shanshe/Z3660/z3660-firmware/Z-TURN/vitis_ide/Z3660_system/sd_card/README.txt

-= SD card boot image =-

Platform: design_1_wrapper
Application: design_1_wrapper

1. Copy the contents of this directory to an SD card
2. Set boot mode to SD
3. Insert SD card and turn board on
