shanshe/Z3660/z3660-board/Z3660_kicad/Z3660_kicad9-023/Sheet1.kicad_sch

## KiCad design z3660-board/Z3660_kicad/Z3660_kicad9-023/Sheet1.kicad_sch (2026-05-13)

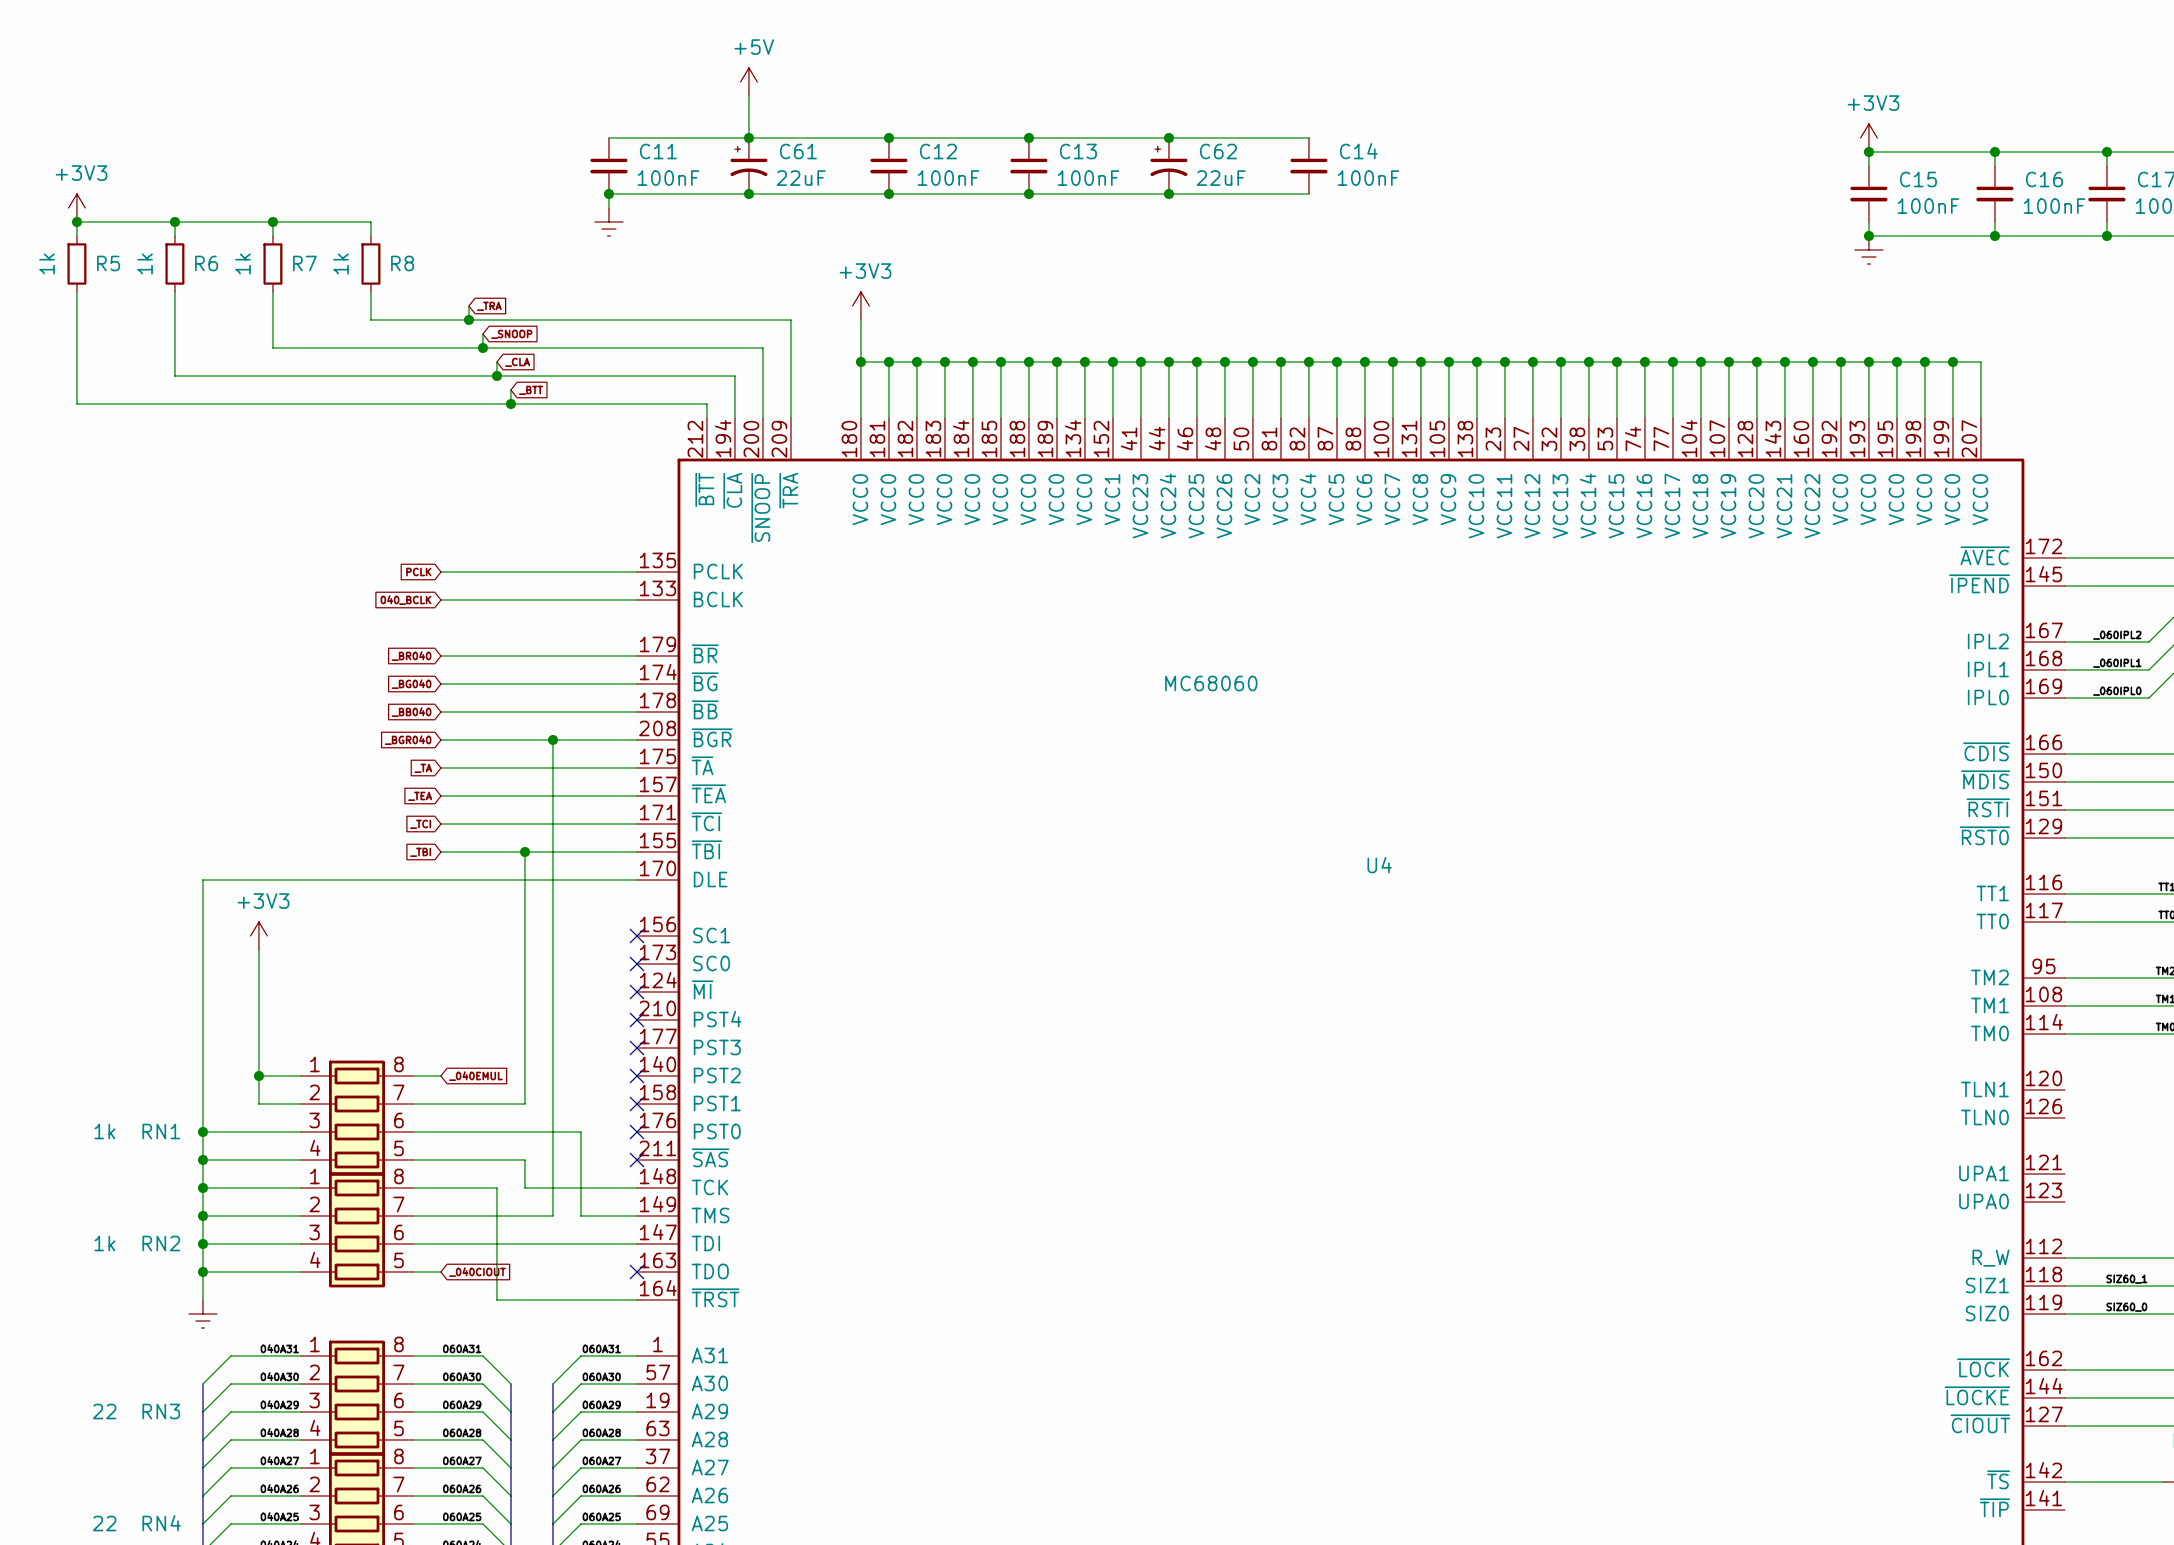
[picture p31: schematic Sheet1.kicad_sch, part in row 1, column 1]

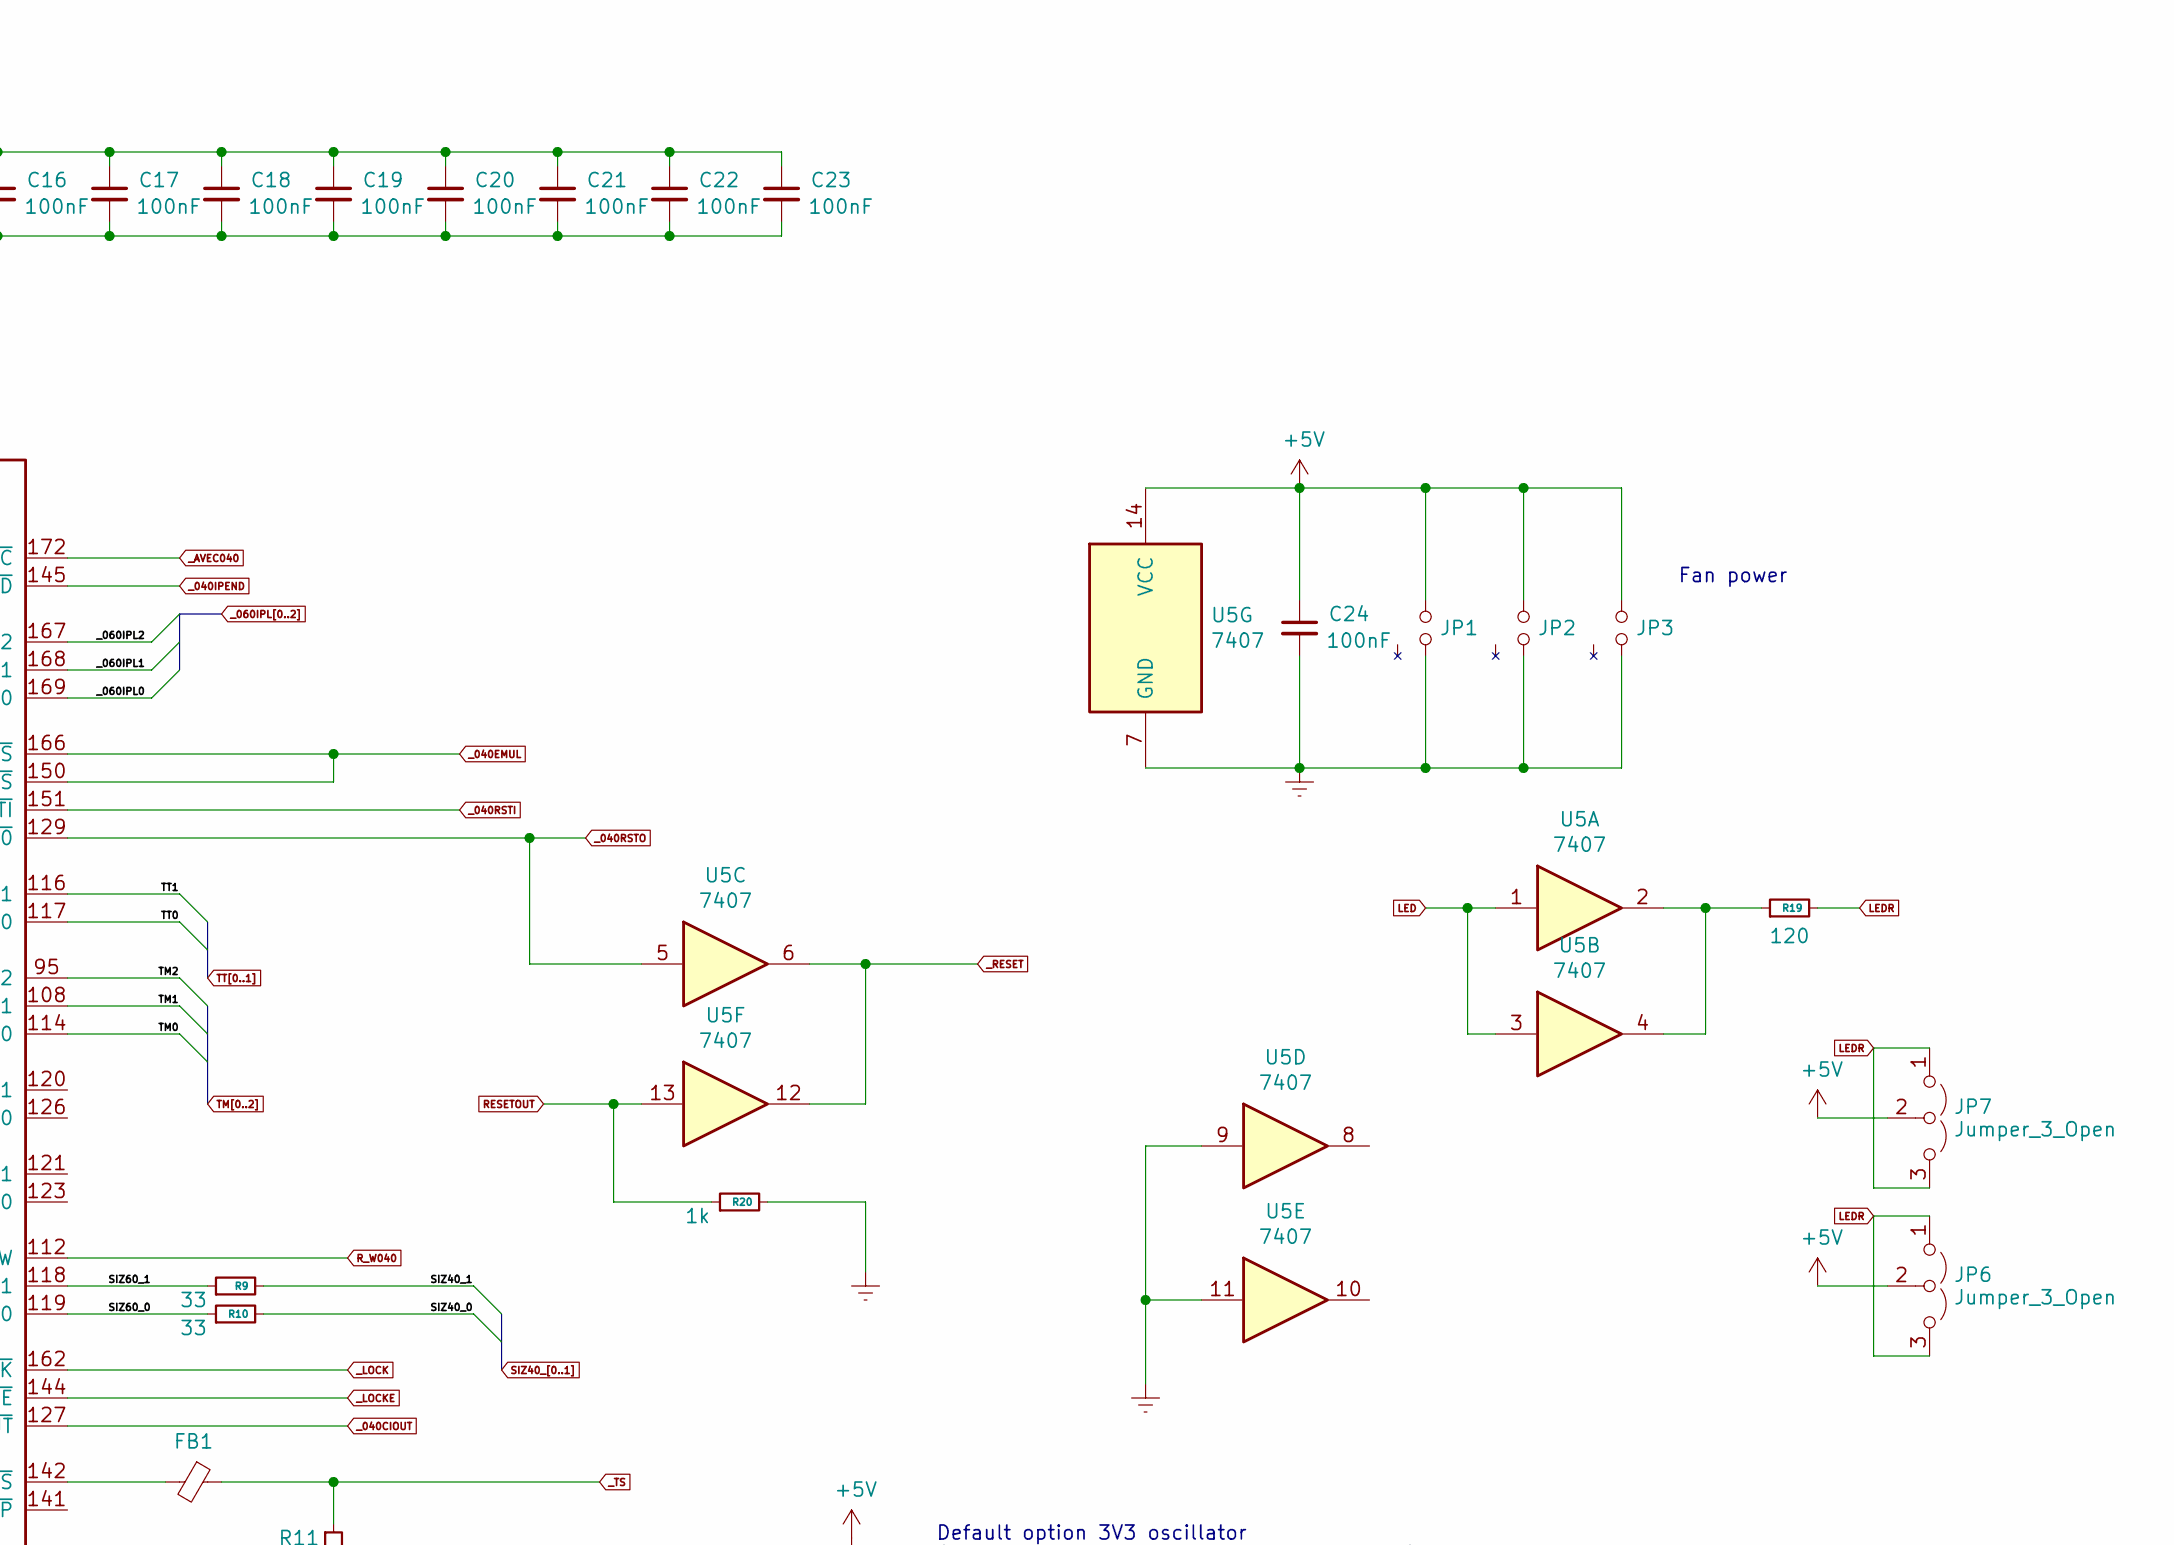
[picture p32: schematic Sheet1.kicad_sch, part in row 1, column 2]

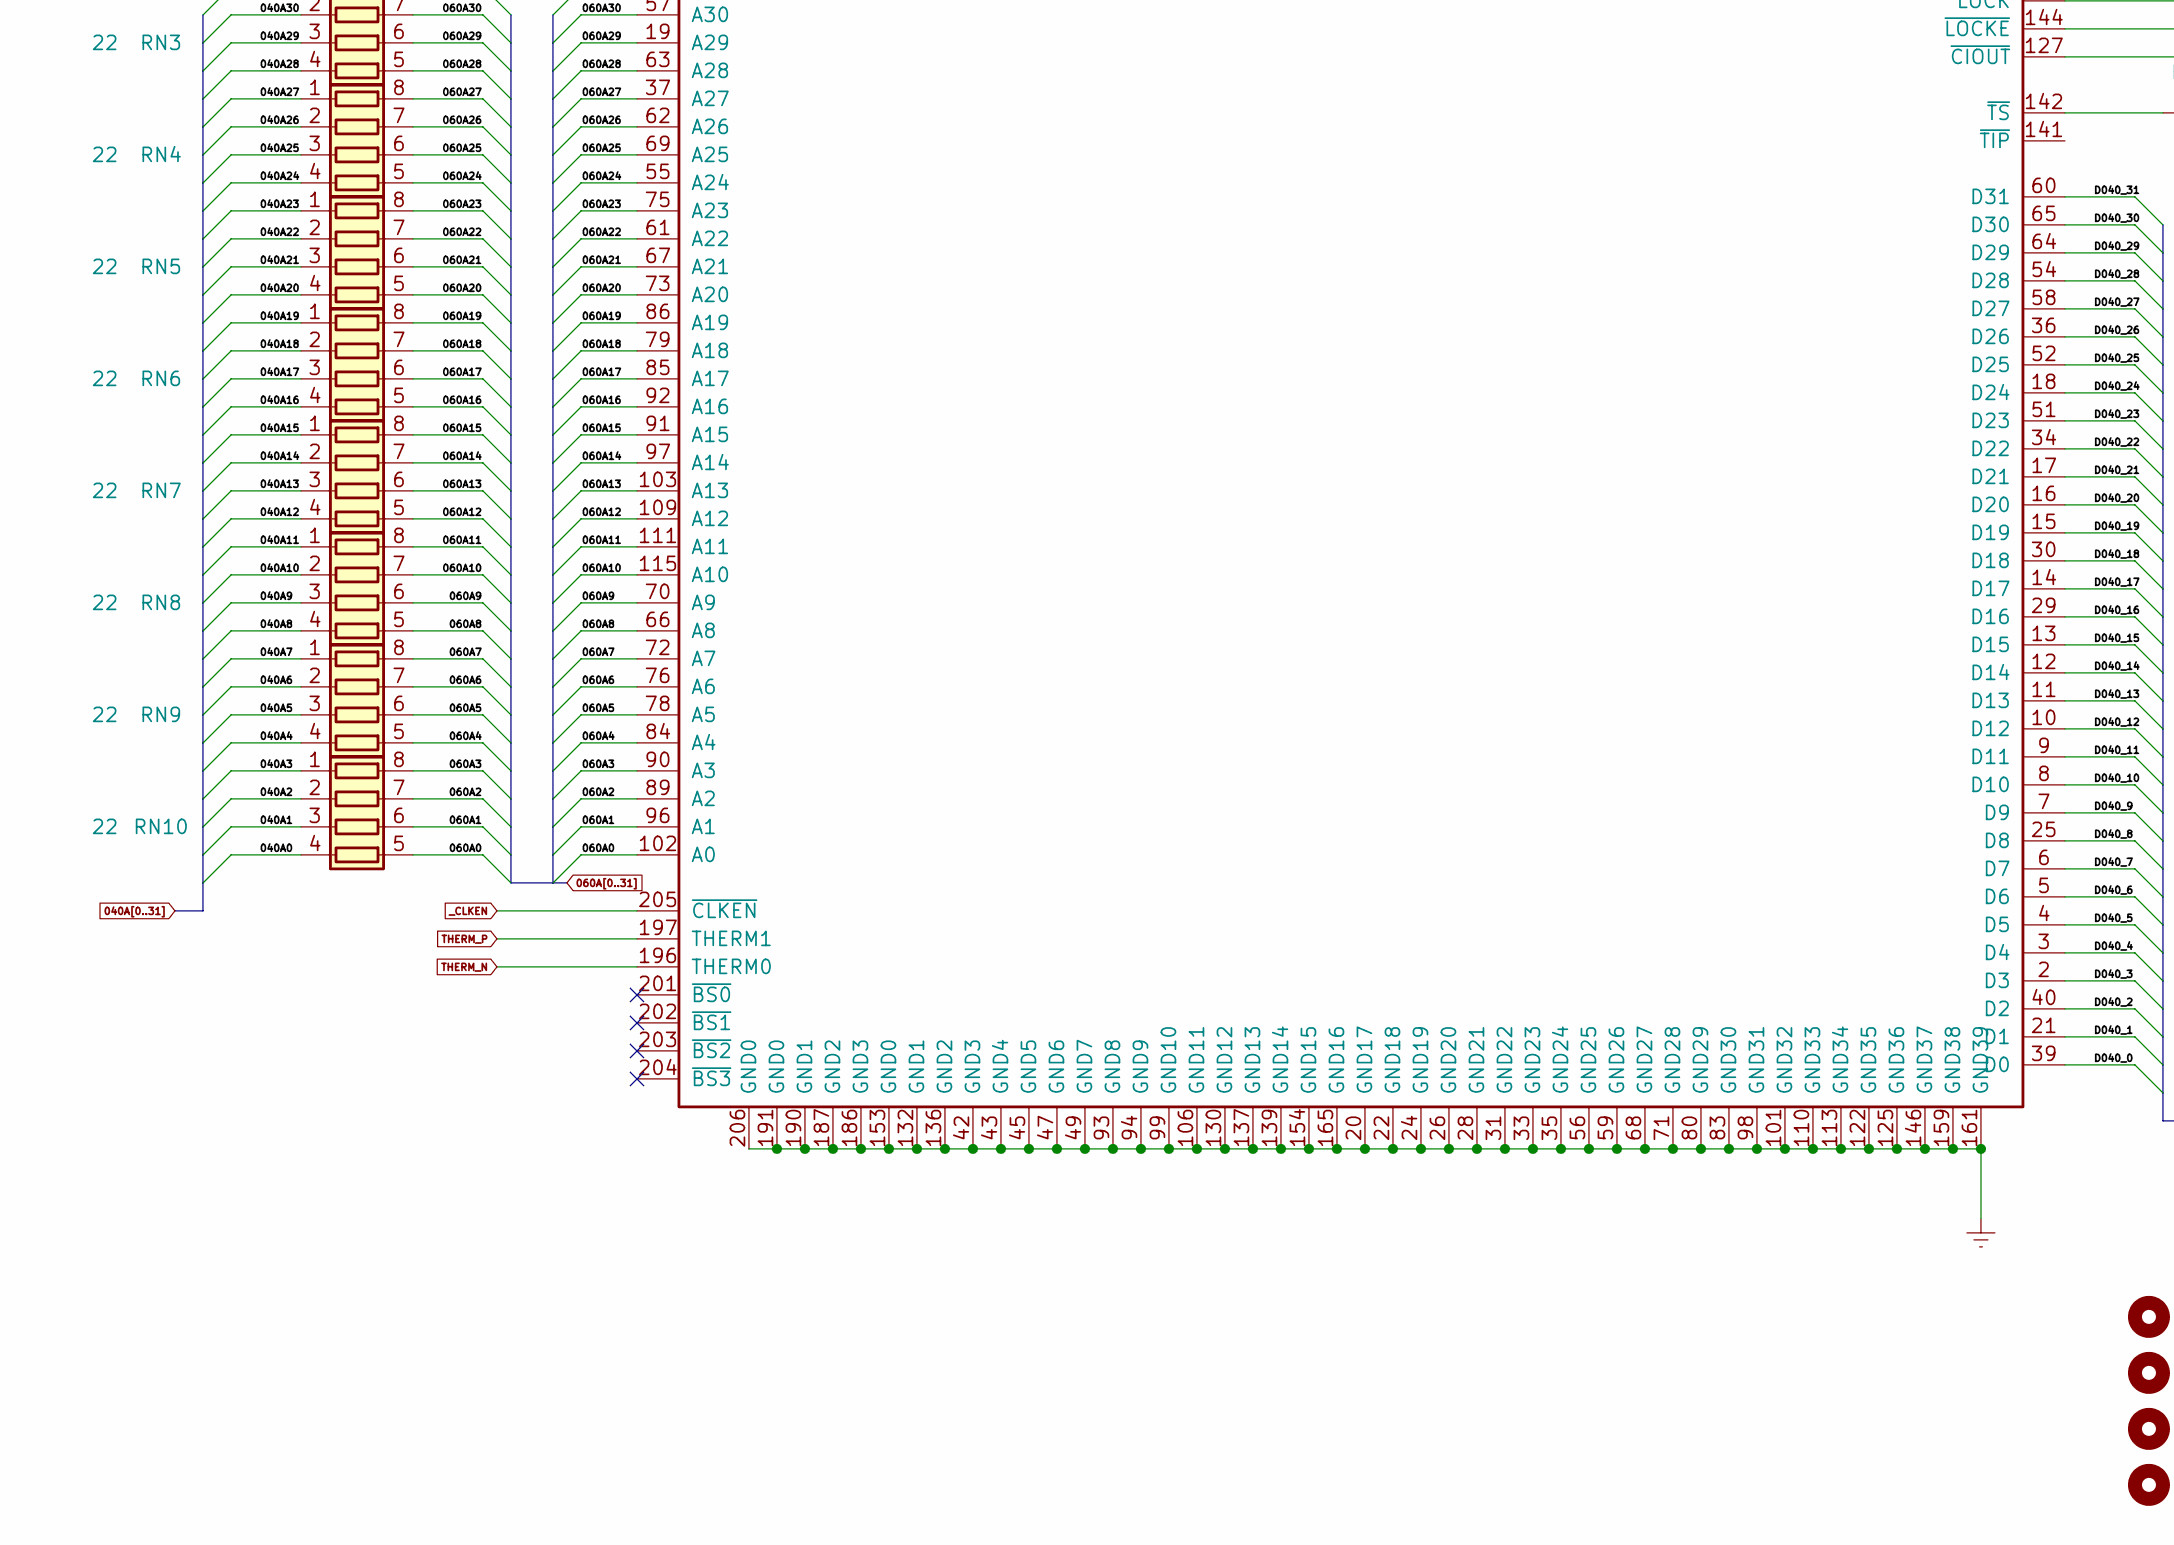
[picture p33: schematic Sheet1.kicad_sch, part in row 2, column 1]

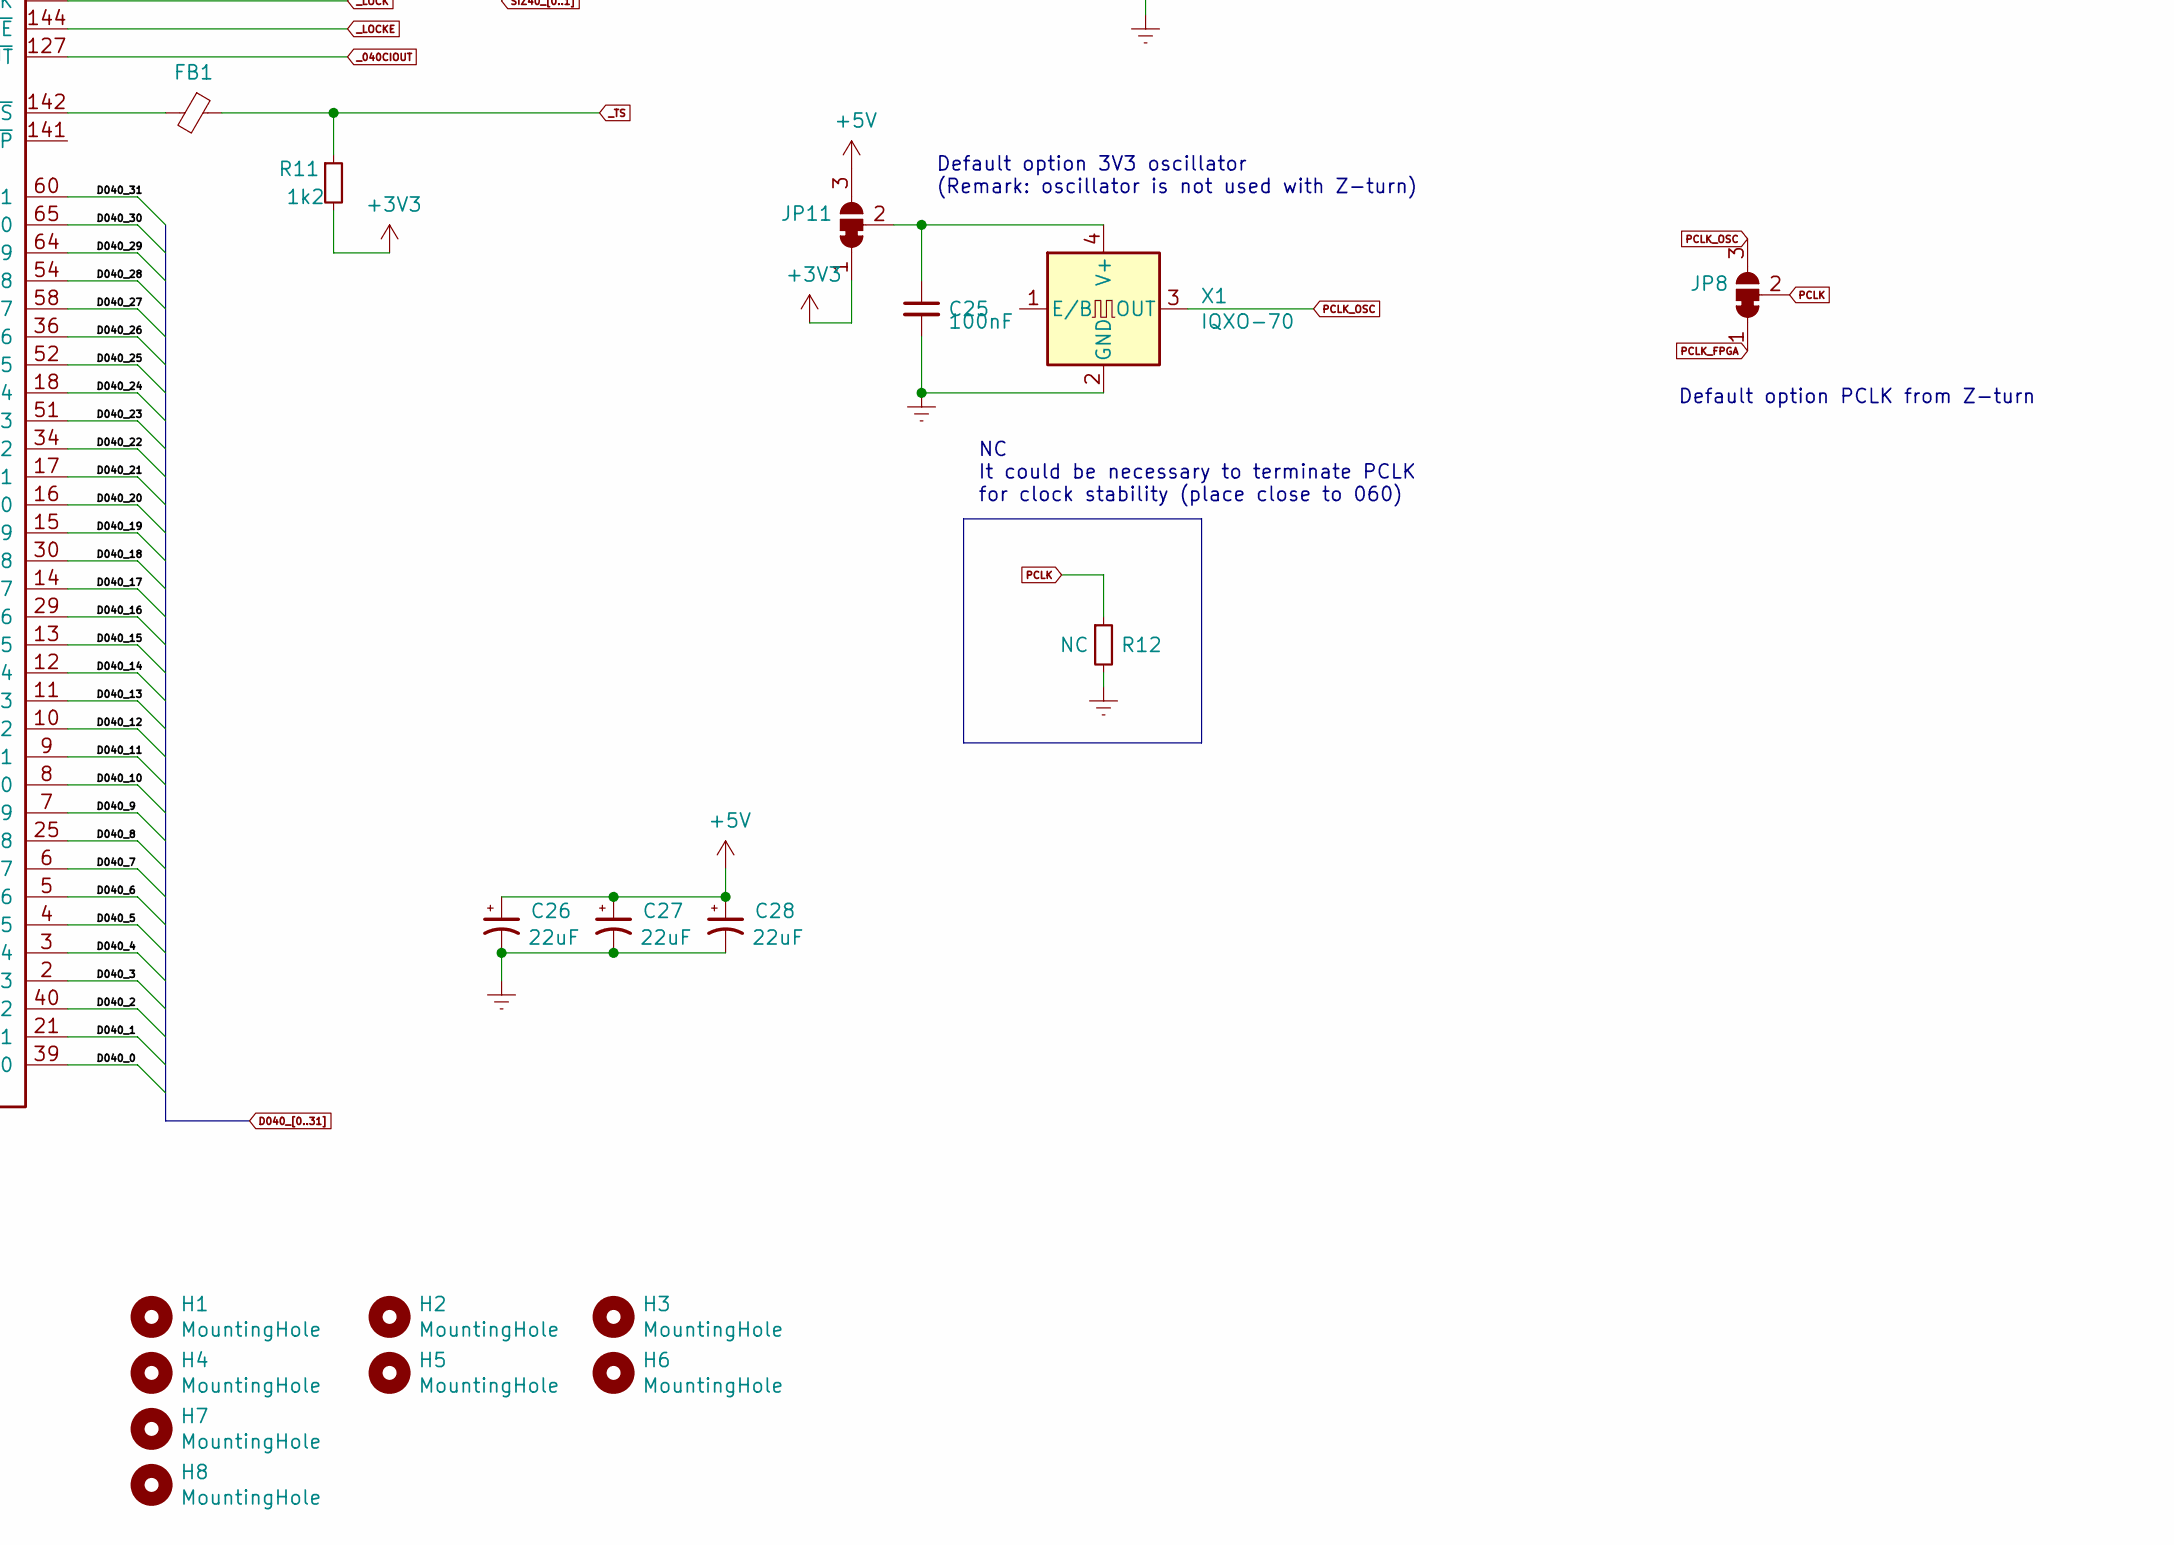
[picture p34: schematic Sheet1.kicad_sch, part in row 2, column 2]

Parts:
C11, C12, C13, C14, C15, C16, C17, C18, C19, C20, C21, C22, C23, C24, C25: 100nF; C_0805_2012Metric_Pad1.18x1.45mm_HandSolder
C26, C28, C61, C62: 22uF; CP_Elec_6.3x5.4
C27: 22uF; CP_Elec_6.3x3.9
FB1: Ferrite_Bead_Small; Fuse_1806_4516Metric_Pad1.57x1.80mm_HandSolder
H1, H2, H3, H4: MountingHole; MountingHole_4mm
H5, H6, H7, H8: MountingHole; MountingHole_2.2mm_M2
JP1, JP3: Jumper_NO_Small; PinHeader_1x03_P2.54mm_Horizontal
JP2, JP6, JP7: Jumper_3_Open; PinHeader_1x03_P2.54mm_Vertical
JP8, JP11: SolderJumper_3_Bridged12; SolderJumper-3_P1.3mm_Bridged12_RoundedPad1.0x1.5mm_NumberL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
R5, R6, R7, R8, R20: 1k; R_0805_2012Metric_Pad1.20x1.40mm_HandSolder
R9, R10: 33; R_0805_2012Metric_Pad1.20x1.40mm_HandSolder
R11: 1k2; R_0805_2012Metric_Pad1.20x1.40mm_HandSolder
R12: NC; R_0805_2012Metric_Pad1.20x1.40mm_HandSolder
R19: 120; R_0805_2012Metric_Pad1.20x1.40mm_HandSolder
RN1, RN2: 1k; R_Array_Convex_4x0603
RN3, RN4, RN5, RN6, RN7, RN8, RN9, RN10: 22; R_Array_Convex_4x0603
U4: MC68060; PGA226
U5: 7407; SOIC-14_3.9x8.7mm_P1.27mm
X1: IQXO-70; Oscillator_SMD_IQD_IQXO70-4Pin_7.5x5.0mm

Connections:
040A0: RN10.4 (R4.1)
040A1: RN10.3 (R3.1)
040A2: RN10.2 (R2.1)
040A3: RN10.1 (R1.1)
040A4: RN9.4 (R4.1)
040A5: RN9.3 (R3.1)
040A6: RN9.2 (R2.1)
040A7: RN9.1 (R1.1)
040A8: RN8.4 (R4.1)
040A9: RN8.3 (R3.1)
040A10: RN8.2 (R2.1)
040A11: RN8.1 (R1.1)
040A12: RN7.4 (R4.1)
040A13: RN7.3 (R3.1)
040A14: RN7.2 (R2.1)
040A15: RN7.1 (R1.1)
040A16: RN6.4 (R4.1)
040A17: RN6.3 (R3.1)
040A18: RN6.2 (R2.1)
040A19: RN6.1 (R1.1)
040A20: RN5.4 (R4.1)
040A21: RN5.3 (R3.1)
040A22: RN5.2 (R2.1)
040A23: RN5.1 (R1.1)
040A24: RN4.4 (R4.1)
040A25: RN4.3 (R3.1)
040A26: RN4.2 (R2.1)
040A27: RN4.1 (R1.1)
040A28: RN3.4 (R4.1)
040A29: RN3.3 (R3.1)
040A30: RN3.2 (R2.1)
040A31: RN3.1 (R1.1)
040_BCLK: U4.133 (BCLK)
060A0: RN10.5 (R4.2), U4.102 (A0)
060A1: RN10.6 (R3.2), U4.96 (A1)
060A2: RN10.7 (R2.2), U4.89 (A2)
060A3: RN10.8 (R1.2), U4.90 (A3)
060A4: RN9.5 (R4.2), U4.84 (A4)
060A5: RN9.6 (R3.2), U4.78 (A5)
060A6: RN9.7 (R2.2), U4.76 (A6)
060A7: RN9.8 (R1.2), U4.72 (A7)
060A8: RN8.5 (R4.2), U4.66 (A8)
060A9: RN8.6 (R3.2), U4.70 (A9)
060A10: RN8.7 (R2.2), U4.115 (A10)
060A11: RN8.8 (R1.2), U4.111 (A11)
060A12: RN7.5 (R4.2), U4.109 (A12)
060A13: RN7.6 (R3.2), U4.103 (A13)
060A14: RN7.7 (R2.2), U4.97 (A14)
060A15: RN7.8 (R1.2), U4.91 (A15)
060A16: RN6.5 (R4.2), U4.92 (A16)
060A17: RN6.6 (R3.2), U4.85 (A17)
060A18: RN6.7 (R2.2), U4.79 (A18)
060A19: RN6.8 (R1.2), U4.86 (A19)
060A20: RN5.5 (R4.2), U4.73 (A20)
060A21: RN5.6 (R3.2), U4.67 (A21)
060A22: RN5.7 (R2.2), U4.61 (A22)
060A23: RN5.8 (R1.2), U4.75 (A23)
060A24: RN4.5 (R4.2), U4.55 (A24)
060A25: RN4.6 (R3.2), U4.69 (A25)
060A26: RN4.7 (R2.2), U4.62 (A26)
060A27: RN4.8 (R1.2), U4.37 (A27)
060A28: RN3.5 (R4.2), U4.63 (A28)
060A29: RN3.6 (R3.2), U4.19 (A29)
060A30: RN3.7 (R2.2), U4.57 (A30)
060A31: RN3.8 (R1.2), U4.1 (A31)
+3V3: C15.1, C16.1, C17.1, C18.1, C19.1, C20.1, C21.1, C22.1, C23.1, JP11.1 (A), R5.1, R6.1, R7.1, R8.1, R11.2, RN1.1 (R1.1), RN1.2 (R2.1), U4.23 (VCC11), U4.27 (VCC12), U4.32 (VCC13), U4.38 (VCC14), U4.41 (VCC23), U4.44 (VCC24), U4.46 (VCC25), U4.48 (VCC26), U4.50 (VCC2), U4.53 (VCC15), U4.74 (VCC16), U4.77 (VCC17), U4.81 (VCC3), U4.82 (VCC4), U4.87 (VCC5), U4.88 (VCC6), U4.100 (VCC7), U4.104 (VCC18), U4.105 (VCC9), U4.107 (VCC19), U4.128 (VCC20), U4.131 (VCC8), U4.134 (VCC0), U4.138 (VCC10), U4.143 (VCC21), U4.152 (VCC1), U4.160 (VCC22), U4.180 (VCC0), U4.181 (VCC0), U4.182 (VCC0), U4.183 (VCC0), U4.184 (VCC0), U4.185 (VCC0), U4.188 (VCC0), U4.189 (VCC0), U4.192 (VCC0), U4.193 (VCC0), U4.195 (VCC0), U4.198 (VCC0), U4.199 (VCC0), U4.207 (VCC0)
+5V: C11.1, C12.1, C13.1, C14.1, C24.1, C26.1, C27.1, C28.1, C61.1, C62.1, JP1.2, JP2.2, JP3.2, JP6.2 (C), JP7.2 (C), JP11.3 (B), U5.14 (VCC)
D040_0: U4.39 (D0)
D040_1: U4.21 (D1)
D040_2: U4.40 (D2)
D040_3: U4.2 (D3)
D040_4: U4.3 (D4)
D040_5: U4.4 (D5)
D040_6: U4.5 (D6)
D040_7: U4.6 (D7)
D040_8: U4.25 (D8)
D040_9: U4.7 (D9)
D040_10: U4.8 (D10)
D040_11: U4.9 (D11)
D040_12: U4.10 (D12)
D040_13: U4.11 (D13)
D040_14: U4.12 (D14)
D040_15: U4.13 (D15)
D040_16: U4.29 (D16)
D040_17: U4.14 (D17)
D040_18: U4.30 (D18)
D040_19: U4.15 (D19)
D040_20: U4.16 (D20)
D040_21: U4.17 (D21)
D040_22: U4.34 (D22)
D040_23: U4.51 (D23)
D040_24: U4.18 (D24)
D040_25: U4.52 (D25)
D040_26: U4.36 (D26)
D040_27: U4.58 (D27)
D040_28: U4.54 (D28)
D040_29: U4.64 (D29)
D040_30: U4.65 (D30)
D040_31: U4.60 (D31)
Earth: C11.2, C12.2, C13.2, C14.2, C15.2, C16.2, C17.2, C18.2, C19.2, C20.2, C21.2, C22.2, C23.2, C24.2, C25.2, C26.2, C27.2, C28.2, C61.2, C62.2, JP1.1, JP2.1, JP3.1, R12.2, R20.2, RN1.3 (R3.1), RN1.4 (R4.1), RN2.1 (R1.1), RN2.2 (R2.1), RN2.3 (R3.1), RN2.4 (R4.1), U4.20 (GND17), U4.22 (GND18), U4.24 (GND19), U4.26 (GND20), U4.28 (GND21), U4.31 (GND22), U4.33 (GND23), U4.35 (GND24), U4.42 (GND3), U4.43 (GND4), U4.45 (GND5), U4.47 (GND6), U4.49 (GND7), U4.56 (GND25), U4.59 (GND26), U4.68 (GND27), U4.71 (GND28), U4.80 (GND29), U4.83 (GND30), U4.93 (GND8), U4.94 (GND9), U4.98 (GND31), U4.99 (GND10), U4.101 (GND32), U4.106 (GND11), U4.110 (GND33), U4.113 (GND34), U4.122 (GND35), U4.125 (GND36), U4.130 (GND12), U4.132 (GND1), U4.136 (GND2), U4.137 (GND13), U4.139 (GND14), U4.146 (GND37), U4.153 (GND0), U4.154 (GND15), U4.159 (GND38), U4.161 (GND39), U4.165 (GND16), U4.170 (DLE), U4.186 (GND3), U4.187 (GND2), U4.190 (GND1), U4.191 (GND0), U4.206 (GND0), U5.7 (GND), U5.9, U5.11, X1.2 (GND)
LED: U5.1, U5.3
LEDR: JP6.1 (A), JP6.3 (B), JP7.1 (A), JP7.3 (B), R19.2
unnamed: C25.1, JP11.2 (C), X1.4 (V+)
unnamed: FB1.2, U4.142 (~TS)
unnamed: R19.1, U5.2, U5.4
unnamed: RN1.5 (R4.2), U4.148 (TCK)
unnamed: RN1.6 (R3.2), U4.149 (TMS)
unnamed: RN2.6 (R3.2), U4.147 (TDI)
unnamed: RN2.8 (R1.2), U4.164 (~TRST)
PCLK: JP8.2 (C), R12.1, U4.135 (PCLK)
PCLK_FPGA: JP8.1 (A)
PCLK_OSC: JP8.3 (B), X1.3 (OUT)
RESETOUT: R20.1, U5.13
R_W040: U4.112 (R_W)
SIZ40_0: R10.2
SIZ40_1: R9.2
SIZ60_0: R10.1, U4.119 (SIZ0)
SIZ60_1: R9.1, U4.118 (SIZ1)
THERM_N: U4.196 (THERM0)
THERM_P: U4.197 (THERM1)
TM0: U4.114 (TM0)
TM1: U4.108 (TM1)
TM2: U4.95 (TM2)
TT0: U4.117 (TT0)
TT1: U4.116 (TT1)
_040CIOUT: RN2.5 (R4.2), U4.127 (~CIOUT)
_040EMUL: RN1.8 (R1.2), U4.150 (~MDIS), U4.166 (~CDIS)
_040IPEND: U4.145 (~IPEND)
_040RSTI: U4.151 (~RSTI)
_040RSTO: U4.129 (~RST0), U5.5
_060IPL0: U4.169 (IPL0)
_060IPL1: U4.168 (IPL1)
_060IPL2: U4.167 (IPL2)
_AVEC040: U4.172 (~AVEC)
_BB040: U4.178 (~BB)
_BG040: U4.174 (~BG)
_BGR040: RN2.7 (R2.2), U4.208 (~BGR)
_BR040: U4.179 (~BR)
_BTT: R5.2, U4.212 (~BTT)
_CLA: R6.2, U4.194 (~CLA)
_CLKEN: U4.205 (~CLKEN)
_LOCK: U4.162 (~LOCK)
_LOCKE: U4.144 (~LOCKE)
_RESET: U5.6, U5.12
_SNOOP: R7.2, U4.200 (~SNOOP)
_TA: U4.175 (~TA)
_TBI: RN1.7 (R2.2), U4.155 (~TBI)
_TCI: U4.171 (~TCI)
_TEA: U4.157 (~TEA)
_TRA: R8.2, U4.209 (~TRA)
_TS: FB1.1, R11.1

Notes on the sheet:
Default option 3V3 oscillator (Remark: oscillator is not used with Z-turn)
Default option PCLK from Z-turn
NC It could be necessary to terminate PCLK for clock stability (place close to 060)
Fan power
