shanshe/Z3660/z3660-board/Z3660_kicad/Z3660_kicad9-023/Sheet2.kicad_sch

## KiCad design z3660-board/Z3660_kicad/Z3660_kicad9-023/Sheet2.kicad_sch (2026-05-13)

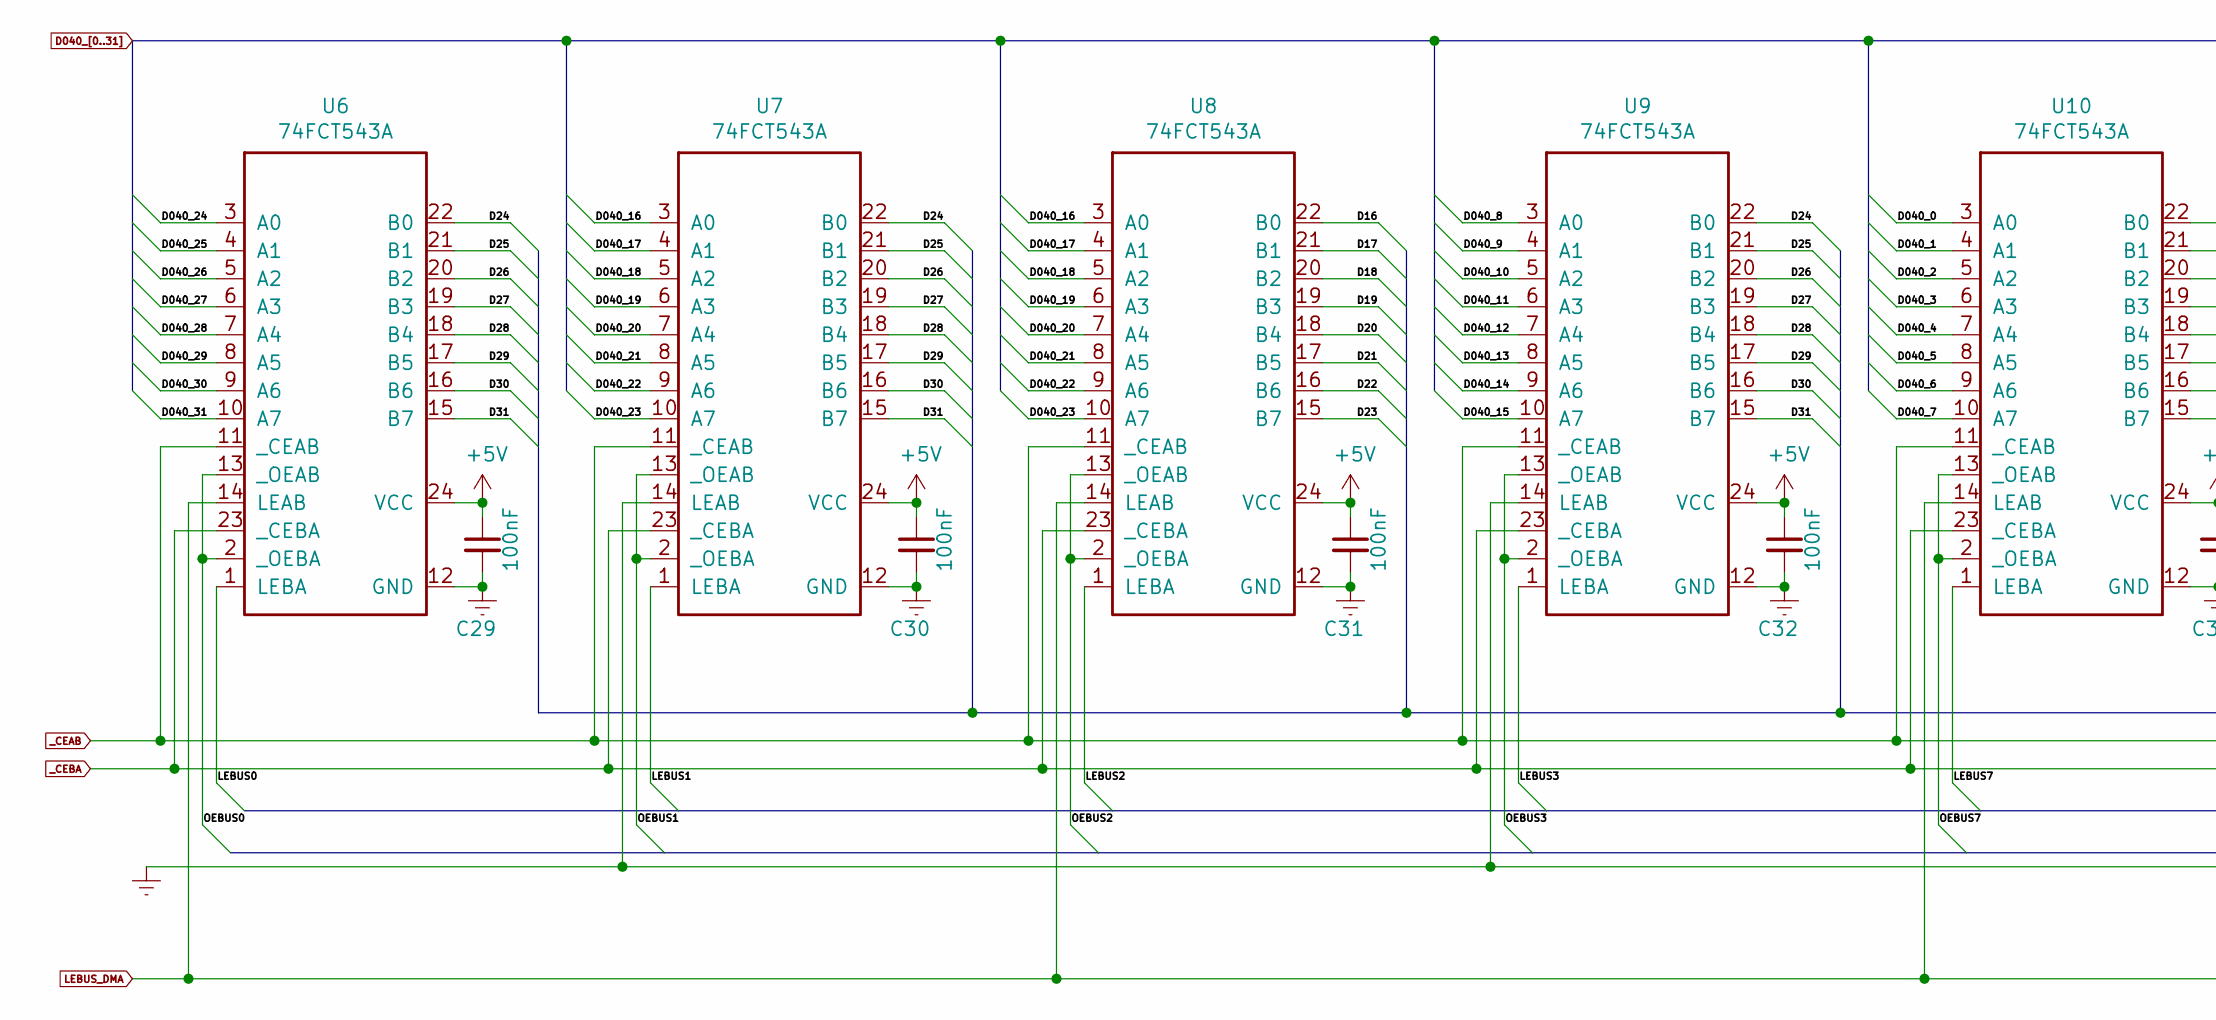
[picture p35: schematic Sheet2.kicad_sch, part in row 1, column 1]

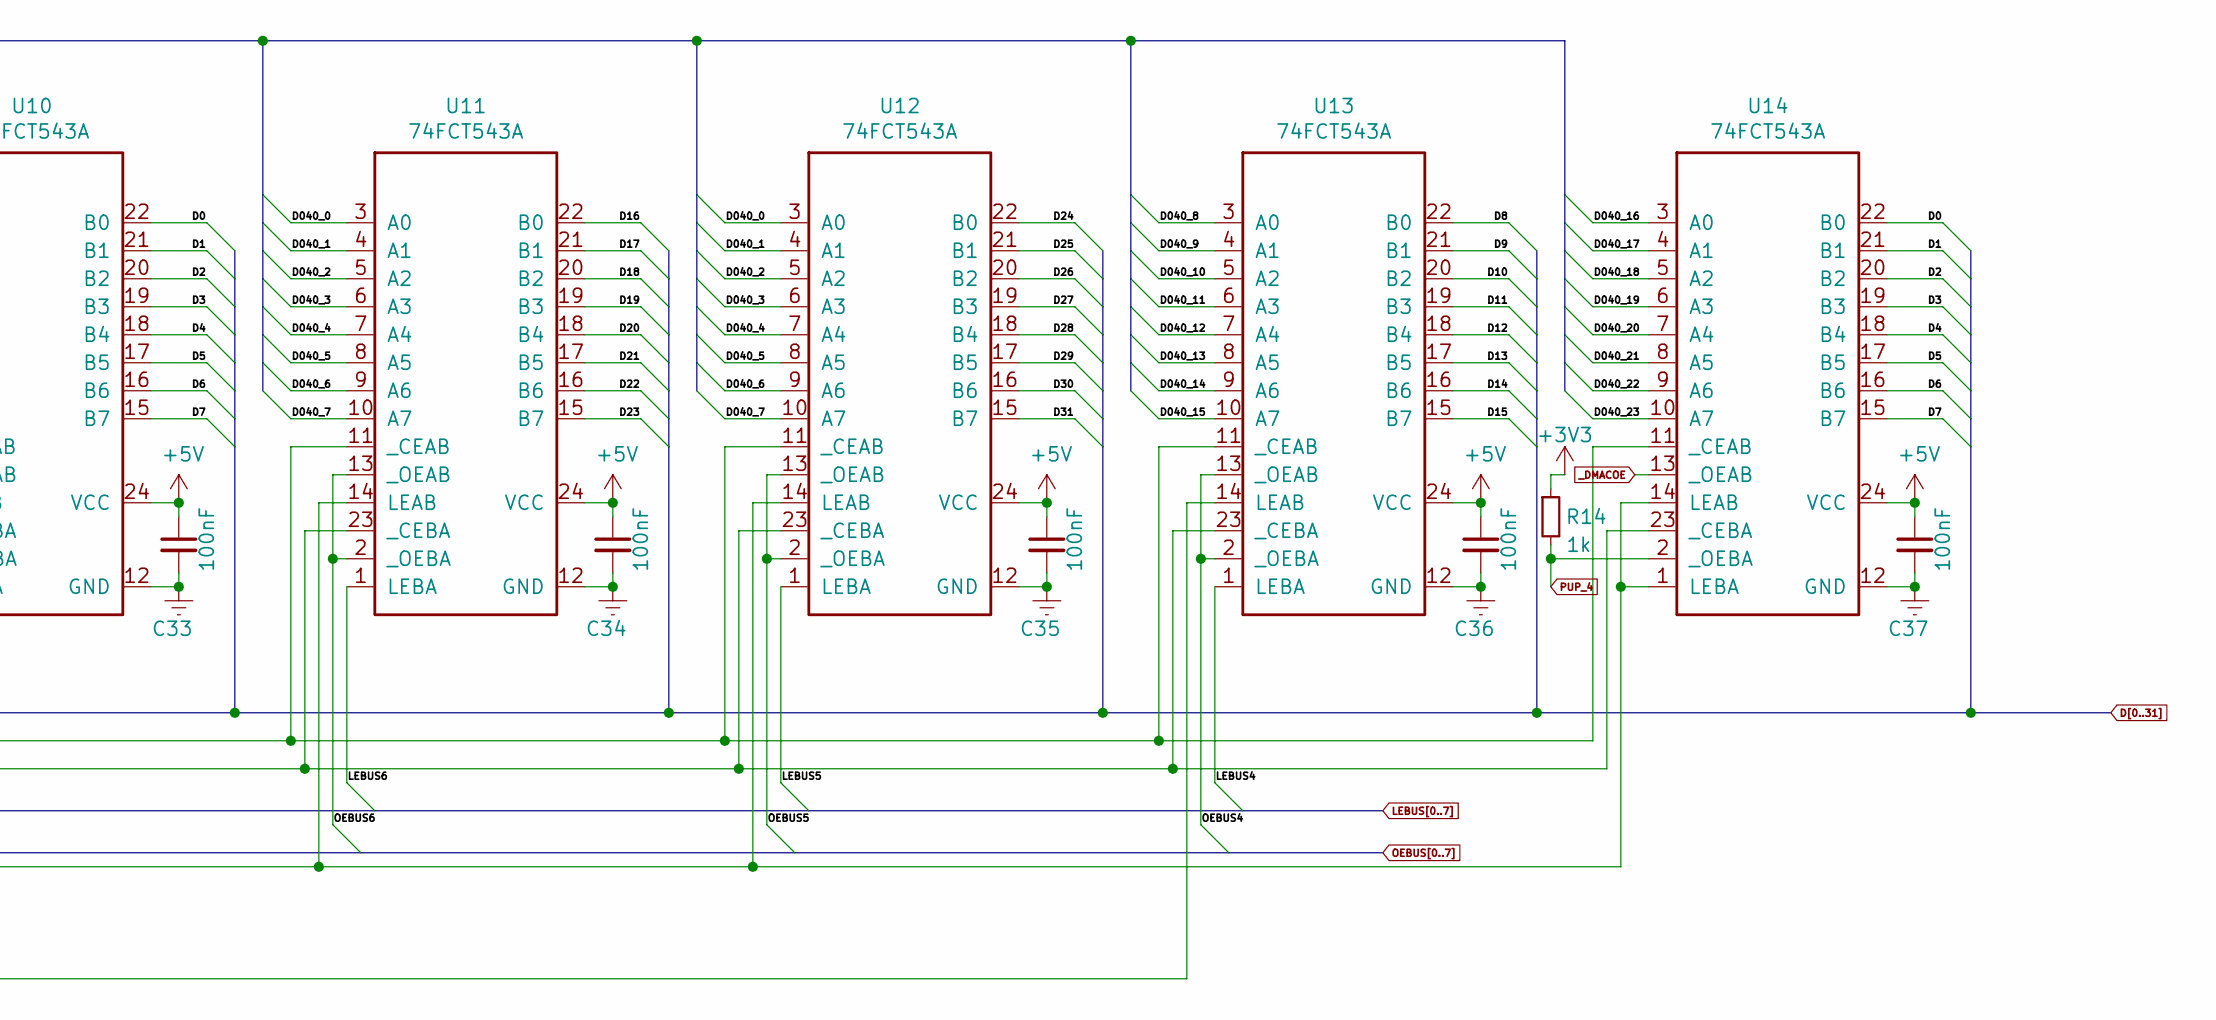
[picture p36: schematic Sheet2.kicad_sch, part in row 1, column 2]

Parts:
C29, C30, C31, C32, C33, C34, C35, C36, C37: 100nF; C_0805_2012Metric_Pad1.18x1.45mm_HandSolder
R14: 1k; R_0805_2012Metric_Pad1.20x1.40mm_HandSolder
U6, U7, U8, U9, U10, U11, U12, U13, U14: 74FCT543A; SOIC-24W_7.5x15.4mm_P1.27mm

Connections:
+3V3: R14.1
+5V: C29.1, C30.1, C31.1, C32.1, C33.1, C34.1, C35.1, C36.1, C37.1, U6.24 (VCC), U7.24 (VCC), U8.24 (VCC), U9.24 (VCC), U10.24 (VCC), U11.24 (VCC), U12.24 (VCC), U13.24 (VCC), U14.24 (VCC)
D0: U10.22 (B0), U14.22 (B0)
D1: U10.21 (B1), U14.21 (B1)
D2: U10.20 (B2), U14.20 (B2)
D3: U10.19 (B3), U14.19 (B3)
D4: U10.18 (B4), U14.18 (B4)
D5: U10.17 (B5), U14.17 (B5)
D6: U10.16 (B6), U14.16 (B6)
D7: U10.15 (B7), U14.15 (B7)
D8: U13.22 (B0)
D9: U13.21 (B1)
D10: U13.20 (B2)
D11: U13.19 (B3)
D12: U13.18 (B4)
D13: U13.17 (B5)
D14: U13.16 (B6)
D15: U13.15 (B7)
D16: U8.22 (B0), U11.22 (B0)
D17: U8.21 (B1), U11.21 (B1)
D18: U8.20 (B2), U11.20 (B2)
D19: U8.19 (B3), U11.19 (B3)
D20: U8.18 (B4), U11.18 (B4)
D21: U8.17 (B5), U11.17 (B5)
D22: U8.16 (B6), U11.16 (B6)
D23: U8.15 (B7), U11.15 (B7)
D24: U6.22 (B0), U7.22 (B0), U9.22 (B0), U12.22 (B0)
D25: U6.21 (B1), U7.21 (B1), U9.21 (B1), U12.21 (B1)
D26: U6.20 (B2), U7.20 (B2), U9.20 (B2), U12.20 (B2)
D27: U6.19 (B3), U7.19 (B3), U9.19 (B3), U12.19 (B3)
D28: U6.18 (B4), U7.18 (B4), U9.18 (B4), U12.18 (B4)
D29: U6.17 (B5), U7.17 (B5), U9.17 (B5), U12.17 (B5)
D30: U6.16 (B6), U7.16 (B6), U9.16 (B6), U12.16 (B6)
D31: U6.15 (B7), U7.15 (B7), U9.15 (B7), U12.15 (B7)
D040_0: U10.3 (A0), U11.3 (A0), U12.3 (A0)
D040_1: U10.4 (A1), U11.4 (A1), U12.4 (A1)
D040_2: U10.5 (A2), U11.5 (A2), U12.5 (A2)
D040_3: U10.6 (A3), U11.6 (A3), U12.6 (A3)
D040_4: U10.7 (A4), U11.7 (A4), U12.7 (A4)
D040_5: U10.8 (A5), U11.8 (A5), U12.8 (A5)
D040_6: U10.9 (A6), U11.9 (A6), U12.9 (A6)
D040_7: U10.10 (A7), U11.10 (A7), U12.10 (A7)
D040_8: U9.3 (A0), U13.3 (A0)
D040_9: U9.4 (A1), U13.4 (A1)
D040_10: U9.5 (A2), U13.5 (A2)
D040_11: U9.6 (A3), U13.6 (A3)
D040_12: U9.7 (A4), U13.7 (A4)
D040_13: U9.8 (A5), U13.8 (A5)
D040_14: U9.9 (A6), U13.9 (A6)
D040_15: U9.10 (A7), U13.10 (A7)
D040_16: U7.3 (A0), U8.3 (A0), U14.3 (A0)
D040_17: U7.4 (A1), U8.4 (A1), U14.4 (A1)
D040_18: U7.5 (A2), U8.5 (A2), U14.5 (A2)
D040_19: U7.6 (A3), U8.6 (A3), U14.6 (A3)
D040_20: U7.7 (A4), U8.7 (A4), U14.7 (A4)
D040_21: U7.8 (A5), U8.8 (A5), U14.8 (A5)
D040_22: U7.9 (A6), U8.9 (A6), U14.9 (A6)
D040_23: U7.10 (A7), U8.10 (A7), U14.10 (A7)
D040_24: U6.3 (A0)
D040_25: U6.4 (A1)
D040_26: U6.5 (A2)
D040_27: U6.6 (A3)
D040_28: U6.7 (A4)
D040_29: U6.8 (A5)
D040_30: U6.9 (A6)
D040_31: U6.10 (A7)
Earth: C29.2, C30.2, C31.2, C32.2, C33.2, C34.2, C35.2, C36.2, C37.2, U6.12 (GND), U7.12 (GND), U7.14 (LEAB), U8.12 (GND), U9.12 (GND), U9.14 (LEAB), U10.12 (GND), U11.12 (GND), U11.14 (LEAB), U12.12 (GND), U12.14 (LEAB), U13.12 (GND), U14.1 (LEBA), U14.12 (GND), U14.14 (LEAB)
LEBUS0: U6.1 (LEBA)
LEBUS1: U7.1 (LEBA)
LEBUS2: U8.1 (LEBA)
LEBUS3: U9.1 (LEBA)
LEBUS4: U13.1 (LEBA)
LEBUS5: U12.1 (LEBA)
LEBUS6: U11.1 (LEBA)
LEBUS7: U10.1 (LEBA)
LEBUS_DMA: U6.14 (LEAB), U8.14 (LEAB), U10.14 (LEAB), U13.14 (LEAB)
OEBUS0: U6.2 (_OEBA), U6.13 (_OEAB)
OEBUS1: U7.2 (_OEBA), U7.13 (_OEAB)
OEBUS2: U8.2 (_OEBA), U8.13 (_OEAB)
OEBUS3: U9.2 (_OEBA), U9.13 (_OEAB)
OEBUS4: U13.2 (_OEBA), U13.13 (_OEAB)
OEBUS5: U12.2 (_OEBA), U12.13 (_OEAB)
OEBUS6: U11.2 (_OEBA), U11.13 (_OEAB)
OEBUS7: U10.2 (_OEBA), U10.13 (_OEAB)
PUP_4: R14.2, U14.2 (_OEBA)
_CEAB: U6.11 (_CEAB), U7.11 (_CEAB), U8.11 (_CEAB), U9.11 (_CEAB), U10.11 (_CEAB), U11.11 (_CEAB), U12.11 (_CEAB), U13.11 (_CEAB), U14.11 (_CEAB)
_CEBA: U6.23 (_CEBA), U7.23 (_CEBA), U8.23 (_CEBA), U9.23 (_CEBA), U10.23 (_CEBA), U11.23 (_CEBA), U12.23 (_CEBA), U13.23 (_CEBA), U14.23 (_CEBA)
_DMACOE: U14.13 (_OEAB)
