shanshe/Z3660/z3660-board/Z3660_kicad/Z3660_kicad9-023/Sheet3.kicad_sch

## KiCad design z3660-board/Z3660_kicad/Z3660_kicad9-023/Sheet3.kicad_sch (2026-05-13)

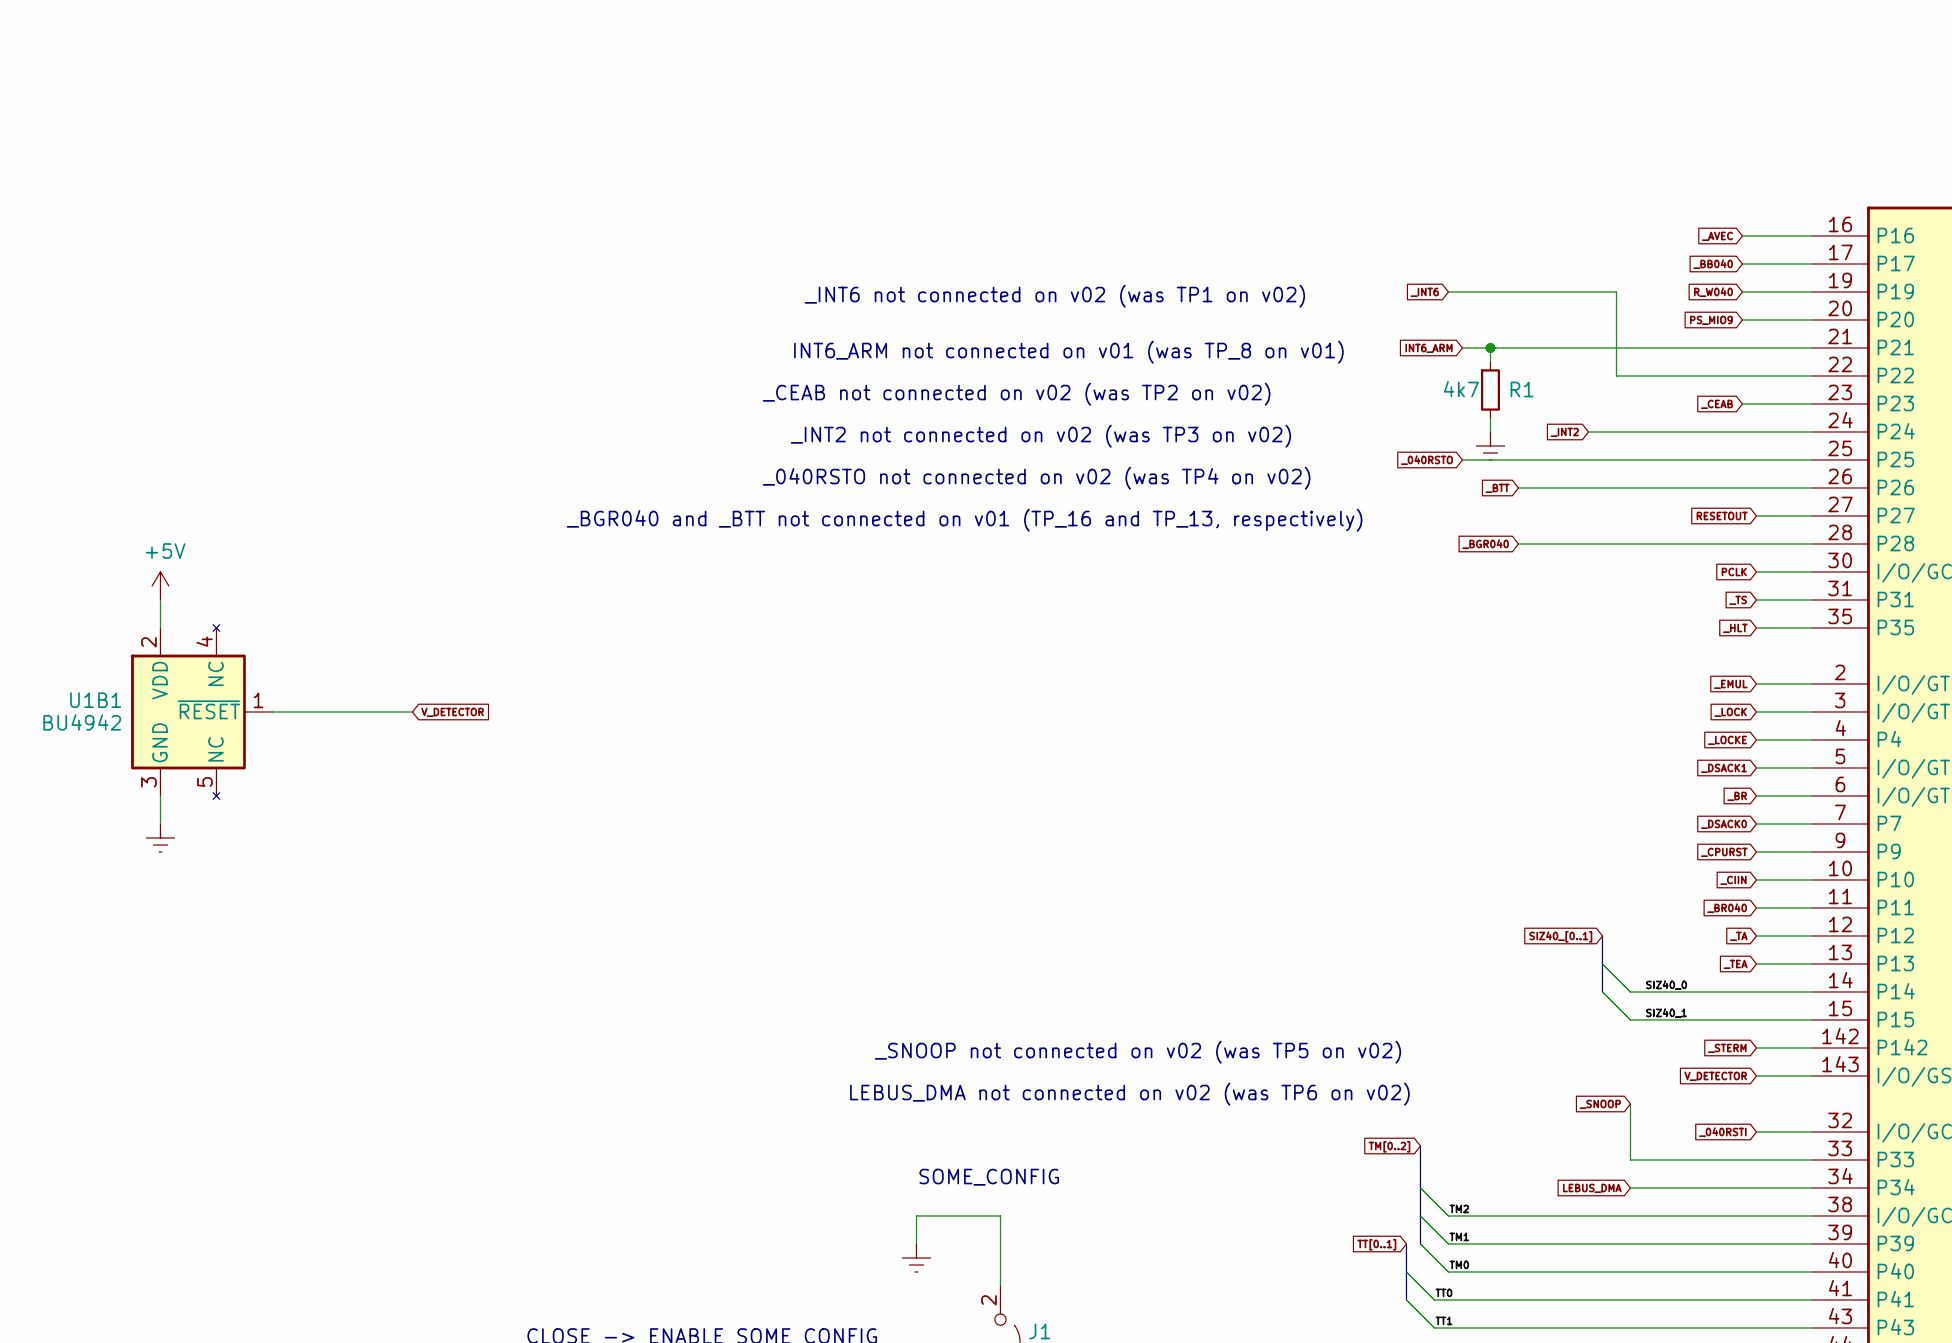
[picture p37: schematic Sheet3.kicad_sch, part in row 1, column 1]

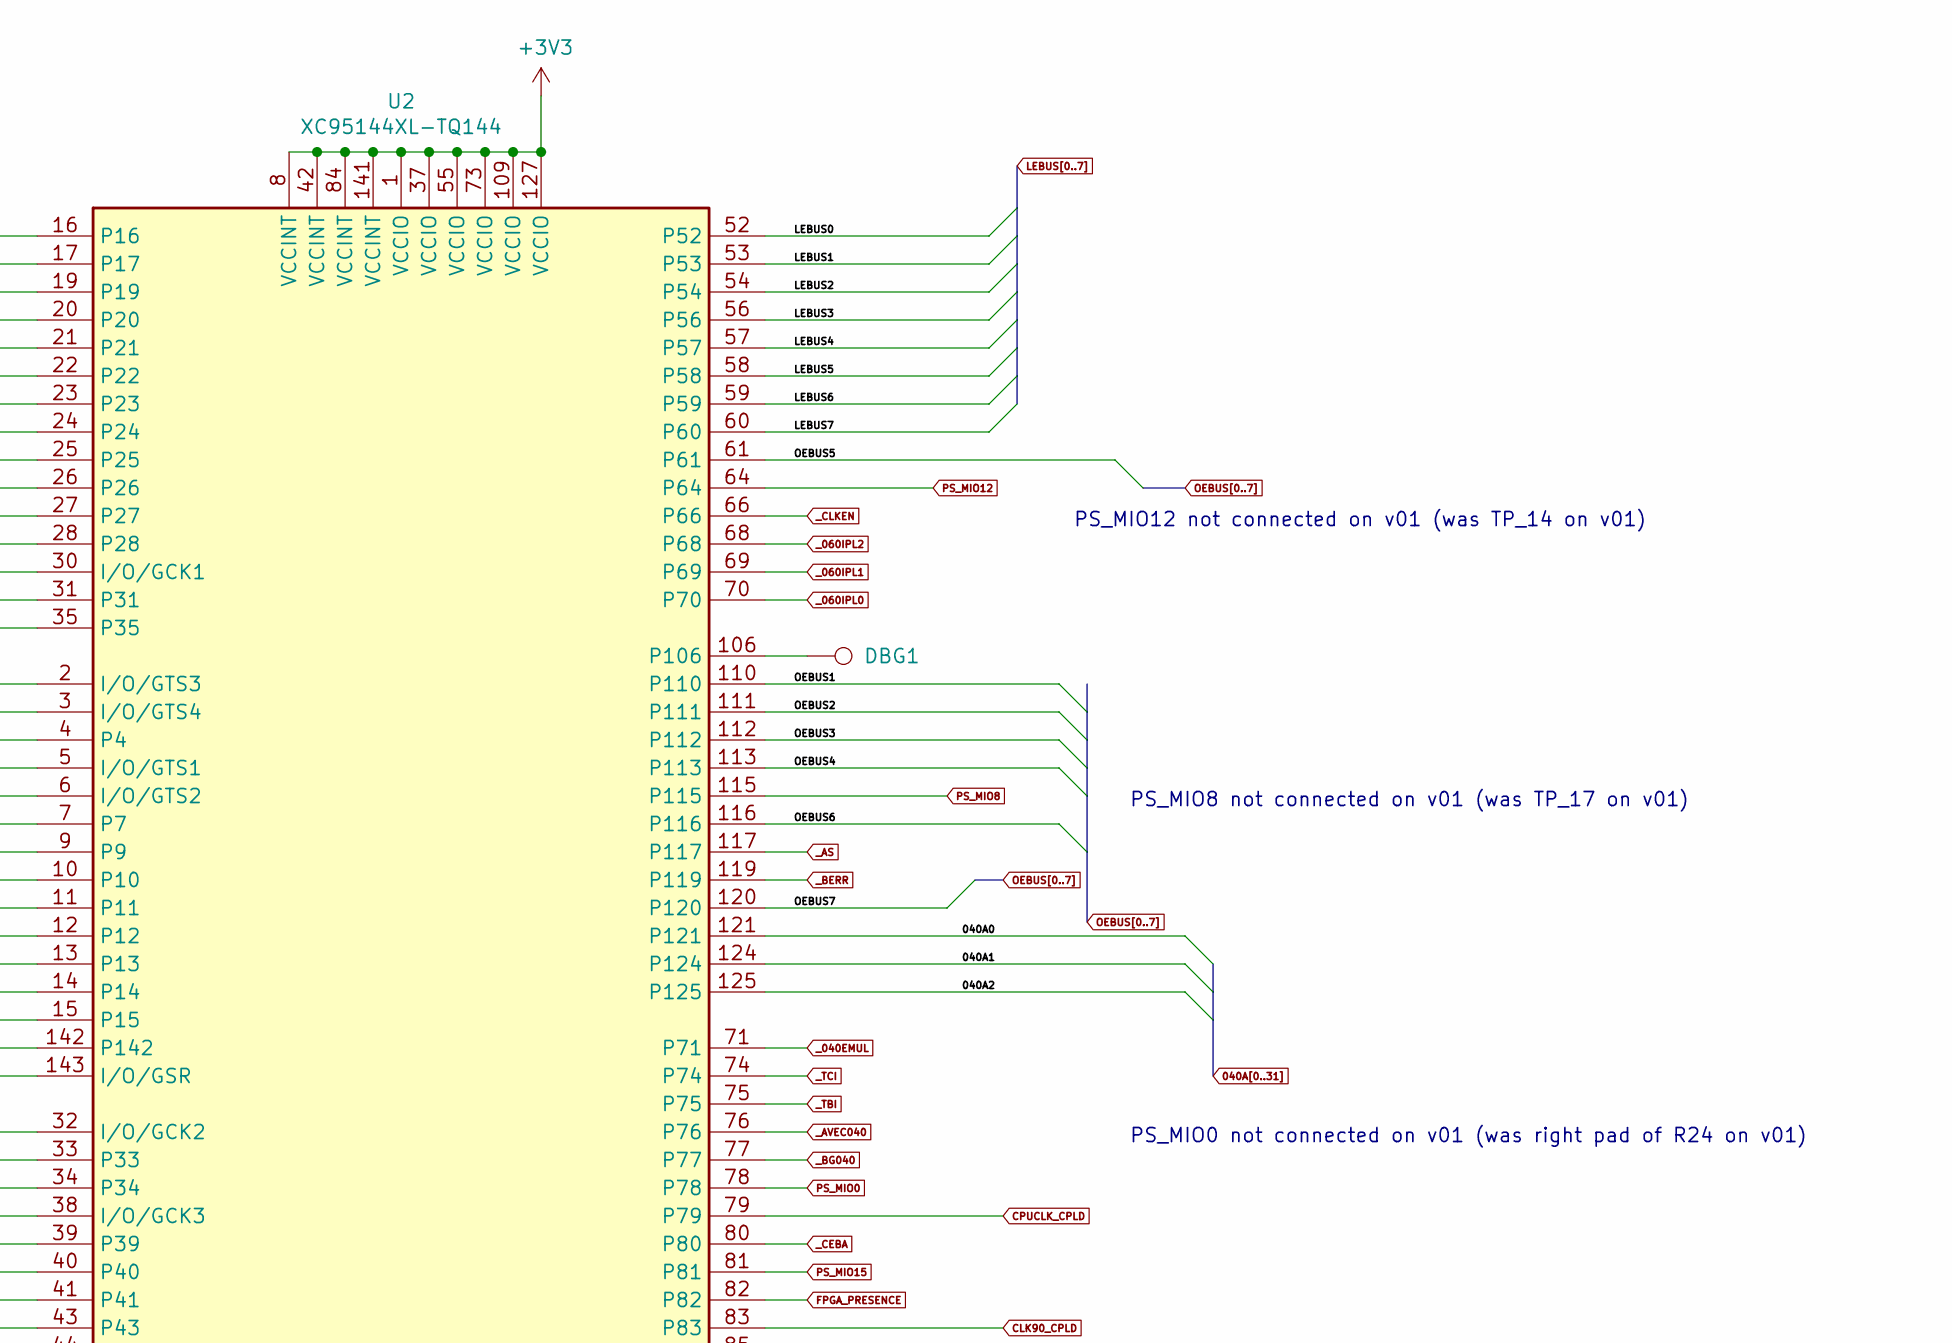
[picture p38: schematic Sheet3.kicad_sch, part in row 1, column 2]

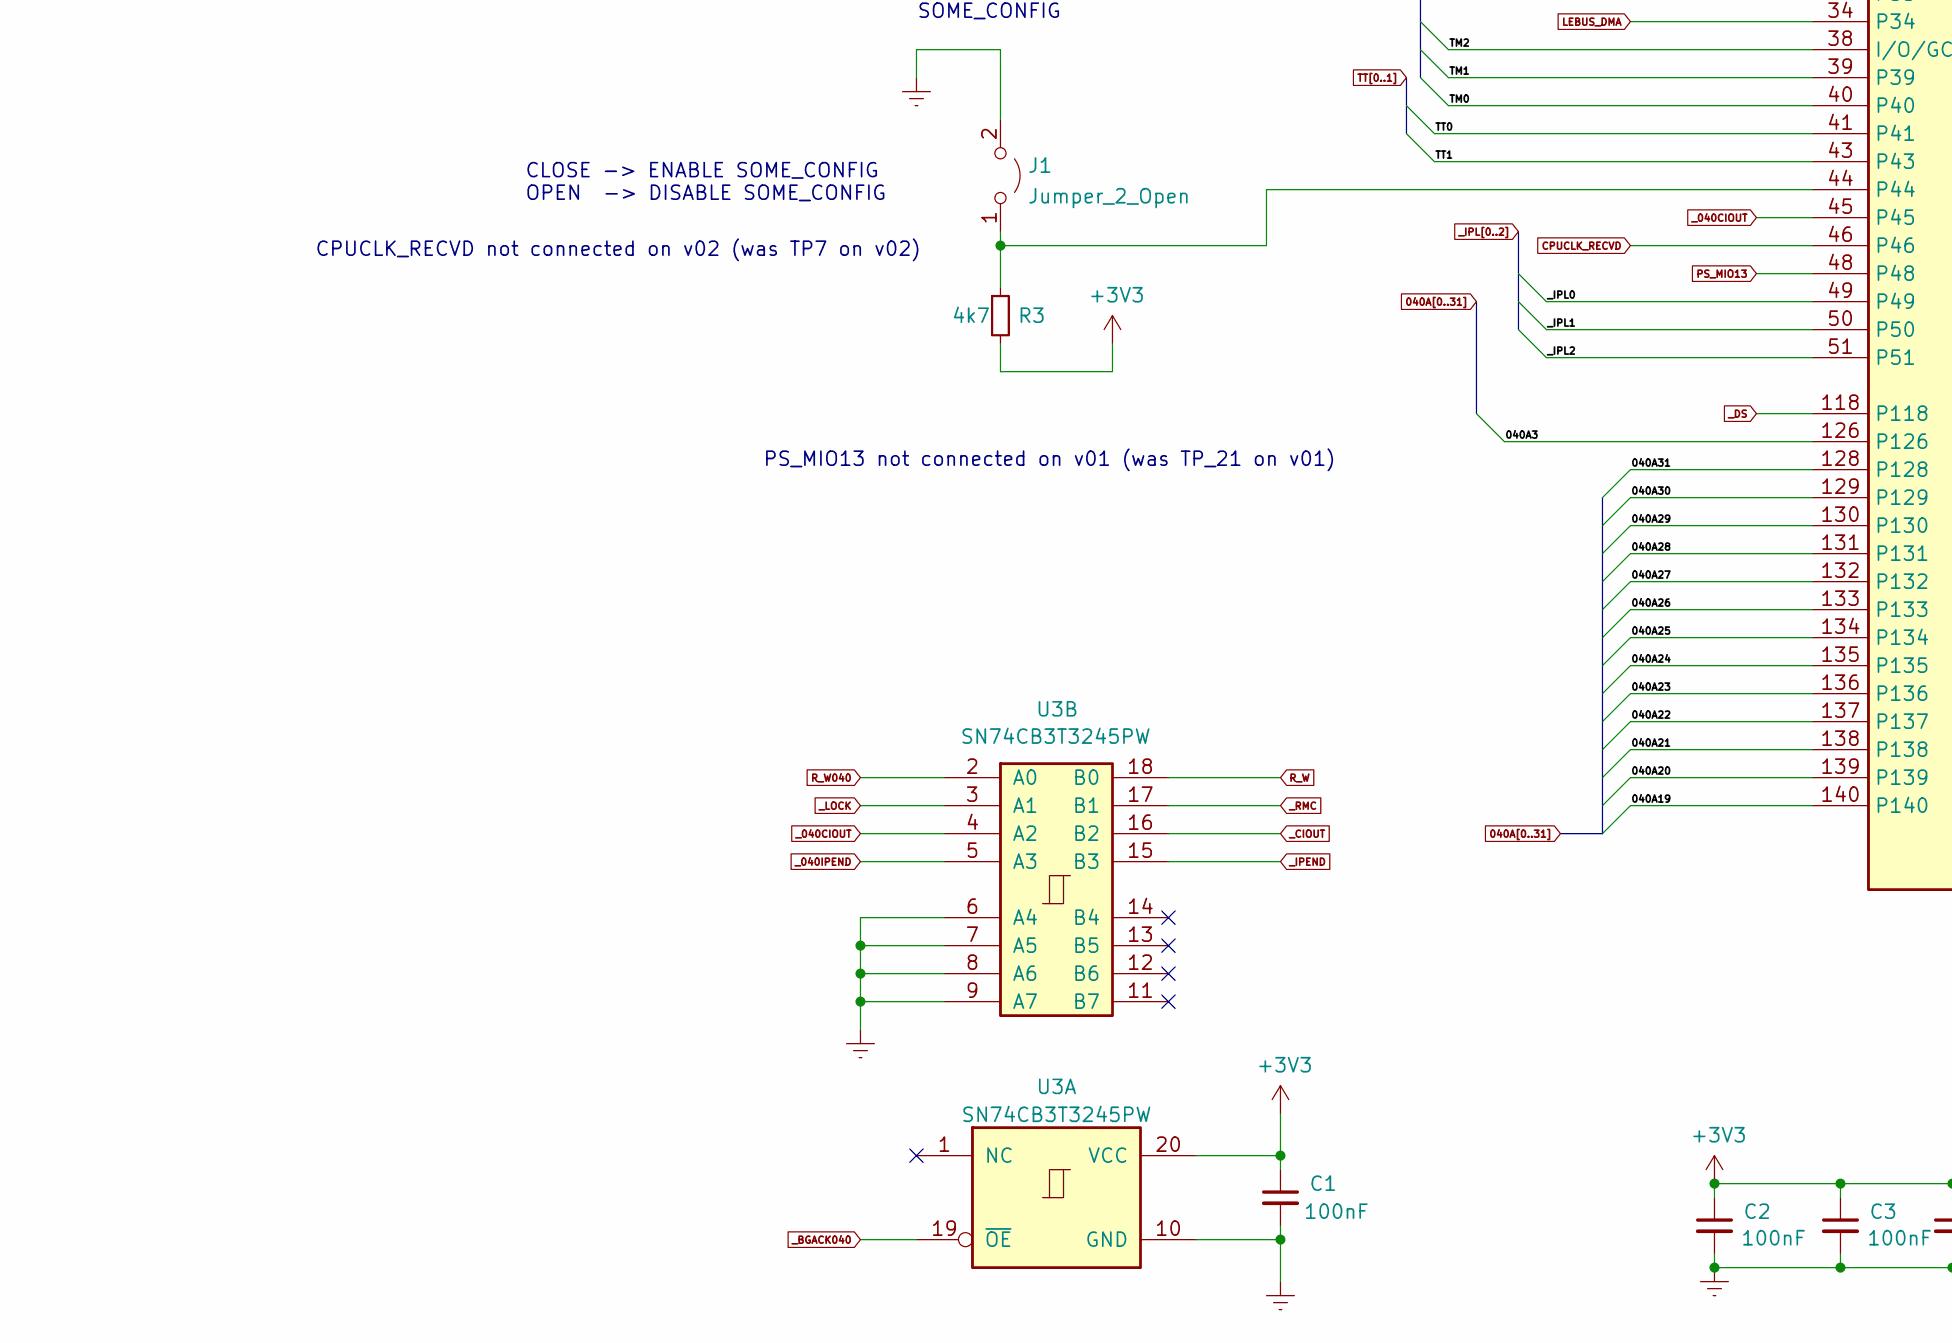
[picture p39: schematic Sheet3.kicad_sch, part in row 2, column 1]

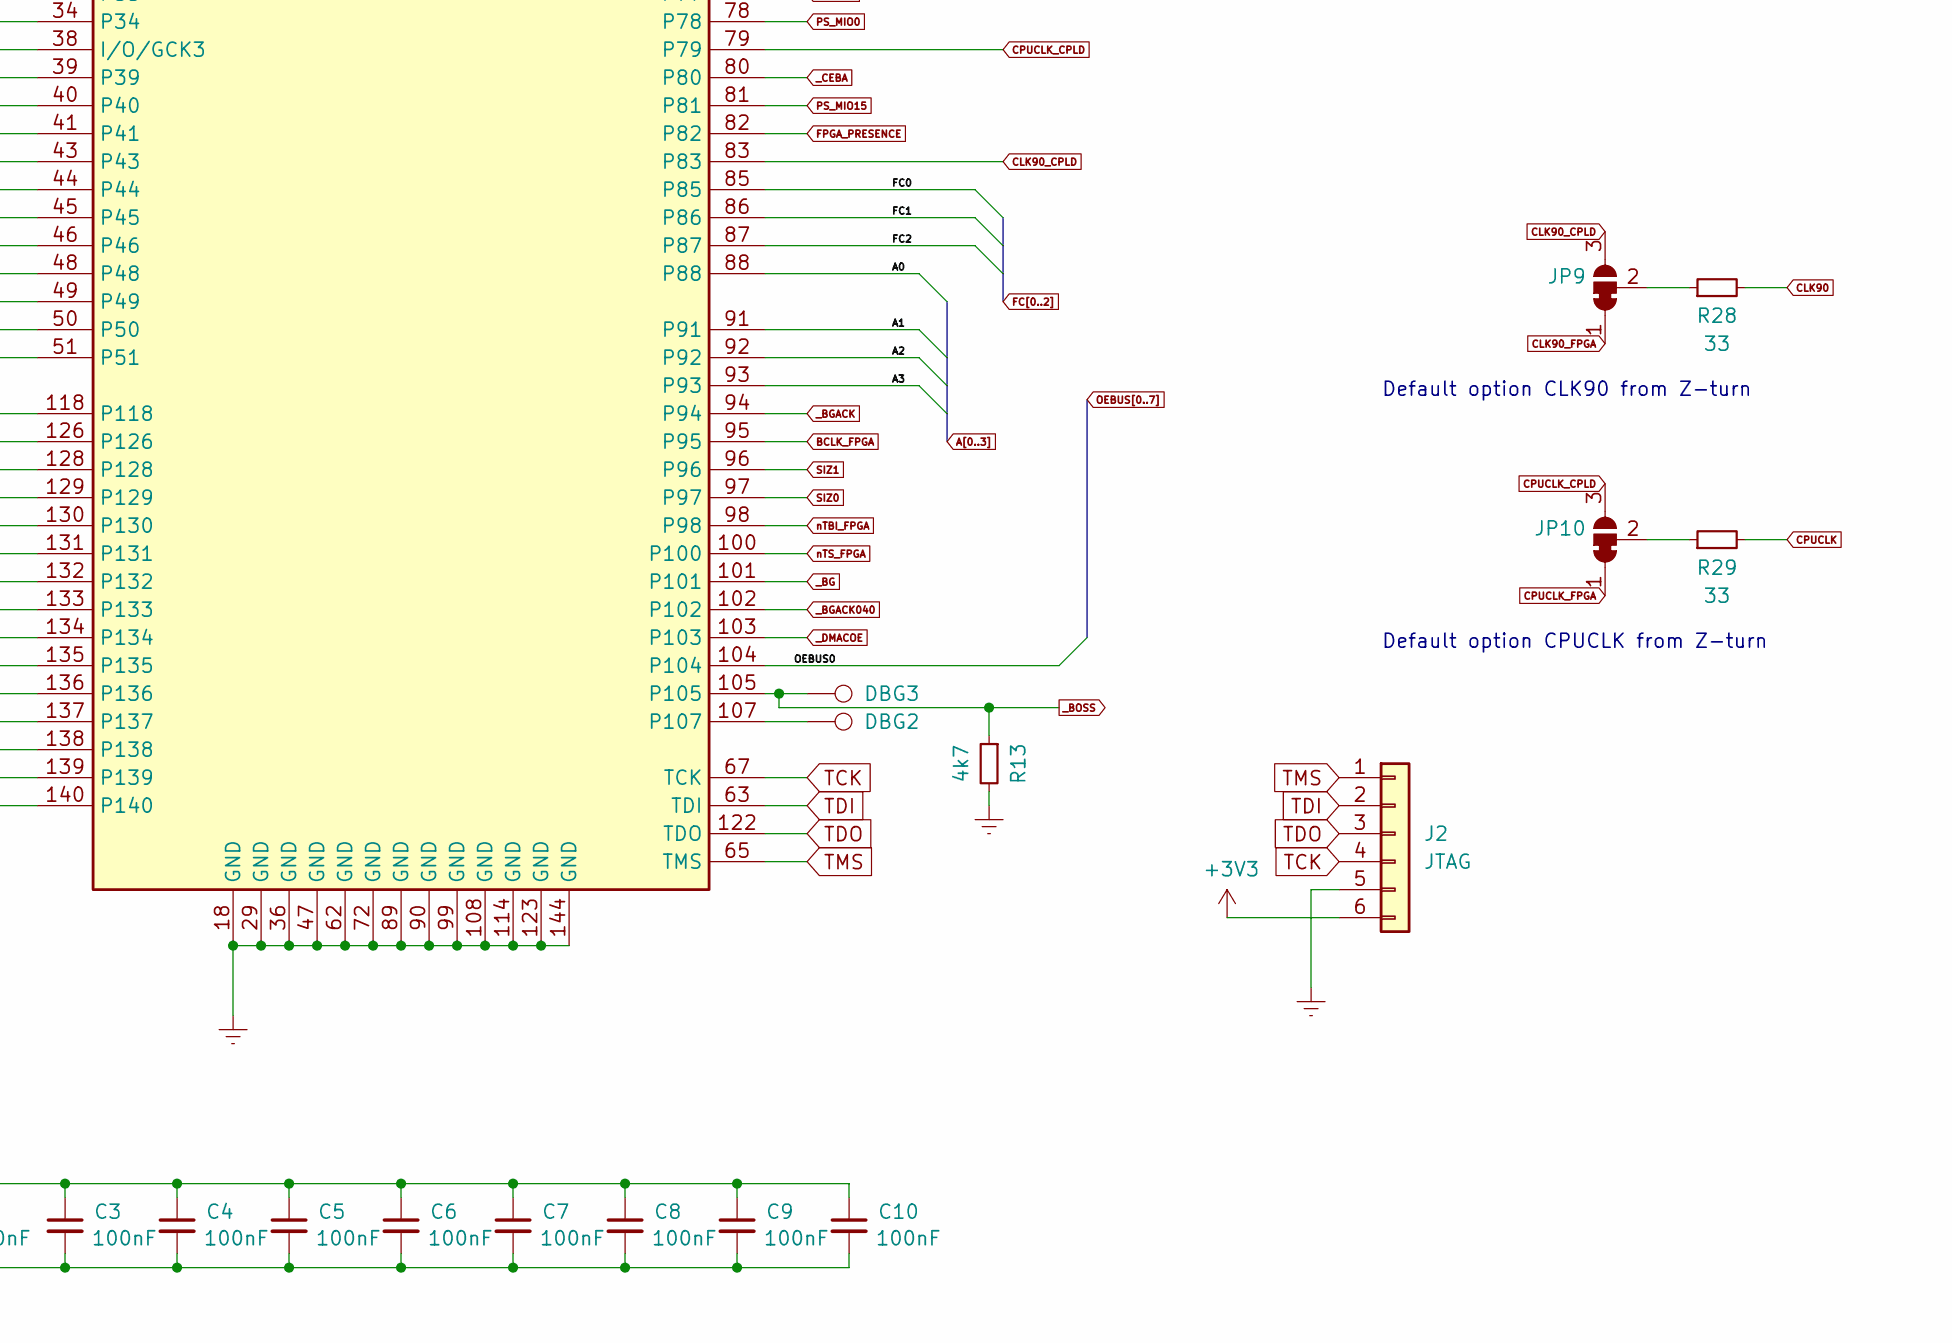
[picture p40: schematic Sheet3.kicad_sch, part in row 2, column 2]

Parts:
C1, C2, C3, C4, C5, C6, C7, C8, C9, C10: 100nF; C_0805_2012Metric_Pad1.18x1.45mm_HandSolder
DBG1, DBG2, DBG3: PCLK; TestPoint_THTPad_2.0x2.0mm_Drill1.0mm
J1: Jumper_2_Open; PinHeader_1x02_P2.54mm_Vertical
J2: JTAG; PinHeader_1x06_P2.54mm_Vertical
JP9, JP10: SolderJumper_3_Bridged12; SolderJumper-3_P1.3mm_Bridged12_RoundedPad1.0x1.5mm_NumberL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
R1, R3, R13: 4k7; R_0805_2012Metric_Pad1.20x1.40mm_HandSolder
R28, R29: 33; R_0805_2012Metric_Pad1.20x1.40mm_HandSolder
U1B1: BU4942; TSOP-5_1.65x3.05mm_P0.95mm
U2: XC95144XL-TQ144; TQFP-144_20x20mm_P0.5mm
U3: SN74CB3T3245PW; TSSOP-20_4.4x6.5mm_P0.65mm

Connections:
040A0: U2.121
040A1: U2.124
040A2: U2.125
040A3: U2.126
040A19: U2.140
040A20: U2.139
040A21: U2.138
040A22: U2.137
040A23: U2.136
040A24: U2.135
040A25: U2.134
040A26: U2.133
040A27: U2.132
040A28: U2.131
040A29: U2.130
040A30: U2.129
040A31: U2.128
+3V3: C1.1, C2.1, C3.1, C4.1, C5.1, C6.1, C7.1, C8.1, C9.1, C10.1, J2.6, R3.2, U2.1 (VCCIO), U2.8 (VCCINT), U2.37 (VCCIO), U2.42 (VCCINT), U2.55 (VCCIO), U2.73 (VCCIO), U2.84 (VCCINT), U2.109 (VCCIO), U2.127 (VCCIO), U2.141 (VCCINT), U3.20 (VCC)
+5V: U1B1.2 (VDD)
A0: U2.88
A1: U2.91
A2: U2.92
A3: U2.93
BCLK_FPGA: U2.95
CLK90: R28.2
CLK90_CPLD: JP9.3 (B), U2.83
CLK90_FPGA: JP9.1 (A)
CPUCLK: R29.2
CPUCLK_CPLD: JP10.3 (B), U2.79
CPUCLK_FPGA: JP10.1 (A)
CPUCLK_RECVD: U2.46
Earth: C1.2, C2.2, C3.2, C4.2, C5.2, C6.2, C7.2, C8.2, C9.2, C10.2, J1.2 (B), J2.5, R1.2, R13.2, U1B1.3 (GND), U2.18 (GND), U2.29 (GND), U2.36 (GND), U2.47 (GND), U2.62 (GND), U2.72 (GND), U2.89 (GND), U2.90 (GND), U2.99 (GND), U2.108 (GND), U2.114 (GND), U2.123 (GND), U2.144 (GND), U3.6 (A4), U3.7 (A5), U3.8 (A6), U3.9 (A7), U3.10 (GND)
FC0: U2.85
FC1: U2.86
FC2: U2.87
FPGA_PRESENCE: U2.82
INT6_ARM: R1.1, U2.21
LEBUS0: U2.52
LEBUS1: U2.53
LEBUS2: U2.54
LEBUS3: U2.56
LEBUS4: U2.57
LEBUS5: U2.58
LEBUS6: U2.59
LEBUS7: U2.60
LEBUS_DMA: U2.34
unnamed: DBG1.1, U2.106
unnamed: DBG2.1, U2.107
unnamed: J1.1 (A), R3.1, U2.44
unnamed: JP9.2 (C), R28.1
unnamed: JP10.2 (C), R29.1
OEBUS0: U2.104
OEBUS1: U2.110
OEBUS2: U2.111
OEBUS3: U2.112
OEBUS4: U2.113
OEBUS5: U2.61
OEBUS6: U2.116
OEBUS7: U2.120
PCLK: U2.30 (I/O/GCK1)
PS_MIO0: U2.78
PS_MIO8: U2.115
PS_MIO9: U2.20
PS_MIO12: U2.64
PS_MIO13: U2.48
PS_MIO15: U2.81
RESETOUT: U2.27
R_W: U3.18 (B0)
R_W040: U2.19, U3.2 (A0)
SIZ0: U2.97
SIZ1: U2.96
SIZ40_0: U2.14
SIZ40_1: U2.15
TCK: J2.4, U2.67 (TCK)
TDI: J2.2, U2.63 (TDI)
TDO: J2.3, U2.122 (TDO)
TM0: U2.40
TM1: U2.39
TM2: U2.38 (I/O/GCK3)
TMS: J2.1, U2.65 (TMS)
TT0: U2.41
TT1: U2.43
V_DETECTOR: U1B1.1 (~RESET), U2.143 (I/O/GSR)
_040CIOUT: U2.45, U3.4 (A2)
_040EMUL: U2.71
_040IPEND: U3.5 (A3)
_040RSTI: U2.32 (I/O/GCK2)
_040RSTO: U2.25
_060IPL0: U2.70
_060IPL1: U2.69
_060IPL2: U2.68
_AS: U2.117
_AVEC: U2.16
_AVEC040: U2.76
_BB040: U2.17
_BERR: U2.119
_BG: U2.101
_BG040: U2.77
_BGACK: U2.94
_BGACK040: U2.102, U3.19 (~OE)
_BGR040: U2.28
_BOSS: DBG3.1, R13.1, U2.105
_BR: U2.6 (I/O/GTS2)
_BR040: U2.11
_BTT: U2.26
_CEAB: U2.23
_CEBA: U2.80
_CIIN: U2.10
_CIOUT: U3.16 (B2)
_CLKEN: U2.66
_CPURST: U2.9
_DMACOE: U2.103
_DS: U2.118
_DSACK0: U2.7
_DSACK1: U2.5 (I/O/GTS1)
_EMUL: U2.2 (I/O/GTS3)
_HLT: U2.35
_INT2: U2.24
_INT6: U2.22
_IPEND: U3.15 (B3)
_IPL0: U2.49
_IPL1: U2.50
_IPL2: U2.51
_LOCK: U2.3 (I/O/GTS4), U3.3 (A1)
_LOCKE: U2.4
_RMC: U3.17 (B1)
_SNOOP: U2.33
_STERM: U2.142
_TA: U2.12
_TBI: U2.75
_TCI: U2.74
_TEA: U2.13
_TS: U2.31
nTBI_FPGA: U2.98
nTS_FPGA: U2.100

Notes on the sheet:
Default option CLK90 from Z-turn
LEBUS_DMA not connected on v02 (was TP6 on v02)
INT6_ARM not connected on v01 (was TP_8 on v01)
Default option CPUCLK from Z-turn
PS_MIO12 not connected on v01 (was TP_14 on v01)
PS_MIO8 not connected on v01 (was TP_17 on v01)
_CEAB not connected on v02 (was TP2 on v02)
_040RSTO not connected on v02 (was TP4 on v02)
_INT2 not connected on v02 (was TP3 on v02)
SOME_CONFIG
_SNOOP not connected on v02 (was TP5 on v02)
PS_MIO0 not connected on v01 (was right pad of R24 on v01)
CLOSE -> ENABLE SOME_CONFIG OPEN -> DISABLE SOME_CONFIG
CPUCLK_RECVD not connected on v02 (was TP7 on v02)
_INT6 not connected on v02 (was TP1 on v02)
_BGR040 and _BTT not connected on v01 (TP_16 and TP_13, respectively)
PS_MIO13 not connected on v01 (was TP_21 on v01)
