shanshe/Z3660/z3660-board/Z3660_kicad/Z3660_kicad9-023/Sheet5.kicad_sch

## KiCad design z3660-board/Z3660_kicad/Z3660_kicad9-023/Sheet5.kicad_sch (2026-05-13)

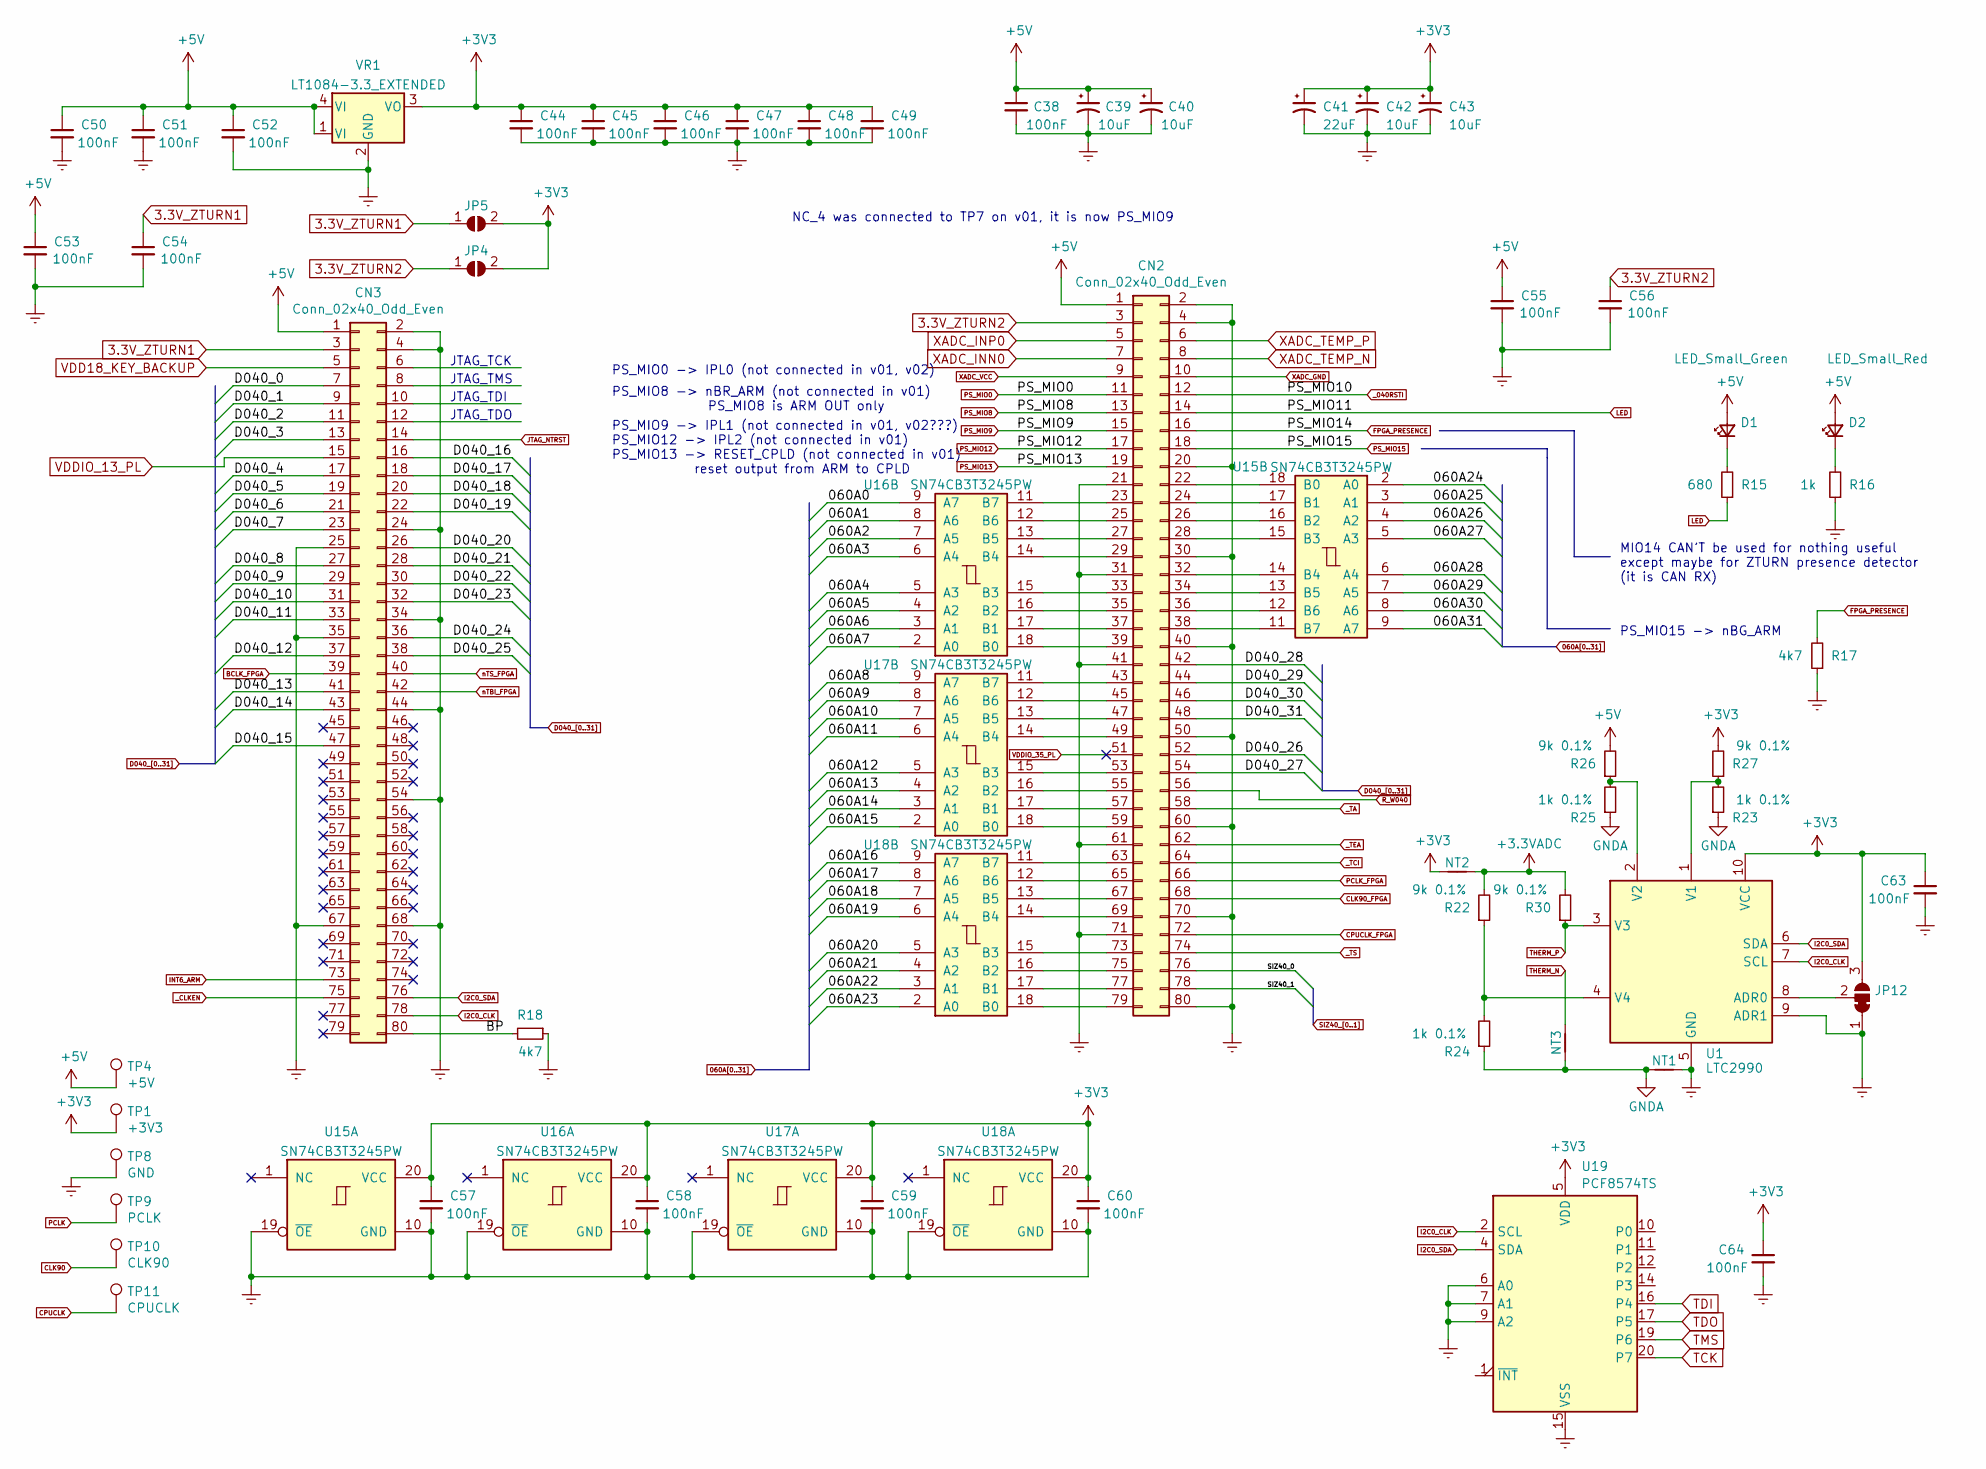
[picture p45: schematic Sheet5.kicad_sch]

Parts:
C38, C44, C45, C46, C47, C48, C49, C50, C51, C52, C53, C54, C55, C56, C57, C58, C59, C60, C63, C64: 100nF; C_0805_2012Metric_Pad1.18x1.45mm_HandSolder
C39, C40, C42, C43: 10uF; C_1206_3216Metric_Pad1.33x1.80mm_HandSolder
C41: 22uF; CP_Elec_6.3x5.4
CN2: Conn_02x40_Odd_Even; PinHeader_2x40_P1.27mm_Vertical
CN3: Conn_02x40_Odd_Even; PinHeader_2x40_P1.27mm_Vertical_CN3
D1: LED_Small_Green; LED_1206_3216Metric_Pad1.42x1.75mm_HandSolder
D2: LED_Small_Red; LED_1206_3216Metric_Pad1.42x1.75mm_HandSolder
JP4, JP5: BRIDGE_3V3; SolderJumper-2_P1.3mm_Open_RoundedPad1.0x1.5mm
JP12: SolderJumper_3_Bridged12; SolderJumper-3_P1.3mm_Bridged12_RoundedPad1.0x1.5mm_NumberL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
NT1, NT2, NT3: NetTie_2; NetTie-2_SMD_Pad0.5mm
R15: 680; R_0805_2012Metric_Pad1.20x1.40mm_HandSolder
R16: 1k; R_0805_2012Metric_Pad1.20x1.40mm_HandSolder
R17, R18: 4k7; R_0805_2012Metric_Pad1.20x1.40mm_HandSolder
R22, R26, R27, R30: 9k 0.1%; R_0805_2012Metric_Pad1.20x1.40mm_HandSolder
R23, R24, R25: 1k 0.1%; R_0805_2012Metric_Pad1.20x1.40mm_HandSolder
TP1: +3V3; TestPoint_THTPad_2.0x2.0mm_Drill1.0mm
TP4: +5V; TestPoint_THTPad_2.0x2.0mm_Drill1.0mm
TP8: GND; TestPoint_THTPad_2.0x2.0mm_Drill1.0mm
TP9: PCLK; TestPoint_THTPad_2.0x2.0mm_Drill1.0mm
TP10: CLK90; TestPoint_THTPad_2.0x2.0mm_Drill1.0mm
TP11: CPUCLK; TestPoint_THTPad_2.0x2.0mm_Drill1.0mm
U1: LTC2990; MSOP-10_3x3mm_P0.5mm
U15, U16, U17, U18: SN74CB3T3245PW; TSSOP-20_4.4x6.5mm_P0.65mm
U19: PCF8574TS; TSSOP-20_4.4x6.5mm_P0.65mm
VR1: LT1084-3.3_EXTENDED; Regulador_DCDC

Connections:
3.3V_ZTURN1: C54.1, CN3.3, JP5.1 (A)
3.3V_ZTURN2: C56.1, CN2.3, JP4.1 (A)
060A0: U16.9 (A7)
060A1: U16.8 (A6)
060A2: U16.7 (A5)
060A3: U16.6 (A4)
060A4: U16.5 (A3)
060A5: U16.4 (A2)
060A6: U16.3 (A1)
060A7: U16.2 (A0)
060A8: U17.9 (A7)
060A9: U17.8 (A6)
060A10: U17.7 (A5)
060A11: U17.6 (A4)
060A12: U17.5 (A3)
060A13: U17.4 (A2)
060A14: U17.3 (A1)
060A15: U17.2 (A0)
060A16: U18.9 (A7)
060A17: U18.8 (A6)
060A18: U18.7 (A5)
060A19: U18.6 (A4)
060A20: U18.5 (A3)
060A21: U18.4 (A2)
060A22: U18.3 (A1)
060A23: U18.2 (A0)
060A24: U15.2 (A0)
060A25: U15.3 (A1)
060A26: U15.4 (A2)
060A27: U15.5 (A3)
060A28: U15.6 (A4)
060A29: U15.7 (A5)
060A30: U15.8 (A6)
060A31: U15.9 (A7)
+3.3VADC: NT2.2, R22.2, R30.2
+3V3: C41.1, C42.1, C43.1, C44.1, C45.1, C46.1, C47.1, C48.1, C49.1, C57.1, C58.1, C59.1, C60.1, C63.1, C64.1, JP4.2 (B), JP5.2 (B), JP12.3 (B), NT2.1, R27.2, TP1.1, U1.10 (VCC), U15.20 (VCC), U16.20 (VCC), U17.20 (VCC), U18.20 (VCC), U19.5 (VDD), VR1.3 (VO)
+5V: C38.1, C39.1, C40.1, C50.1, C51.1, C52.1, C53.1, C55.1, CN2.1, CN3.1, D1.2 (A), D2.2 (A), R26.2, TP4.1, VR1.1 (VI), VR1.4 (VI)
BCLK_FPGA: CN3.39
BP: CN3.80, R18.2
CLK90: TP10.1
CLK90_FPGA: CN2.68
CPUCLK: TP11.1
CPUCLK_FPGA: CN2.72
D040_0: CN3.7
D040_1: CN3.9
D040_2: CN3.11
D040_3: CN3.13
D040_4: CN3.17
D040_5: CN3.19
D040_6: CN3.21
D040_7: CN3.23
D040_8: CN3.27
D040_9: CN3.29
D040_10: CN3.31
D040_11: CN3.33
D040_12: CN3.37
D040_13: CN3.41
D040_14: CN3.43
D040_15: CN3.47
D040_16: CN3.16
D040_17: CN3.18
D040_18: CN3.20
D040_19: CN3.22
D040_20: CN3.26
D040_21: CN3.28
D040_22: CN3.30
D040_23: CN3.32
D040_24: CN3.36
D040_25: CN3.38
D040_26: CN2.52
D040_27: CN2.54
D040_28: CN2.42
D040_29: CN2.44
D040_30: CN2.46
D040_31: CN2.48
Earth: C38.2, C39.2, C40.2, C41.2, C42.2, C43.2, C44.2, C45.2, C46.2, C47.2, C48.2, C49.2, C50.2, C51.2, C52.2, C53.2, C54.2, C55.2, C56.2, C57.2, C58.2, C59.2, C60.2, C63.2, C64.2, CN2.2, CN2.4, CN2.20, CN2.21, CN2.30, CN2.31, CN2.40, CN2.41, CN2.50, CN2.60, CN2.61, CN2.70, CN2.71, CN2.80, CN3.2, CN3.4, CN3.24, CN3.25, CN3.34, CN3.35, CN3.44, CN3.54, CN3.67, CN3.68, JP12.1 (A), NT1.2, R16.1, R17.1, R18.1, TP8.1, U1.5 (GND), U1.9 (ADR1), U15.10 (GND), U15.19 (~OE), U16.10 (GND), U16.19 (~OE), U17.10 (GND), U17.19 (~OE), U18.10 (GND), U18.19 (~OE), U19.6 (A0), U19.7 (A1), U19.9 (A2), U19.15 (VSS), VR1.2 (GND)
FPGA_PRESENCE: CN2.16, R17.2
GNDA: NT1.1, NT3.1, R23.1, R24.1, R25.1
I2C0_CLK: CN3.78, U1.7 (SCL), U19.2 (SCL)
I2C0_SDA: CN3.76, U1.6 (SDA), U19.4 (SDA)
INT6_ARM: CN3.73
JTAG_NTRST: CN3.14
LED: CN2.14, R15.1
unnamed: CN2.22, U15.18 (B0)
unnamed: CN2.23, U16.11 (B7)
unnamed: CN2.24, U15.17 (B1)
unnamed: CN2.25, U16.12 (B6)
unnamed: CN2.26, U15.16 (B2)
unnamed: CN2.27, U16.13 (B5)
unnamed: CN2.28, U15.15 (B3)
unnamed: CN2.29, U16.14 (B4)
unnamed: CN2.32, U15.14 (B4)
unnamed: CN2.33, U16.15 (B3)
unnamed: CN2.34, U15.13 (B5)
unnamed: CN2.35, U16.16 (B2)
unnamed: CN2.36, U15.12 (B6)
unnamed: CN2.37, U16.17 (B1)
unnamed: CN2.38, U15.11 (B7)
unnamed: CN2.39, U16.18 (B0)
unnamed: CN2.43, U17.11 (B7)
unnamed: CN2.45, U17.12 (B6)
unnamed: CN2.47, U17.13 (B5)
unnamed: CN2.49, U17.14 (B4)
unnamed: CN2.53, U17.15 (B3)
unnamed: CN2.55, U17.16 (B2)
unnamed: CN2.57, U17.17 (B1)
unnamed: CN2.59, U17.18 (B0)
unnamed: CN2.63, U18.11 (B7)
unnamed: CN2.65, U18.12 (B6)
unnamed: CN2.67, U18.13 (B5)
unnamed: CN2.69, U18.14 (B4)
unnamed: CN2.73, U18.15 (B3)
unnamed: CN2.75, U18.16 (B2)
unnamed: CN2.77, U18.17 (B1)
unnamed: CN2.79, U18.18 (B0)
unnamed: D1.1 (K), R15.2
unnamed: D2.1 (K), R16.2
unnamed: JP12.2 (C), U1.8 (ADR0)
unnamed: R22.1, R24.2, U1.4 (V4)
unnamed: R23.2, R27.1, U1.1 (V1)
unnamed: R25.2, R26.1, U1.2 (V2)
PCLK: TP9.1
PCLK_FPGA: CN2.66
PS_MIO0: CN2.11
PS_MIO8: CN2.13
PS_MIO9: CN2.15
PS_MIO12: CN2.17
PS_MIO13: CN2.19
PS_MIO15: CN2.18
R_W040: CN2.56
SIZ40_0: CN2.76
SIZ40_1: CN2.78
TCK: U19.20 (P7)
TDI: U19.16 (P4)
TDO: U19.17 (P5)
THERM_N: NT3.2
THERM_P: R30.1, U1.3 (V3)
TMS: U19.19 (P6)
VDD18_KEY_BACKUP: CN3.5
VDDIO_13_PL: CN3.15
VDDIO_35_PL: CN2.51
XADC_GND: CN2.10
XADC_INN0: CN2.7
XADC_INP0: CN2.5
XADC_TEMP_N: CN2.8
XADC_TEMP_P: CN2.6
XADC_VCC: CN2.9
_040RSTI: CN2.12
_CLKEN: CN3.75
_TA: CN2.58
_TCI: CN2.64
_TEA: CN2.62
_TS: CN2.74
nTBI_FPGA: CN3.42
nTS_FPGA: CN3.40

Notes on the sheet:
MIO14 CAN’T be used for nothing useful except maybe for ZTURN presence detector (it is CAN RX)
PS_MIO15 -> nBG_ARM
JTAG_TMS
JTAG_TCK
PS_MIO8 -> nBR_ARM (not connected in v01) PS_MIO8 is ARM OUT only
JTAG_TDO
PS_MIO9 -> IPL1 (not connected in v01, v02???) PS_MIO12 -> IPL2 (not connected in v01) PS_MIO13 -> RESET_CPLD (not connected in v01) reset output from ARM to CPLD
JTAG_TDI
PS_MIO0 -> IPL0 (not connected in v01, v02)
NC_4 was connected to TP7 on v01, it is now PS_MIO9
