shanshe/Z3660/z3660-board/Z3660_kicad/z3660_kicad-021-022/Sheet4.kicad_sch

## KiCad design z3660-board/Z3660_kicad/z3660_kicad-021-022/Sheet4.kicad_sch (2024-10-04)

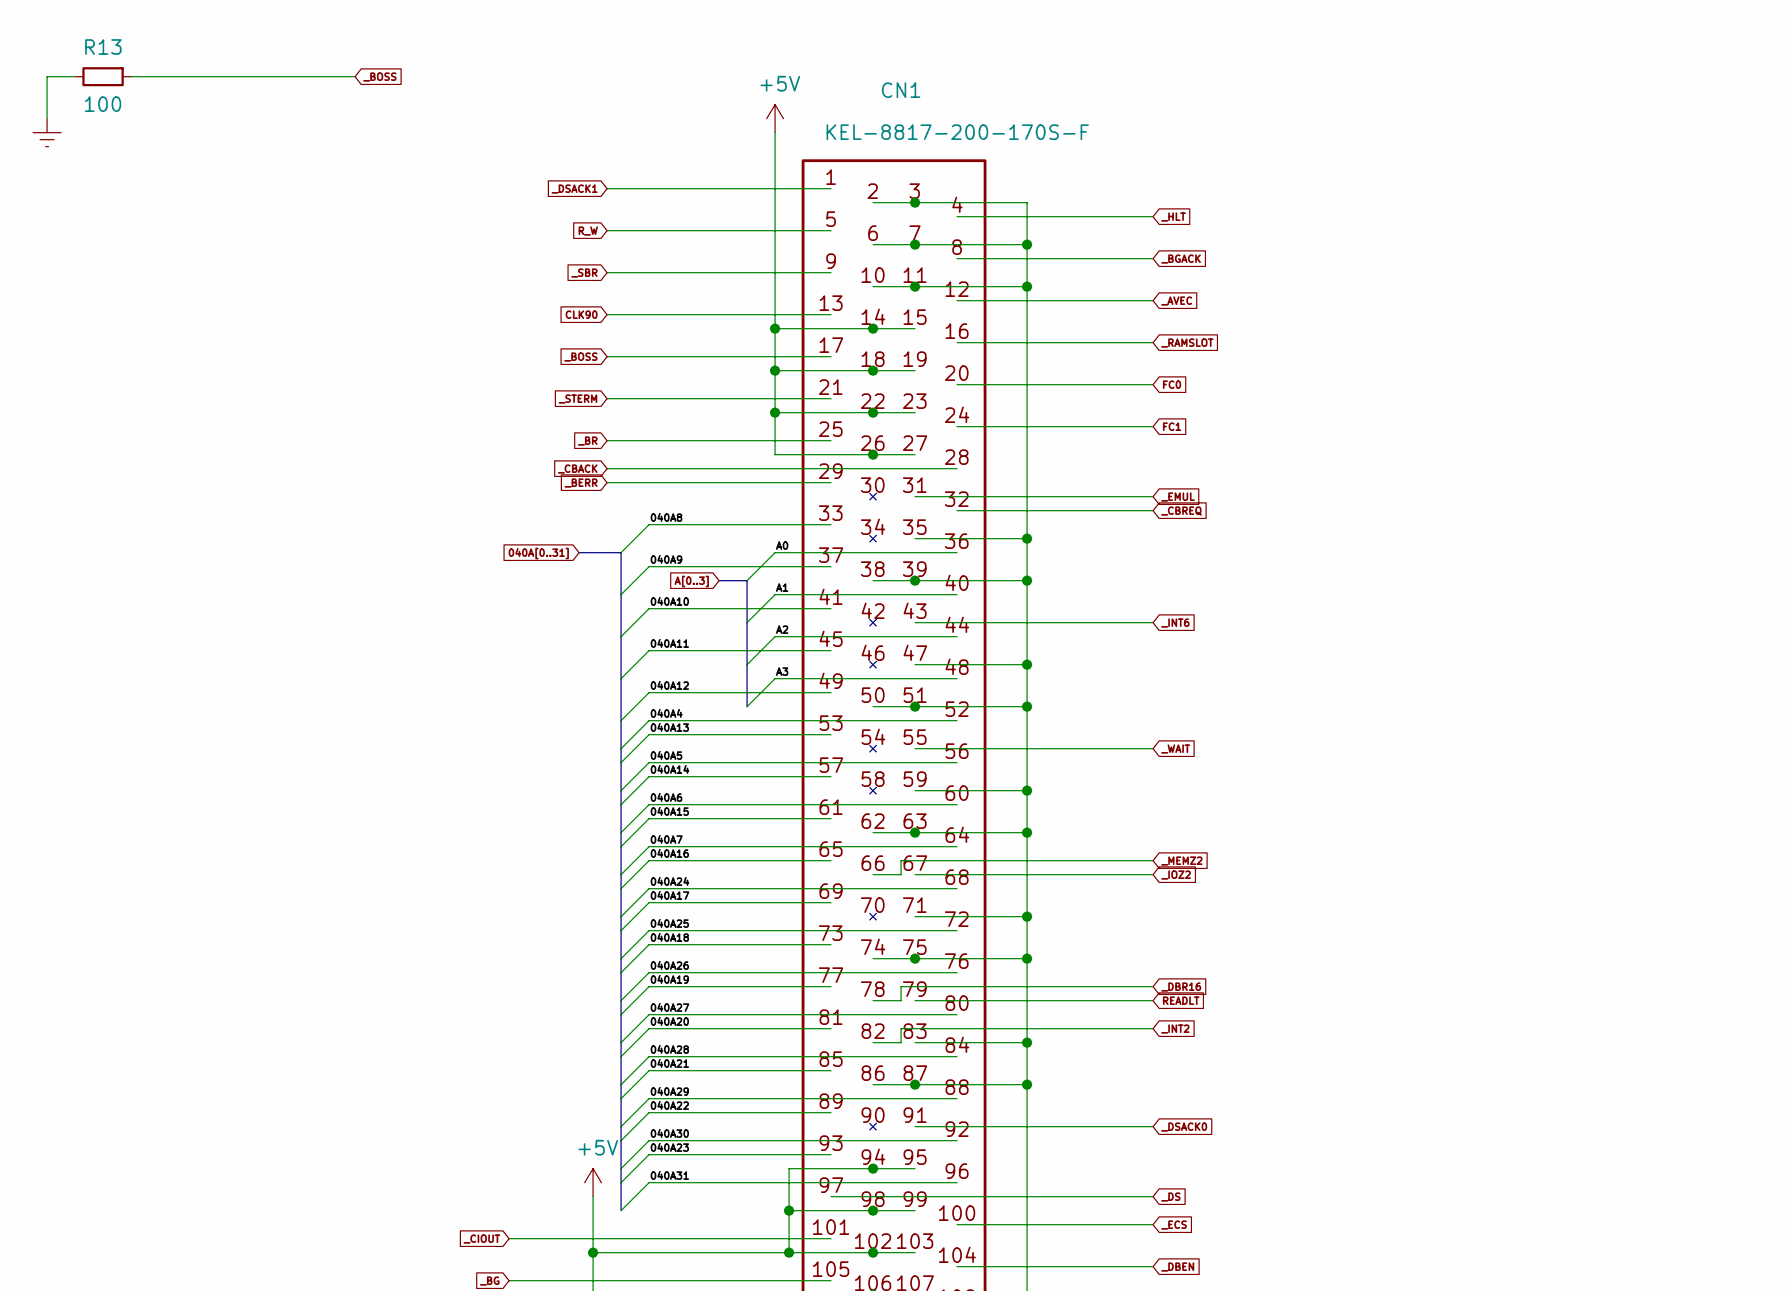
[picture p51: schematic Sheet4.kicad_sch, part in row 1, column 1]

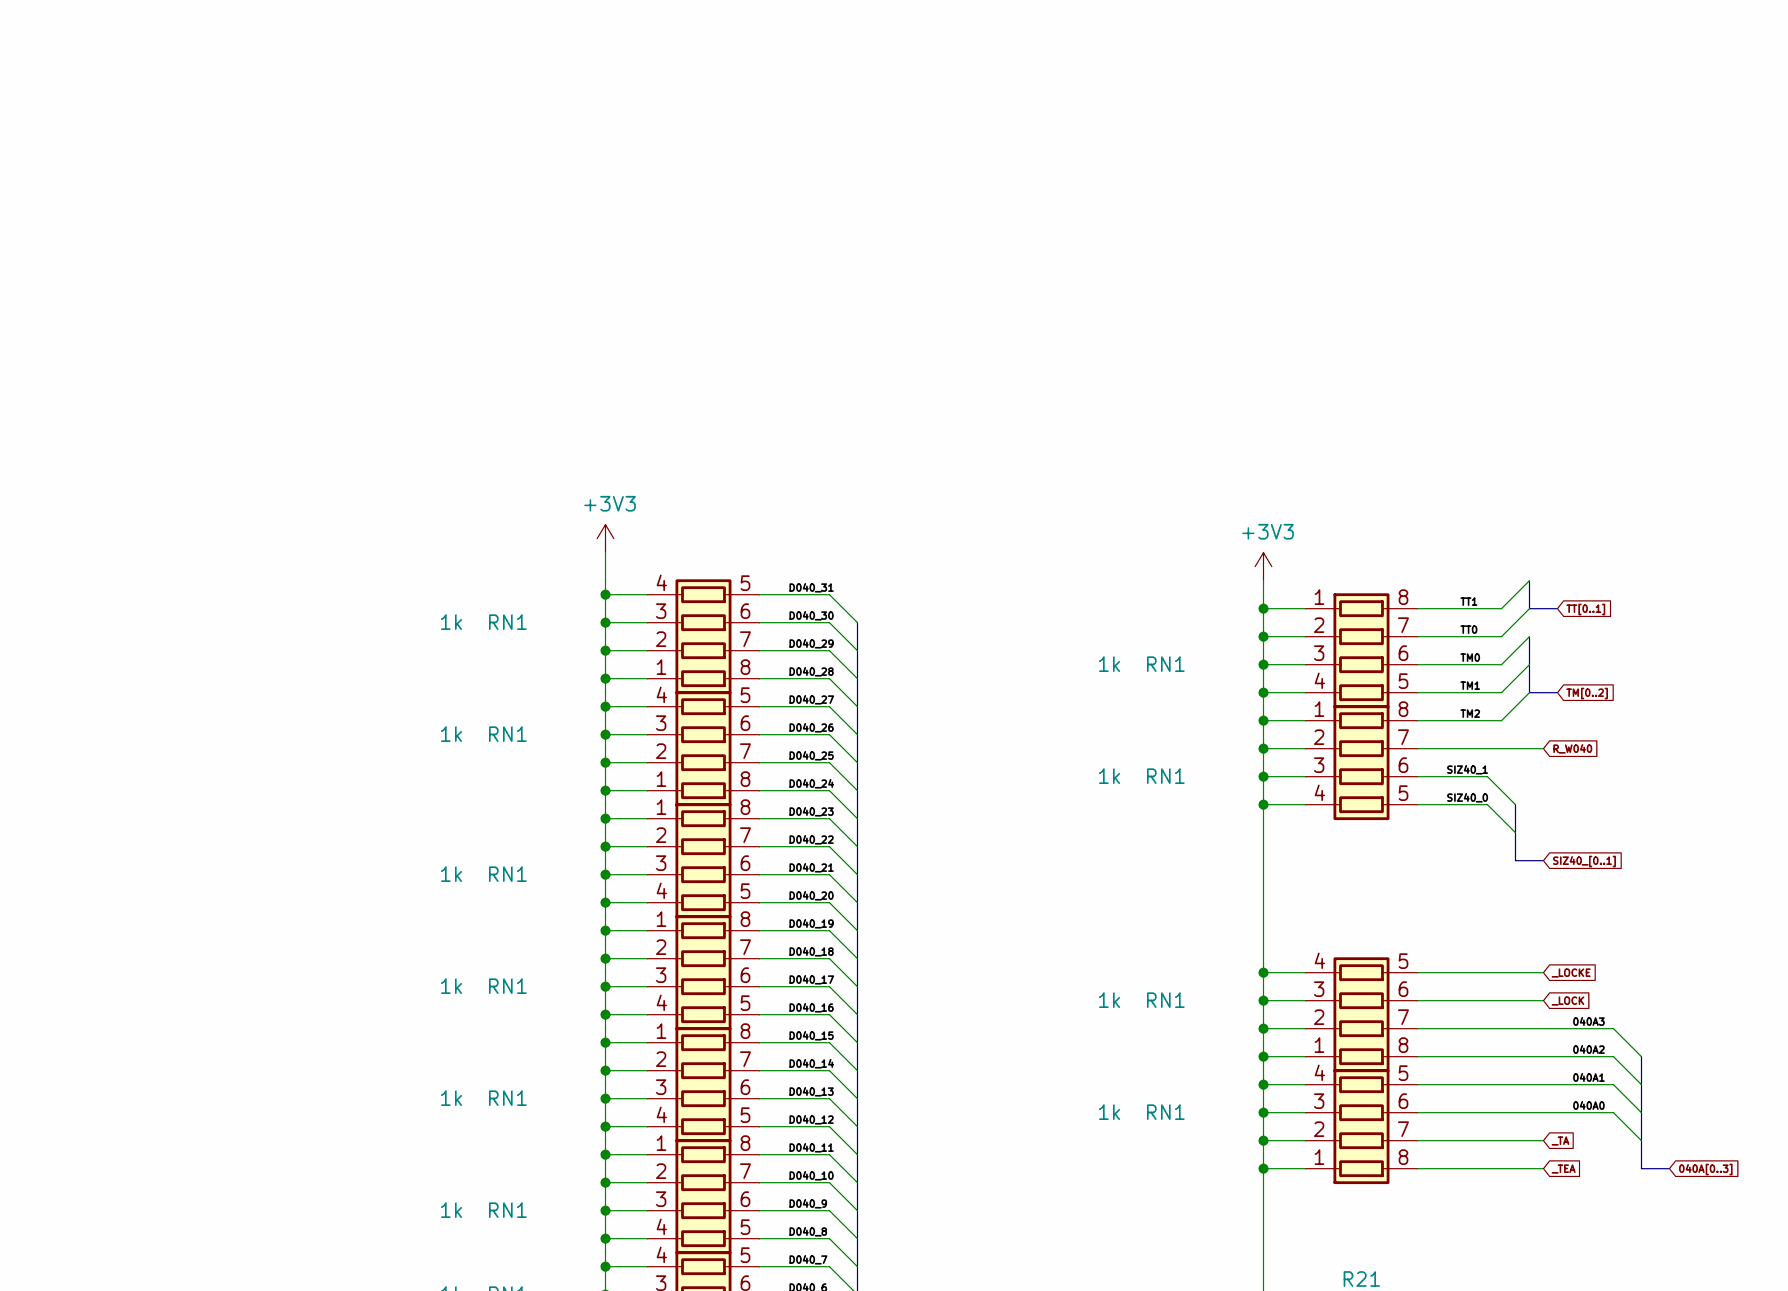
[picture p52: schematic Sheet4.kicad_sch, part in row 1, column 2]

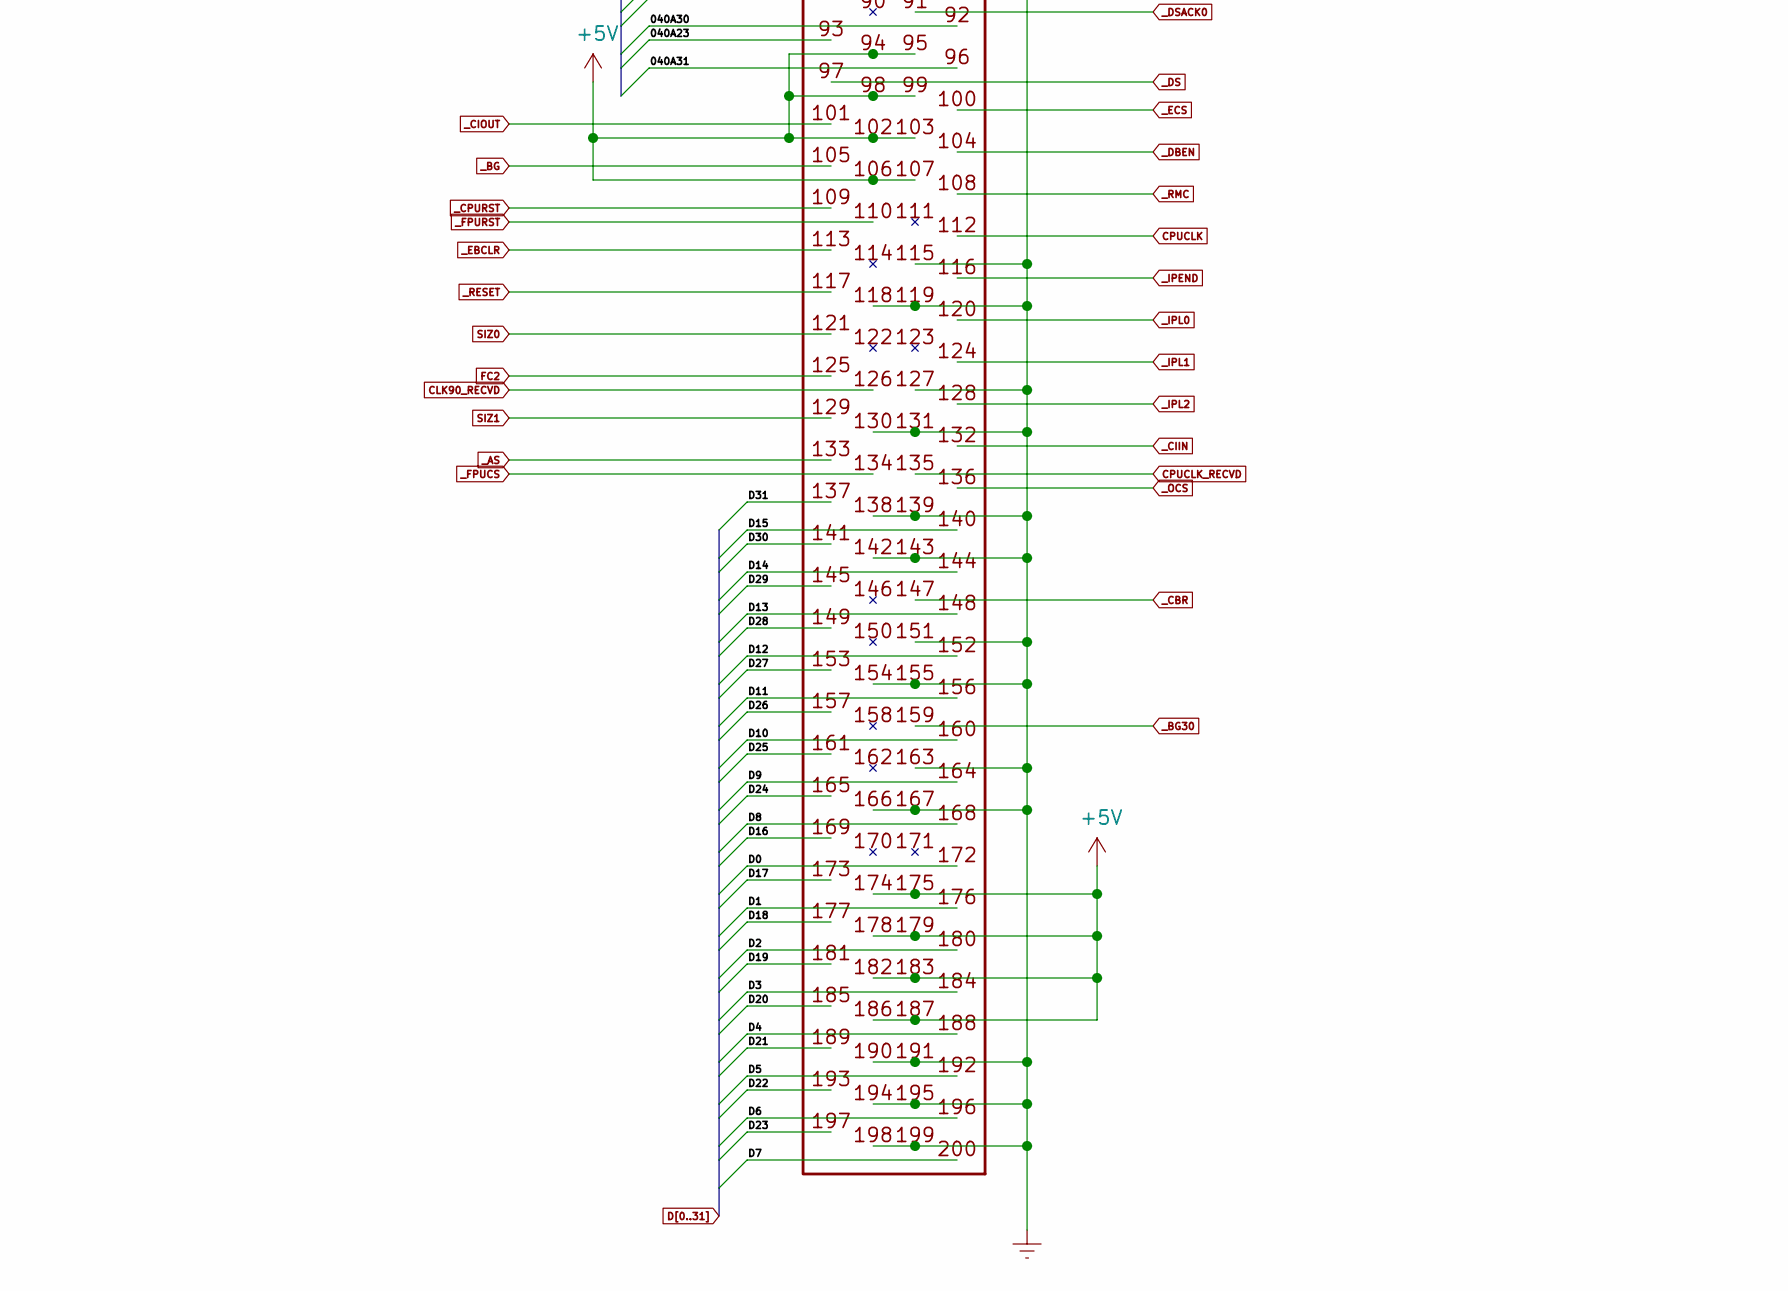
[picture p53: schematic Sheet4.kicad_sch, part in row 2, column 1]

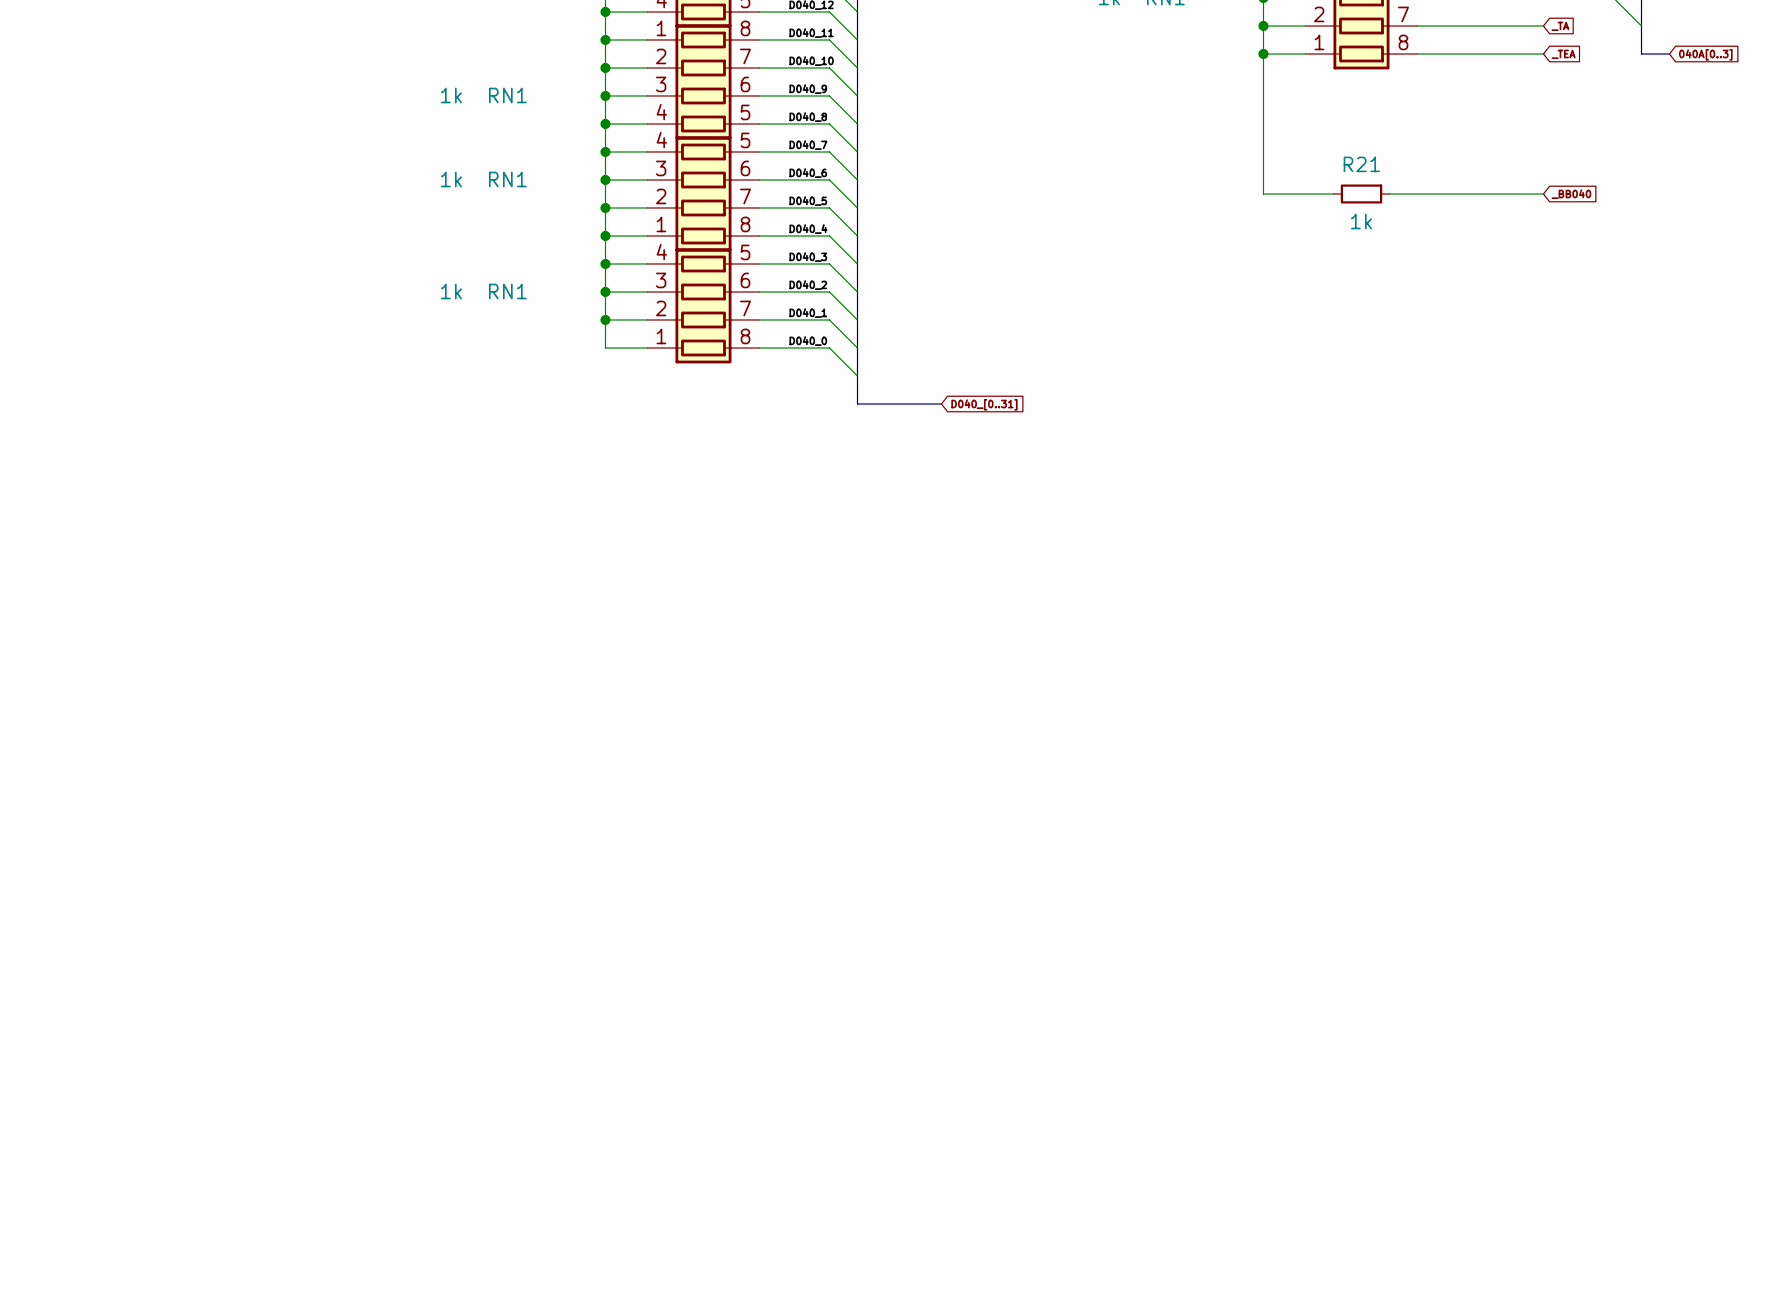
[picture p54: schematic Sheet4.kicad_sch, part in row 2, column 2]

Parts:
CN1: KEL-8817-200-170S-F; xIP-200
R13: 100; R_0805_2012Metric_Pad1.20x1.40mm_HandSolder
R21: 1k; R_0805_2012Metric_Pad1.20x1.40mm_HandSolder
RN1: 1k; R_Array_Convex_4x0603

Connections:
040A0: RN1.6 (R3.2)
040A1: RN1.5 (R4.2)
040A2: RN1.8 (R1.2)
040A3: RN1.7 (R2.2)
040A4: CN1.52 (A4)
040A5: CN1.56 (A5)
040A6: CN1.60 (A6)
040A7: CN1.64 (A7)
040A8: CN1.33 (A8)
040A9: CN1.37 (A9)
040A10: CN1.41 (A10)
040A11: CN1.45 (A11)
040A12: CN1.49 (A12)
040A13: CN1.53 (A13)
040A14: CN1.57 (A14)
040A15: CN1.61 (A15)
040A16: CN1.65 (A16)
040A17: CN1.69 (A17)
040A18: CN1.73 (A18)
040A19: CN1.77 (A19)
040A20: CN1.81 (A20)
040A21: CN1.85 (A21)
040A22: CN1.89 (A22)
040A23: CN1.93 (A23)
040A24: CN1.68 (MA24)
040A25: CN1.72 (MA25)
040A26: CN1.76 (MA26)
040A27: CN1.80 (A27)
040A28: CN1.84 (A28)
040A29: CN1.88 (A29)
040A30: CN1.92 (A30)
040A31: CN1.96 (A31)
+3V3: R21.2, RN1.1 (R1.1), RN1.2 (R2.1), RN1.3 (R3.1), RN1.4 (R4.1)
+5V: CN1.14 (+5V), CN1.15 (+5V), CN1.18 (+5V), CN1.19 (+5V), CN1.22 (+5V), CN1.23 (+5V), CN1.26 (+5V), CN1.27 (+5V), CN1.94 (+5V), CN1.95 (+5V), CN1.98 (+5V), CN1.99 (+5V), CN1.102 (+5V), CN1.103 (+5V), CN1.106 (+5V), CN1.107 (+5V), CN1.174 (+5V), CN1.175 (+5V), CN1.178 (+5V), CN1.179 (+5V), CN1.182 (+5V), CN1.183 (+5V), CN1.186 (+5V), CN1.187 (+5V)
A0: CN1.36 (A0)
A1: CN1.40 (A1)
A2: CN1.44 (A2)
A3: CN1.48 (A3)
CLK90: CN1.13 (CLK90)
CLK90_RECVD: CN1.126 (CLK90_RECVD)
CPUCLK: CN1.112 (CPUCLK)
CPUCLK_RECVD: CN1.135 (CPUCLKB_RECVD)
D0: CN1.172 (D0)
D1: CN1.176 (D1)
D2: CN1.180 (D2)
D3: CN1.184 (D3)
D4: CN1.188 (D4)
D5: CN1.192 (D5)
D6: CN1.196 (D6)
D7: CN1.200 (D7)
D8: CN1.168 (D8)
D9: CN1.164 (D9)
D10: CN1.160 (D10)
D11: CN1.156 (D11)
D12: CN1.152 (D12)
D13: CN1.148 (D13)
D14: CN1.144 (D14)
D15: CN1.140 (D15)
D16: CN1.169 (D16)
D17: CN1.173 (D17)
D18: CN1.177 (D18)
D19: CN1.181 (D19)
D20: CN1.185 (D20)
D21: CN1.189 (D21)
D22: CN1.193 (D22)
D23: CN1.197 (D23)
D24: CN1.165 (D24)
D25: CN1.161 (D25)
D26: CN1.157 (D26)
D27: CN1.153 (D27)
D28: CN1.149 (D28)
D29: CN1.145 (D29)
D30: CN1.141 (D30)
D31: CN1.137 (D31)
D040_0: RN1.8 (R1.2)
D040_1: RN1.7 (R2.2)
D040_2: RN1.6 (R3.2)
D040_3: RN1.5 (R4.2)
D040_4: RN1.8 (R1.2)
D040_5: RN1.7 (R2.2)
D040_6: RN1.6 (R3.2)
D040_7: RN1.5 (R4.2)
D040_8: RN1.5 (R4.2)
D040_9: RN1.6 (R3.2)
D040_10: RN1.7 (R2.2)
D040_11: RN1.8 (R1.2)
D040_12: RN1.5 (R4.2)
D040_13: RN1.6 (R3.2)
D040_14: RN1.7 (R2.2)
D040_15: RN1.8 (R1.2)
D040_16: RN1.5 (R4.2)
D040_17: RN1.6 (R3.2)
D040_18: RN1.7 (R2.2)
D040_19: RN1.8 (R1.2)
D040_20: RN1.5 (R4.2)
D040_21: RN1.6 (R3.2)
D040_22: RN1.7 (R2.2)
D040_23: RN1.8 (R1.2)
D040_24: RN1.8 (R1.2)
D040_25: RN1.7 (R2.2)
D040_26: RN1.6 (R3.2)
D040_27: RN1.5 (R4.2)
D040_28: RN1.8 (R1.2)
D040_29: RN1.7 (R2.2)
D040_30: RN1.6 (R3.2)
D040_31: RN1.5 (R4.2)
Earth: CN1.2 (GND), CN1.3 (GND), CN1.6 (GND), CN1.7 (GND), CN1.10 (GND), CN1.11 (GND), CN1.35 (GND), CN1.38 (GND), CN1.39 (GND), CN1.47 (GND), CN1.50 (GND), CN1.51 (GND), CN1.59 (GND), CN1.62 (GND), CN1.63 (GND), CN1.71 (GND), CN1.74 (GND), CN1.75 (GND), CN1.83 (GND), CN1.86 (GND), CN1.87 (GND), CN1.115 (GND), CN1.118 (GND), CN1.119 (GND), CN1.127 (GND), CN1.130 (GND), CN1.131 (GND), CN1.138 (GND), CN1.139 (GND), CN1.142 (GND), CN1.143 (GND), CN1.151 (GND), CN1.154 (GND), CN1.155 (GND), CN1.163 (GND), CN1.166 (GND), CN1.167 (GND), CN1.190 (GND), CN1.191 (GND), CN1.194 (GND), CN1.195 (GND), CN1.198 (GND), CN1.199 (GND), R13.2
FC0: CN1.20 (FC0)
FC1: CN1.24 (FC1)
FC2: CN1.125 (FC2)
READLT: CN1.79 (READLT)
R_W: CN1.5 (R_W)
R_W040: RN1.7 (R2.2)
SIZ0: CN1.121 (SIZ0)
SIZ1: CN1.129 (SIZ1)
SIZ40_0: RN1.5 (R4.2)
SIZ40_1: RN1.6 (R3.2)
TM0: RN1.6 (R3.2)
TM1: RN1.5 (R4.2)
TM2: RN1.8 (R1.2)
TT0: RN1.7 (R2.2)
TT1: RN1.8 (R1.2)
_AS: CN1.133 (_AS)
_AVEC: CN1.12 (_AVEC)
_BB040: R21.1
_BERR: CN1.29 (_BERR)
_BG: CN1.105 (_BG)
_BG30: CN1.159 (_BG30)
_BGACK: CN1.8 (_BGACK)
_BOSS: CN1.17 (_BOSS), R13.1
_BR: CN1.25 (_BR)
_CBACK: CN1.28 (_CBACK)
_CBR: CN1.147 (_CBR)
_CBREQ: CN1.32 (_CBREQ)
_CIIN: CN1.132 (_CIIN)
_CIOUT: CN1.101 (_CIOUT)
_CPURST: CN1.109 (_CPURST)
_DBEN: CN1.104 (_DBEN)
_DBR16: CN1.78 (_DBR16)
_DS: CN1.97 (_DS)
_DSACK0: CN1.91 (_DSACK0)
_DSACK1: CN1.1 (_DSACK1)
_EBCLR: CN1.113 (_EBCLR)
_ECS: CN1.100 (_ECS)
_EMUL: CN1.31 (_EMUL)
_FPUCS: CN1.134 (_FPUCS)
_FPURST: CN1.110 (_FPURST)
_HLT: CN1.4 (_HLT)
_INT2: CN1.82 (NC)
_INT6: CN1.43 (NC)
_IOZ2: CN1.67 (_IOZ2)
_IPEND: CN1.116 (_IPEND)
_IPL0: CN1.120 (_IPL0)
_IPL1: CN1.124 (_IPL1)
_IPL2: CN1.128 (_IPL0)
_LOCK: RN1.6 (R3.2)
_LOCKE: RN1.5 (R4.2)
_MEMZ2: CN1.66 (_MEMZ2)
_OCS: CN1.136 (_OCS)
_RAMSLOT: CN1.16 (_RAMSLOT)
_RESET: CN1.117 (_RESET)
_RMC: CN1.108 (_RMC)
_SBR: CN1.9 (_SBR)
_STERM: CN1.21 (_STERM)
_TA: RN1.7 (R2.2)
_TEA: RN1.8 (R1.2)
_WAIT: CN1.55 (_WAIT)
