shanshe/Z3660/z3660-board/Z3660_kicad/z3660_kicad-021-022/Sheet6.kicad_sch

## KiCad design z3660-board/Z3660_kicad/z3660_kicad-021-022/Sheet6.kicad_sch (2024-10-04)

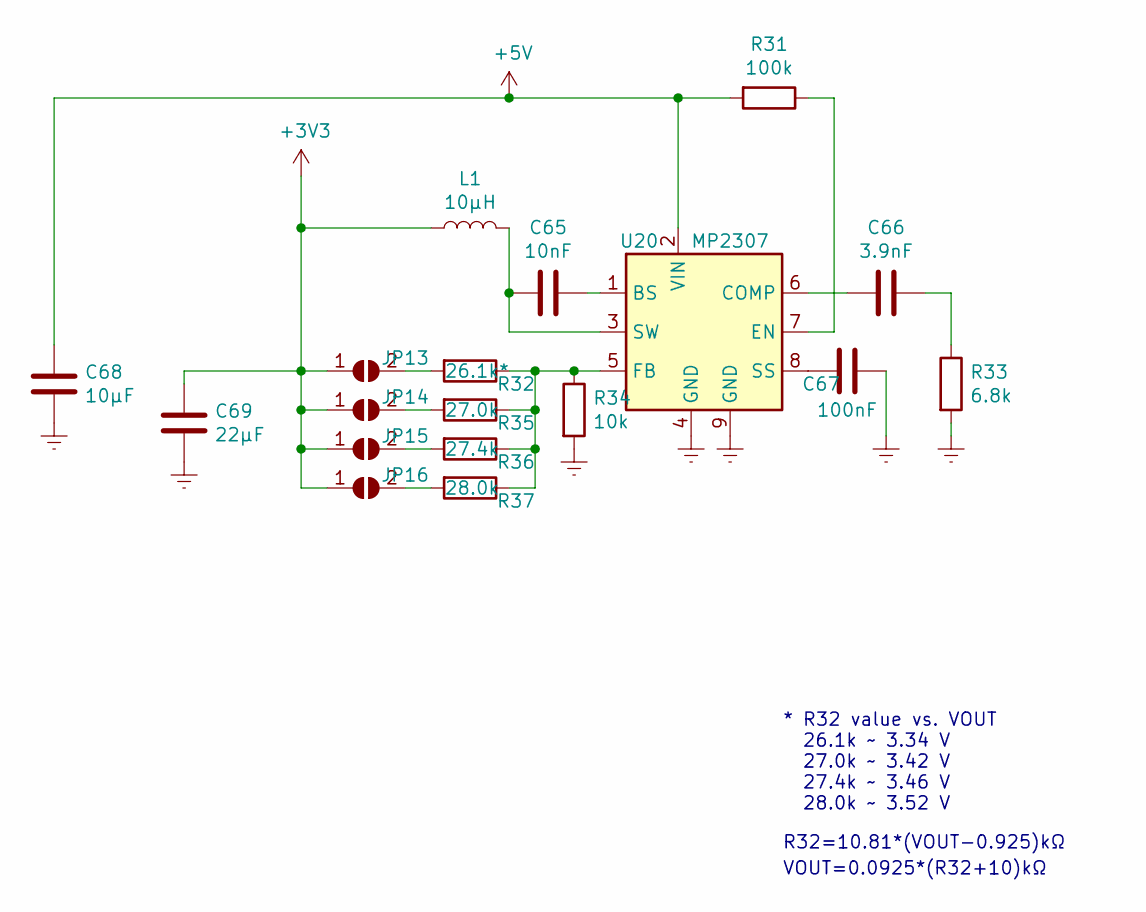
[picture p55: schematic Sheet6.kicad_sch]

Parts:
C65: 10nF; C_0603_1608Metric
C66: 3.9nF; C_0603_1608Metric
C67: 100nF; C_0603_1608Metric
C68: 10µF; C_0805_2012Metric
C69: 22µF; C_0805_2012Metric
JP13, JP14, JP15, JP16: SolderJumper_2_Open; small_SolderJumper-2_P1.3mm_Open_RoundedPad1.0x1.5mm
L1: 10µH; L_Bourns_SRP7028A_7.3x6.6mm
R31: 100k; R_0603_1608Metric
R32: 26.1k*; R_0603_1608Metric
R33: 6.8k; R_0603_1608Metric
R34: 10k; R_0603_1608Metric
R35: 27.0k; R_0603_1608Metric
R36: 27.4k; R_0603_1608Metric
R37: 28.0k; R_0603_1608Metric
U20: MP2307; SOIC-8-1EP_3.9x4.9mm_P1.27mm_EP2.514x3.2mm

Connections:
+3V3: C69.1, JP13.1 (A), JP14.1 (A), JP15.1 (A), JP16.1 (A), L1.1
+5V: C68.1, R31.2, U20.2 (VIN)
Earth: C67.1, C68.2, C69.2, R33.2, R34.2, U20.4 (GND), U20.9 (GND)
unnamed: C65.1, U20.1 (BS)
unnamed: C65.2, L1.2, U20.3 (SW)
unnamed: C66.1, R33.1
unnamed: C66.2, U20.6 (COMP)
unnamed: C67.2, U20.8 (SS)
unnamed: JP13.2 (B), R32.2
unnamed: JP14.2 (B), R35.2
unnamed: JP15.2 (B), R36.2
unnamed: JP16.2 (B), R37.2
unnamed: R31.1, U20.7 (EN)
unnamed: R32.1, R34.1, R35.1, R36.1, R37.1, U20.5 (FB)

Notes on the sheet:
* R32 value vs. VOUT 26.1k ~ 3.34 V 27.0k ~ 3.42 V 27.4k ~ 3.46 V 28.0k ~ 3.52 V
R32=10.81*(VOUT−0.925)kΩ
VOUT=0.0925*(R32+10)kΩ
