shanshe/Z3660/z3660-firmware/Z-TURN/vitis_ide/Z3660/src/lwip/opt.h

#if !defined LWIP_HDR_OPT_H
#define LWIP_HDR_OPT_H
#define LWIP_NO_CTYPE_H 1
#include "lwipopts.h"
#include "lwip/debug.h"
#ifdef __MICROBLAZE__
#include "mb_interface.h"
#endif
#if !defined NO_SYS || defined __DOXYGEN__
#ifdef USE_RTOS
#define NO_SYS                          0
#else
#define NO_SYS                          1
#endif
#endif
#if !defined LWIP_TIMERS || defined __DOXYGEN__
#ifdef NO_SYS_NO_TIMERS
#define LWIP_TIMERS                     (!NO_SYS || (NO_SYS && !NO_SYS_NO_TIMERS))
#else
#define LWIP_TIMERS                     1
#endif
#endif
#if !defined LWIP_TIMERS_CUSTOM || defined __DOXYGEN__
#define LWIP_TIMERS_CUSTOM              0
#endif
#if !defined MEMCPY || defined __DOXYGEN__
#define MEMCPY(dst,src,len)             memcpy(dst,src,len)
#endif
#if !defined SMEMCPY || defined __DOXYGEN__
#define SMEMCPY(dst,src,len)            memcpy(dst,src,len)
#endif
#if !defined MEMMOVE || defined __DOXYGEN__
#define MEMMOVE(dst,src,len)            memmove(dst,src,len)
#endif
#if !defined LWIP_MPU_COMPATIBLE || defined __DOXYGEN__
#define LWIP_MPU_COMPATIBLE             0
#endif
#if !defined LWIP_TCPIP_CORE_LOCKING || defined __DOXYGEN__
#define LWIP_TCPIP_CORE_LOCKING         1
#endif
#if !defined LWIP_TCPIP_CORE_LOCKING_INPUT || defined __DOXYGEN__
#define LWIP_TCPIP_CORE_LOCKING_INPUT   0
#endif
#if !defined SYS_LIGHTWEIGHT_PROT || defined __DOXYGEN__
#define SYS_LIGHTWEIGHT_PROT            1
#endif
#if !defined LWIP_ASSERT_CORE_LOCKED || defined __DOXYGEN__
#define LWIP_ASSERT_CORE_LOCKED()
#endif
#if !defined LWIP_MARK_TCPIP_THREAD || defined __DOXYGEN__
#define LWIP_MARK_TCPIP_THREAD()
#endif
#if !defined MEM_LIBC_MALLOC || defined __DOXYGEN__
#define MEM_LIBC_MALLOC                 0
#endif
#if !defined MEMP_MEM_MALLOC || defined __DOXYGEN__
#define MEMP_MEM_MALLOC                 0
#endif
#if !defined MEMP_MEM_INIT || defined __DOXYGEN__
#define MEMP_MEM_INIT                   0
#endif
#if !defined MEM_ALIGNMENT || defined __DOXYGEN__
#define MEM_ALIGNMENT                   1
#endif
#if !defined MEM_SIZE || defined __DOXYGEN__
#define MEM_SIZE                        1600
#endif
#if !defined MEMP_OVERFLOW_CHECK || defined __DOXYGEN__
#define MEMP_OVERFLOW_CHECK             0
#endif
#if !defined MEMP_SANITY_CHECK || defined __DOXYGEN__
#define MEMP_SANITY_CHECK               0
#endif
#if !defined MEM_OVERFLOW_CHECK || defined __DOXYGEN__
#define MEM_OVERFLOW_CHECK              0
#endif
#if !defined MEM_SANITY_CHECK || defined __DOXYGEN__
#define MEM_SANITY_CHECK                0
#endif
#if !defined MEM_USE_POOLS || defined __DOXYGEN__
#define MEM_USE_POOLS                   0
#endif
#if !defined MEM_USE_POOLS_TRY_BIGGER_POOL || defined __DOXYGEN__
#define MEM_USE_POOLS_TRY_BIGGER_POOL   0
#endif
#if !defined MEMP_USE_CUSTOM_POOLS || defined __DOXYGEN__
#define MEMP_USE_CUSTOM_POOLS           0
#endif
#if !defined LWIP_ALLOW_MEM_FREE_FROM_OTHER_CONTEXT || defined __DOXYGEN__
#define LWIP_ALLOW_MEM_FREE_FROM_OTHER_CONTEXT 0
#endif
#if !defined MEMP_NUM_PBUF || defined __DOXYGEN__
#define MEMP_NUM_PBUF                   16
#endif
#if !defined MEMP_NUM_RAW_PCB || defined __DOXYGEN__
#define MEMP_NUM_RAW_PCB                4
#endif
#if !defined MEMP_NUM_UDP_PCB || defined __DOXYGEN__
#define MEMP_NUM_UDP_PCB                4
#endif
#if !defined MEMP_NUM_TCP_PCB || defined __DOXYGEN__
#define MEMP_NUM_TCP_PCB                5
#endif
#if !defined MEMP_NUM_TCP_PCB_LISTEN || defined __DOXYGEN__
#define MEMP_NUM_TCP_PCB_LISTEN         8
#endif
#if !defined MEMP_NUM_TCP_SEG || defined __DOXYGEN__
#define MEMP_NUM_TCP_SEG                16
#endif
#if !defined MEMP_NUM_ALTCP_PCB || defined __DOXYGEN__
#define MEMP_NUM_ALTCP_PCB              MEMP_NUM_TCP_PCB
#endif
#if !defined MEMP_NUM_REASSDATA || defined __DOXYGEN__
#define MEMP_NUM_REASSDATA              5
#endif
#if !defined MEMP_NUM_FRAG_PBUF || defined __DOXYGEN__
#define MEMP_NUM_FRAG_PBUF              15
#endif
#if !defined MEMP_NUM_ARP_QUEUE || defined __DOXYGEN__
#define MEMP_NUM_ARP_QUEUE              30
#endif
#if !defined MEMP_NUM_IGMP_GROUP || defined __DOXYGEN__
#define MEMP_NUM_IGMP_GROUP             8
#endif
#define LWIP_NUM_SYS_TIMEOUT_INTERNAL   (LWIP_TCP + IP_REASSEMBLY + LWIP_ARP + (2*LWIP_DHCP) + LWIP_AUTOIP + LWIP_IGMP + LWIP_DNS + PPP_NUM_TIMEOUTS + (LWIP_IPV6 * (1 + LWIP_IPV6_REASS + LWIP_IPV6_MLD)))
#if !defined MEMP_NUM_SYS_TIMEOUT || defined __DOXYGEN__
#define MEMP_NUM_SYS_TIMEOUT            LWIP_NUM_SYS_TIMEOUT_INTERNAL
#endif
#if !defined MEMP_NUM_NETBUF || defined __DOXYGEN__
#define MEMP_NUM_NETBUF                 2
#endif
#if !defined MEMP_NUM_NETCONN || defined __DOXYGEN__
#define MEMP_NUM_NETCONN                4
#endif
#if !defined MEMP_NUM_SELECT_CB || defined __DOXYGEN__
#define MEMP_NUM_SELECT_CB              4
#endif
#if !defined MEMP_NUM_TCPIP_MSG_API || defined __DOXYGEN__
#define MEMP_NUM_TCPIP_MSG_API          8
#endif
#if !defined MEMP_NUM_TCPIP_MSG_INPKT || defined __DOXYGEN__
#define MEMP_NUM_TCPIP_MSG_INPKT        8
#endif
#if !defined MEMP_NUM_NETDB || defined __DOXYGEN__
#define MEMP_NUM_NETDB                  1
#endif
#if !defined MEMP_NUM_LOCALHOSTLIST || defined __DOXYGEN__
#define MEMP_NUM_LOCALHOSTLIST          1
#endif
#if !defined PBUF_POOL_SIZE || defined __DOXYGEN__
#define PBUF_POOL_SIZE                  16
#endif
#if !defined MEMP_NUM_API_MSG || defined __DOXYGEN__
#define MEMP_NUM_API_MSG                MEMP_NUM_TCPIP_MSG_API
#endif
#if !defined MEMP_NUM_DNS_API_MSG || defined __DOXYGEN__
#define MEMP_NUM_DNS_API_MSG            MEMP_NUM_TCPIP_MSG_API
#endif
#if !defined MEMP_NUM_SOCKET_SETGETSOCKOPT_DATA || defined __DOXYGEN__
#define MEMP_NUM_SOCKET_SETGETSOCKOPT_DATA MEMP_NUM_TCPIP_MSG_API
#endif
#if !defined MEMP_NUM_NETIFAPI_MSG || defined __DOXYGEN__
#define MEMP_NUM_NETIFAPI_MSG           MEMP_NUM_TCPIP_MSG_API
#endif
#if !defined LWIP_ARP || defined __DOXYGEN__
#define LWIP_ARP                        1
#endif
#if !defined ARP_TABLE_SIZE || defined __DOXYGEN__
#define ARP_TABLE_SIZE                  10
#endif
#if !defined ARP_MAXAGE || defined __DOXYGEN__
#define ARP_MAXAGE                      300
#endif
#if !defined ARP_QUEUEING || defined __DOXYGEN__
#define ARP_QUEUEING                    0
#endif
#if !defined ARP_QUEUE_LEN || defined __DOXYGEN__
#define ARP_QUEUE_LEN                   3
#endif
#if !defined ETHARP_SUPPORT_VLAN || defined __DOXYGEN__
#define ETHARP_SUPPORT_VLAN             0
#endif
#if !defined LWIP_ETHERNET || defined __DOXYGEN__
#define LWIP_ETHERNET                   LWIP_ARP
#endif
#if !defined ETH_PAD_SIZE || defined __DOXYGEN__
#define ETH_PAD_SIZE                    0
#endif
#if !defined ETHARP_SUPPORT_STATIC_ENTRIES || defined __DOXYGEN__
#define ETHARP_SUPPORT_STATIC_ENTRIES   0
#endif
#if !defined ETHARP_TABLE_MATCH_NETIF || defined __DOXYGEN__
#define ETHARP_TABLE_MATCH_NETIF        !LWIP_SINGLE_NETIF
#endif
#if !defined LWIP_IPV4 || defined __DOXYGEN__
#define LWIP_IPV4                       1
#endif
#if !defined IP_FORWARD || defined __DOXYGEN__
#define IP_FORWARD                      0
#endif
#if !defined IP_REASSEMBLY || defined __DOXYGEN__
#define IP_REASSEMBLY                   1
#endif
#if !defined IP_FRAG || defined __DOXYGEN__
#define IP_FRAG                         1
#endif
#if !LWIP_IPV4
#undef IP_FORWARD
#define IP_FORWARD                      0
#undef IP_REASSEMBLY
#define IP_REASSEMBLY                   0
#undef IP_FRAG
#define IP_FRAG                         0
#endif
#if !defined IP_OPTIONS_ALLOWED || defined __DOXYGEN__
#define IP_OPTIONS_ALLOWED              1
#endif
#if !defined IP_REASS_MAXAGE || defined __DOXYGEN__
#define IP_REASS_MAXAGE                 15
#endif
#if !defined IP_REASS_MAX_PBUFS || defined __DOXYGEN__
#define IP_REASS_MAX_PBUFS              10
#endif
#if !defined IP_DEFAULT_TTL || defined __DOXYGEN__
#define IP_DEFAULT_TTL                  255
#endif
#if !defined IP_SOF_BROADCAST || defined __DOXYGEN__
#define IP_SOF_BROADCAST                0
#endif
#if !defined IP_SOF_BROADCAST_RECV || defined __DOXYGEN__
#define IP_SOF_BROADCAST_RECV           0
#endif
#if !defined IP_FORWARD_ALLOW_TX_ON_RX_NETIF || defined __DOXYGEN__
#define IP_FORWARD_ALLOW_TX_ON_RX_NETIF 0
#endif
#if !defined LWIP_ICMP || defined __DOXYGEN__
#define LWIP_ICMP                       1
#endif
#if !defined ICMP_TTL || defined __DOXYGEN__
#define ICMP_TTL                        IP_DEFAULT_TTL
#endif
#if !defined LWIP_BROADCAST_PING || defined __DOXYGEN__
#define LWIP_BROADCAST_PING             0
#endif
#if !defined LWIP_MULTICAST_PING || defined __DOXYGEN__
#define LWIP_MULTICAST_PING             0
#endif
#if !defined LWIP_RAW || defined __DOXYGEN__
#define LWIP_RAW                        0
#endif
#if !defined RAW_TTL || defined __DOXYGEN__
#define RAW_TTL                         IP_DEFAULT_TTL
#endif
#if !defined LWIP_DHCP || defined __DOXYGEN__
#define LWIP_DHCP                       0
#endif
#if !LWIP_IPV4
#undef LWIP_DHCP
#define LWIP_DHCP                       0
#endif
#if !defined DHCP_DOES_ARP_CHECK || defined __DOXYGEN__
#define DHCP_DOES_ARP_CHECK             (LWIP_DHCP && LWIP_ARP)
#endif
#if !defined LWIP_DHCP_BOOTP_FILE || defined __DOXYGEN__
#define LWIP_DHCP_BOOTP_FILE            0
#endif
#if !defined LWIP_DHCP_GET_NTP_SRV || defined __DOXYGEN__
#define LWIP_DHCP_GET_NTP_SRV           0
#endif
#if !defined LWIP_DHCP_MAX_NTP_SERVERS || defined __DOXYGEN__
#define LWIP_DHCP_MAX_NTP_SERVERS       1
#endif
#if !defined LWIP_DHCP_MAX_DNS_SERVERS || defined __DOXYGEN__
#define LWIP_DHCP_MAX_DNS_SERVERS       DNS_MAX_SERVERS
#endif
#if !defined LWIP_AUTOIP || defined __DOXYGEN__
#define LWIP_AUTOIP                     0
#endif
#if !LWIP_IPV4
#undef LWIP_AUTOIP
#define LWIP_AUTOIP                     0
#endif
#if !defined LWIP_DHCP_AUTOIP_COOP || defined __DOXYGEN__
#define LWIP_DHCP_AUTOIP_COOP           0
#endif
#if !defined LWIP_DHCP_AUTOIP_COOP_TRIES || defined __DOXYGEN__
#define LWIP_DHCP_AUTOIP_COOP_TRIES     9
#endif
#if !defined LWIP_MIB2_CALLBACKS || defined __DOXYGEN__
#define LWIP_MIB2_CALLBACKS             0
#endif
#if !defined LWIP_MULTICAST_TX_OPTIONS || defined __DOXYGEN__
#define LWIP_MULTICAST_TX_OPTIONS       ((LWIP_IGMP || LWIP_IPV6_MLD) && (LWIP_UDP || LWIP_RAW))
#endif
#if !defined LWIP_IGMP || defined __DOXYGEN__
#define LWIP_IGMP                       0
#endif
#if !LWIP_IPV4
#undef LWIP_IGMP
#define LWIP_IGMP                       0
#endif
#if !defined LWIP_DNS || defined __DOXYGEN__
#define LWIP_DNS                        1
#endif
#if !defined DNS_TABLE_SIZE || defined __DOXYGEN__
#define DNS_TABLE_SIZE                  4
#endif
#if !defined DNS_MAX_NAME_LENGTH || defined __DOXYGEN__
#define DNS_MAX_NAME_LENGTH             256
#endif
#if !defined DNS_MAX_SERVERS || defined __DOXYGEN__
#define DNS_MAX_SERVERS                 2
#endif
#if !defined DNS_MAX_RETRIES || defined __DOXYGEN__
#define DNS_MAX_RETRIES                 4
#endif
#if !defined DNS_DOES_NAME_CHECK || defined __DOXYGEN__
#define DNS_DOES_NAME_CHECK             1
#endif
#if !defined LWIP_DNS_SECURE || defined __DOXYGEN__
#define LWIP_DNS_SECURE (LWIP_DNS_SECURE_RAND_XID | LWIP_DNS_SECURE_NO_MULTIPLE_OUTSTANDING | LWIP_DNS_SECURE_RAND_SRC_PORT)
#endif
#define LWIP_DNS_SECURE_RAND_XID                1
#define LWIP_DNS_SECURE_NO_MULTIPLE_OUTSTANDING 2
#define LWIP_DNS_SECURE_RAND_SRC_PORT           4
#if !defined DNS_LOCAL_HOSTLIST || defined __DOXYGEN__
#define DNS_LOCAL_HOSTLIST              0
#endif
#if !defined DNS_LOCAL_HOSTLIST_IS_DYNAMIC || defined __DOXYGEN__
#define DNS_LOCAL_HOSTLIST_IS_DYNAMIC   0
#endif
#if !defined LWIP_DNS_SUPPORT_MDNS_QUERIES || defined __DOXYGEN__
#define LWIP_DNS_SUPPORT_MDNS_QUERIES   0
#endif
#if !defined LWIP_UDP || defined __DOXYGEN__
#define LWIP_UDP                        1
#endif
#if !defined LWIP_UDPLITE || defined __DOXYGEN__
#define LWIP_UDPLITE                    0
#endif
#if !defined UDP_TTL || defined __DOXYGEN__
#define UDP_TTL                         IP_DEFAULT_TTL
#endif
#if !defined LWIP_NETBUF_RECVINFO || defined __DOXYGEN__
#define LWIP_NETBUF_RECVINFO            0
#endif
#if !defined LWIP_TCP || defined __DOXYGEN__
#define LWIP_TCP                        1
#endif
#if !defined TCP_TTL || defined __DOXYGEN__
#define TCP_TTL                         IP_DEFAULT_TTL
#endif
#if !defined TCP_WND || defined __DOXYGEN__
#define TCP_WND                         (4 * TCP_MSS)
#endif
#if !defined TCP_MAXRTX || defined __DOXYGEN__
#define TCP_MAXRTX                      12
#endif
#if !defined TCP_SYNMAXRTX || defined __DOXYGEN__
#define TCP_SYNMAXRTX                   6
#endif
#if !defined TCP_QUEUE_OOSEQ || defined __DOXYGEN__
#define TCP_QUEUE_OOSEQ                 LWIP_TCP
#endif
#if !defined LWIP_TCP_SACK_OUT || defined __DOXYGEN__
#define LWIP_TCP_SACK_OUT               1
#endif
#if !defined LWIP_TCP_MAX_SACK_NUM || defined __DOXYGEN__
#define LWIP_TCP_MAX_SACK_NUM           4
#endif
#if !defined TCP_MSS || defined __DOXYGEN__
#define TCP_MSS                         536
#endif
#if !defined TCP_CALCULATE_EFF_SEND_MSS || defined __DOXYGEN__
#define TCP_CALCULATE_EFF_SEND_MSS      1
#endif
#if !defined TCP_SND_BUF || defined __DOXYGEN__
#define TCP_SND_BUF                     (2 * TCP_MSS)
#endif
#if !defined TCP_SND_QUEUELEN || defined __DOXYGEN__
#define TCP_SND_QUEUELEN                ((4 * (TCP_SND_BUF) + (TCP_MSS - 1))/(TCP_MSS))
#endif
#if !defined TCP_SNDLOWAT || defined __DOXYGEN__
#define TCP_SNDLOWAT                    LWIP_MIN(LWIP_MAX(((TCP_SND_BUF)/2), (2 * TCP_MSS) + 1), (TCP_SND_BUF) - 1)
#endif
#if !defined TCP_SNDQUEUELOWAT || defined __DOXYGEN__
#define TCP_SNDQUEUELOWAT               LWIP_MAX(((TCP_SND_QUEUELEN)/2), 5)
#endif
#if !defined TCP_OOSEQ_MAX_BYTES || defined __DOXYGEN__
#define TCP_OOSEQ_MAX_BYTES             0
#endif
#if !defined TCP_OOSEQ_BYTES_LIMIT
#if TCP_OOSEQ_MAX_BYTES
#define TCP_OOSEQ_BYTES_LIMIT(pcb)      TCP_OOSEQ_MAX_BYTES
#elif defined __DOXYGEN__
#define TCP_OOSEQ_BYTES_LIMIT(pcb)
#endif
#endif
#if !defined TCP_OOSEQ_MAX_PBUFS || defined __DOXYGEN__
#define TCP_OOSEQ_MAX_PBUFS             0
#endif
#if !defined TCP_OOSEQ_PBUFS_LIMIT
#if TCP_OOSEQ_MAX_PBUFS
#define TCP_OOSEQ_PBUFS_LIMIT(pcb)      TCP_OOSEQ_MAX_PBUFS
#elif defined __DOXYGEN__
#define TCP_OOSEQ_PBUFS_LIMIT(pcb)
#endif
#endif
#if !defined TCP_LISTEN_BACKLOG || defined __DOXYGEN__
#define TCP_LISTEN_BACKLOG              0
#endif
#if !defined TCP_DEFAULT_LISTEN_BACKLOG || defined __DOXYGEN__
#define TCP_DEFAULT_LISTEN_BACKLOG      0xff
#endif
#if !defined TCP_OVERSIZE || defined __DOXYGEN__
#define TCP_OVERSIZE                    TCP_MSS
#endif
#if !defined LWIP_TCP_TIMESTAMPS || defined __DOXYGEN__
#define LWIP_TCP_TIMESTAMPS             0
#endif
#if !defined TCP_WND_UPDATE_THRESHOLD || defined __DOXYGEN__
#define TCP_WND_UPDATE_THRESHOLD        LWIP_MIN((TCP_WND / 4), (TCP_MSS * 4))
#endif
#if !defined(LWIP_EVENT_API) && !defined(LWIP_CALLBACK_API) || defined __DOXYGEN__
#define LWIP_EVENT_API                  0
#define LWIP_CALLBACK_API               1
#else
#ifndef LWIP_EVENT_API
#define LWIP_EVENT_API                  0
#endif
#ifndef LWIP_CALLBACK_API
#define LWIP_CALLBACK_API               0
#endif
#endif
#if !defined LWIP_WND_SCALE || defined __DOXYGEN__
#define LWIP_WND_SCALE                  0
#define TCP_RCV_SCALE                   0
#endif
#if !defined LWIP_TCP_PCB_NUM_EXT_ARGS || defined __DOXYGEN__
#define LWIP_TCP_PCB_NUM_EXT_ARGS       0
#endif
#if !defined LWIP_ALTCP || defined __DOXYGEN__
#define LWIP_ALTCP                      1
#endif
#if !defined LWIP_ALTCP_TLS || defined __DOXYGEN__
#define LWIP_ALTCP_TLS                  1
#endif
#if !defined PBUF_LINK_HLEN || defined __DOXYGEN__
#if defined LWIP_HOOK_VLAN_SET && !defined __DOXYGEN__
#define PBUF_LINK_HLEN                  (18 + ETH_PAD_SIZE)
#else
#define PBUF_LINK_HLEN                  (14 + ETH_PAD_SIZE)
#endif
#endif
#if !defined PBUF_LINK_ENCAPSULATION_HLEN || defined __DOXYGEN__
#define PBUF_LINK_ENCAPSULATION_HLEN    0
#endif
#if !defined PBUF_POOL_BUFSIZE || defined __DOXYGEN__
#define PBUF_POOL_BUFSIZE               LWIP_MEM_ALIGN_SIZE(TCP_MSS+PBUF_IP_HLEN+PBUF_TRANSPORT_HLEN+PBUF_LINK_ENCAPSULATION_HLEN+PBUF_LINK_HLEN)
#endif
#if !defined LWIP_PBUF_REF_T || defined __DOXYGEN__
#define LWIP_PBUF_REF_T                 u8_t
#endif
#if !defined LWIP_PBUF_CUSTOM_DATA || defined __DOXYGEN__
#define LWIP_PBUF_CUSTOM_DATA
#endif
#if !defined LWIP_SINGLE_NETIF || defined __DOXYGEN__
#define LWIP_SINGLE_NETIF               0
#endif
#if !defined LWIP_NETIF_HOSTNAME || defined __DOXYGEN__
#define LWIP_NETIF_HOSTNAME             0
#endif
#if !defined LWIP_NETIF_API || defined __DOXYGEN__
#define LWIP_NETIF_API                  0
#endif
#if !defined LWIP_NETIF_STATUS_CALLBACK || defined __DOXYGEN__
#define LWIP_NETIF_STATUS_CALLBACK      0
#endif
#if !defined LWIP_NETIF_EXT_STATUS_CALLBACK || defined __DOXYGEN__
#define LWIP_NETIF_EXT_STATUS_CALLBACK  0
#endif
#if !defined LWIP_NETIF_LINK_CALLBACK || defined __DOXYGEN__
#define LWIP_NETIF_LINK_CALLBACK        0
#endif
#if !defined LWIP_NETIF_REMOVE_CALLBACK || defined __DOXYGEN__
#define LWIP_NETIF_REMOVE_CALLBACK      0
#endif
#if !defined LWIP_NETIF_HWADDRHINT || defined __DOXYGEN__
#define LWIP_NETIF_HWADDRHINT           0
#endif
#if !defined LWIP_NETIF_TX_SINGLE_PBUF || defined __DOXYGEN__
#define LWIP_NETIF_TX_SINGLE_PBUF       0
#endif
#if !defined LWIP_NUM_NETIF_CLIENT_DATA || defined __DOXYGEN__
#define LWIP_NUM_NETIF_CLIENT_DATA      0
#endif
#if !defined LWIP_HAVE_LOOPIF || defined __DOXYGEN__
#define LWIP_HAVE_LOOPIF                (LWIP_NETIF_LOOPBACK && !LWIP_SINGLE_NETIF)
#endif
#if !defined LWIP_LOOPIF_MULTICAST || defined __DOXYGEN__
#define LWIP_LOOPIF_MULTICAST           0
#endif
#if !defined LWIP_NETIF_LOOPBACK || defined __DOXYGEN__
#define LWIP_NETIF_LOOPBACK             0
#endif
#if !defined LWIP_LOOPBACK_MAX_PBUFS || defined __DOXYGEN__
#define LWIP_LOOPBACK_MAX_PBUFS         0
#endif
#if !defined LWIP_NETIF_LOOPBACK_MULTITHREADING || defined __DOXYGEN__
#define LWIP_NETIF_LOOPBACK_MULTITHREADING    (!NO_SYS)
#endif
#if !defined TCPIP_THREAD_NAME || defined __DOXYGEN__
#define TCPIP_THREAD_NAME               "tcpip_thread"
#endif
#if !defined TCPIP_THREAD_STACKSIZE || defined __DOXYGEN__
#define TCPIP_THREAD_STACKSIZE          0
#endif
#if !defined TCPIP_THREAD_PRIO || defined __DOXYGEN__
#define TCPIP_THREAD_PRIO               1
#endif
#if !defined TCPIP_MBOX_SIZE || defined __DOXYGEN__
#define TCPIP_MBOX_SIZE                 0
#endif
#if !defined LWIP_TCPIP_THREAD_ALIVE || defined __DOXYGEN__
#define LWIP_TCPIP_THREAD_ALIVE()
#endif
#if !defined SLIPIF_THREAD_NAME || defined __DOXYGEN__
#define SLIPIF_THREAD_NAME              "slipif_loop"
#endif
#if !defined SLIPIF_THREAD_STACKSIZE || defined __DOXYGEN__
#define SLIPIF_THREAD_STACKSIZE         0
#endif
#if !defined SLIPIF_THREAD_PRIO || defined __DOXYGEN__
#define SLIPIF_THREAD_PRIO              1
#endif
#if !defined DEFAULT_THREAD_NAME || defined __DOXYGEN__
#define DEFAULT_THREAD_NAME             "lwIP"
#endif
#if !defined DEFAULT_THREAD_STACKSIZE || defined __DOXYGEN__
#define DEFAULT_THREAD_STACKSIZE        0
#endif
#if !defined DEFAULT_THREAD_PRIO || defined __DOXYGEN__
#define DEFAULT_THREAD_PRIO             1
#endif
#if !defined DEFAULT_RAW_RECVMBOX_SIZE || defined __DOXYGEN__
#define DEFAULT_RAW_RECVMBOX_SIZE       0
#endif
#if !defined DEFAULT_UDP_RECVMBOX_SIZE || defined __DOXYGEN__
#define DEFAULT_UDP_RECVMBOX_SIZE       0
#endif
#if !defined DEFAULT_TCP_RECVMBOX_SIZE || defined __DOXYGEN__
#define DEFAULT_TCP_RECVMBOX_SIZE       0
#endif
#if !defined DEFAULT_ACCEPTMBOX_SIZE || defined __DOXYGEN__
#define DEFAULT_ACCEPTMBOX_SIZE         0
#endif
#if !defined LWIP_NETCONN || defined __DOXYGEN__
#define LWIP_NETCONN                    1
#endif
#if !defined LWIP_TCPIP_TIMEOUT || defined __DOXYGEN__
#define LWIP_TCPIP_TIMEOUT              0
#endif
#if !defined LWIP_NETCONN_SEM_PER_THREAD || defined __DOXYGEN__
#define LWIP_NETCONN_SEM_PER_THREAD     0
#endif
#if !defined LWIP_NETCONN_FULLDUPLEX || defined __DOXYGEN__
#define LWIP_NETCONN_FULLDUPLEX         0
#endif
#if !defined LWIP_SOCKET || defined __DOXYGEN__
#define LWIP_SOCKET                     1
#endif
#if !defined LWIP_COMPAT_SOCKETS || defined __DOXYGEN__
#define LWIP_COMPAT_SOCKETS             1
#endif
#if !defined LWIP_POSIX_SOCKETS_IO_NAMES || defined __DOXYGEN__
#define LWIP_POSIX_SOCKETS_IO_NAMES     1
#endif
#if !defined LWIP_SOCKET_OFFSET || defined __DOXYGEN__
#define LWIP_SOCKET_OFFSET              0
#endif
#if !defined LWIP_TCP_KEEPALIVE || defined __DOXYGEN__
#define LWIP_TCP_KEEPALIVE              0
#endif
#if !defined LWIP_SO_SNDTIMEO || defined __DOXYGEN__
#define LWIP_SO_SNDTIMEO                0
#endif
#if !defined LWIP_SO_RCVTIMEO || defined __DOXYGEN__
#define LWIP_SO_RCVTIMEO                0
#endif
#if !defined LWIP_SO_SNDRCVTIMEO_NONSTANDARD || defined __DOXYGEN__
#define LWIP_SO_SNDRCVTIMEO_NONSTANDARD 0
#endif
#if !defined LWIP_SO_RCVBUF || defined __DOXYGEN__
#define LWIP_SO_RCVBUF                  0
#endif
#if !defined LWIP_SO_LINGER || defined __DOXYGEN__
#define LWIP_SO_LINGER                  0
#endif
#if !defined RECV_BUFSIZE_DEFAULT || defined __DOXYGEN__
#define RECV_BUFSIZE_DEFAULT            INT_MAX
#endif
#if !defined LWIP_TCP_CLOSE_TIMEOUT_MS_DEFAULT || defined __DOXYGEN__
#define LWIP_TCP_CLOSE_TIMEOUT_MS_DEFAULT 20000
#endif
#if !defined SO_REUSE || defined __DOXYGEN__
#define SO_REUSE                        0
#endif
#if !defined SO_REUSE_RXTOALL || defined __DOXYGEN__
#define SO_REUSE_RXTOALL                0
#endif
#if !defined LWIP_FIONREAD_LINUXMODE || defined __DOXYGEN__
#define LWIP_FIONREAD_LINUXMODE         0
#endif
#if !defined LWIP_SOCKET_SELECT || defined __DOXYGEN__
#define LWIP_SOCKET_SELECT              1
#endif
#if !defined LWIP_SOCKET_POLL || defined __DOXYGEN__
#define LWIP_SOCKET_POLL                1
#endif
#if !defined LWIP_STATS || defined __DOXYGEN__
#define LWIP_STATS                      1
#endif
#if LWIP_STATS
#if !defined LWIP_STATS_DISPLAY || defined __DOXYGEN__
#define LWIP_STATS_DISPLAY              0
#endif
#if !defined LINK_STATS || defined __DOXYGEN__
#define LINK_STATS                      1
#endif
#if !defined ETHARP_STATS || defined __DOXYGEN__
#define ETHARP_STATS                    (LWIP_ARP)
#endif
#if !defined IP_STATS || defined __DOXYGEN__
#define IP_STATS                        1
#endif
#if !defined IPFRAG_STATS || defined __DOXYGEN__
#define IPFRAG_STATS                    (IP_REASSEMBLY || IP_FRAG)
#endif
#if !defined ICMP_STATS || defined __DOXYGEN__
#define ICMP_STATS                      1
#endif
#if !defined IGMP_STATS || defined __DOXYGEN__
#define IGMP_STATS                      (LWIP_IGMP)
#endif
#if !defined UDP_STATS || defined __DOXYGEN__
#define UDP_STATS                       (LWIP_UDP)
#endif
#if !defined TCP_STATS || defined __DOXYGEN__
#define TCP_STATS                       (LWIP_TCP)
#endif
#if !defined MEM_STATS || defined __DOXYGEN__
#define MEM_STATS                       ((MEM_LIBC_MALLOC == 0) && (MEM_USE_POOLS == 0))
#endif
#if !defined MEMP_STATS || defined __DOXYGEN__
#define MEMP_STATS                      (MEMP_MEM_MALLOC == 0)
#endif
#if !defined SYS_STATS || defined __DOXYGEN__
#define SYS_STATS                       (NO_SYS == 0)
#endif
#if !defined IP6_STATS || defined __DOXYGEN__
#define IP6_STATS                       (LWIP_IPV6)
#endif
#if !defined ICMP6_STATS || defined __DOXYGEN__
#define ICMP6_STATS                     (LWIP_IPV6 && LWIP_ICMP6)
#endif
#if !defined IP6_FRAG_STATS || defined __DOXYGEN__
#define IP6_FRAG_STATS                  (LWIP_IPV6 && (LWIP_IPV6_FRAG || LWIP_IPV6_REASS))
#endif
#if !defined MLD6_STATS || defined __DOXYGEN__
#define MLD6_STATS                      (LWIP_IPV6 && LWIP_IPV6_MLD)
#endif
#if !defined ND6_STATS || defined __DOXYGEN__
#define ND6_STATS                       (LWIP_IPV6)
#endif
#if !defined MIB2_STATS || defined __DOXYGEN__
#define MIB2_STATS                      0
#endif
#else
#define LINK_STATS                      0
#define ETHARP_STATS                    0
#define IP_STATS                        0
#define IPFRAG_STATS                    0
#define ICMP_STATS                      0
#define IGMP_STATS                      0
#define UDP_STATS                       0
#define TCP_STATS                       0
#define MEM_STATS                       0
#define MEMP_STATS                      0
#define SYS_STATS                       0
#define LWIP_STATS_DISPLAY              0
#define IP6_STATS                       0
#define ICMP6_STATS                     0
#define IP6_FRAG_STATS                  0
#define MLD6_STATS                      0
#define ND6_STATS                       0
#define MIB2_STATS                      0
#endif
#if !defined LWIP_CHECKSUM_CTRL_PER_NETIF || defined __DOXYGEN__
#define LWIP_CHECKSUM_CTRL_PER_NETIF    0
#endif
#if !defined CHECKSUM_GEN_IP || defined __DOXYGEN__
#define CHECKSUM_GEN_IP                 1
#endif
#if !defined CHECKSUM_GEN_UDP || defined __DOXYGEN__
#define CHECKSUM_GEN_UDP                1
#endif
#if !defined CHECKSUM_GEN_TCP || defined __DOXYGEN__
#define CHECKSUM_GEN_TCP                1
#endif
#if !defined CHECKSUM_GEN_ICMP || defined __DOXYGEN__
#define CHECKSUM_GEN_ICMP               1
#endif
#if !defined CHECKSUM_GEN_ICMP6 || defined __DOXYGEN__
#define CHECKSUM_GEN_ICMP6              1
#endif
#if !defined CHECKSUM_CHECK_IP || defined __DOXYGEN__
#define CHECKSUM_CHECK_IP               1
#endif
#if !defined CHECKSUM_CHECK_UDP || defined __DOXYGEN__
#define CHECKSUM_CHECK_UDP              1
#endif
#if !defined CHECKSUM_CHECK_TCP || defined __DOXYGEN__
#define CHECKSUM_CHECK_TCP              1
#endif
#if !defined CHECKSUM_CHECK_ICMP || defined __DOXYGEN__
#define CHECKSUM_CHECK_ICMP             1
#endif
#if !defined CHECKSUM_CHECK_ICMP6 || defined __DOXYGEN__
#define CHECKSUM_CHECK_ICMP6            1
#endif
#if !defined LWIP_CHECKSUM_ON_COPY || defined __DOXYGEN__
#define LWIP_CHECKSUM_ON_COPY           0
#endif
#if !defined LWIP_IPV6 || defined __DOXYGEN__
#define LWIP_IPV6                       0
#endif
#if !defined IPV6_REASS_MAXAGE || defined __DOXYGEN__
#define IPV6_REASS_MAXAGE               60
#endif
#if !defined LWIP_IPV6_SCOPES || defined __DOXYGEN__
#define LWIP_IPV6_SCOPES                (LWIP_IPV6 && !LWIP_SINGLE_NETIF)
#endif
#if !defined LWIP_IPV6_SCOPES_DEBUG || defined __DOXYGEN__
#define LWIP_IPV6_SCOPES_DEBUG          0
#endif
#if !defined LWIP_IPV6_NUM_ADDRESSES || defined __DOXYGEN__
#define LWIP_IPV6_NUM_ADDRESSES         3
#endif
#if !defined LWIP_IPV6_FORWARD || defined __DOXYGEN__
#define LWIP_IPV6_FORWARD               0
#endif
#if !defined LWIP_IPV6_FRAG || defined __DOXYGEN__
#define LWIP_IPV6_FRAG                  1
#endif
#if !defined LWIP_IPV6_REASS || defined __DOXYGEN__
#define LWIP_IPV6_REASS                 LWIP_IPV6
#endif
#if !defined LWIP_IPV6_SEND_ROUTER_SOLICIT || defined __DOXYGEN__
#define LWIP_IPV6_SEND_ROUTER_SOLICIT   LWIP_IPV6
#endif
#if !defined LWIP_IPV6_AUTOCONFIG || defined __DOXYGEN__
#define LWIP_IPV6_AUTOCONFIG            LWIP_IPV6
#endif
#if !defined LWIP_IPV6_ADDRESS_LIFETIMES || defined __DOXYGEN__
#define LWIP_IPV6_ADDRESS_LIFETIMES     LWIP_IPV6_AUTOCONFIG
#endif
#if !defined LWIP_IPV6_DUP_DETECT_ATTEMPTS || defined __DOXYGEN__
#define LWIP_IPV6_DUP_DETECT_ATTEMPTS   1
#endif
#if !defined LWIP_ICMP6 || defined __DOXYGEN__
#define LWIP_ICMP6                      LWIP_IPV6
#endif
#if !defined LWIP_ICMP6_DATASIZE || defined __DOXYGEN__
#define LWIP_ICMP6_DATASIZE             0
#endif
#if !defined LWIP_ICMP6_HL || defined __DOXYGEN__
#define LWIP_ICMP6_HL                   255
#endif
#if !defined LWIP_IPV6_MLD || defined __DOXYGEN__
#define LWIP_IPV6_MLD                   LWIP_IPV6
#endif
#if !defined MEMP_NUM_MLD6_GROUP || defined __DOXYGEN__
#define MEMP_NUM_MLD6_GROUP             4
#endif
#if !defined LWIP_ND6_QUEUEING || defined __DOXYGEN__
#define LWIP_ND6_QUEUEING               LWIP_IPV6
#endif
#if !defined MEMP_NUM_ND6_QUEUE || defined __DOXYGEN__
#define MEMP_NUM_ND6_QUEUE              20
#endif
#if !defined LWIP_ND6_NUM_NEIGHBORS || defined __DOXYGEN__
#define LWIP_ND6_NUM_NEIGHBORS          10
#endif
#if !defined LWIP_ND6_NUM_DESTINATIONS || defined __DOXYGEN__
#define LWIP_ND6_NUM_DESTINATIONS       10
#endif
#if !defined LWIP_ND6_NUM_PREFIXES || defined __DOXYGEN__
#define LWIP_ND6_NUM_PREFIXES           5
#endif
#if !defined LWIP_ND6_NUM_ROUTERS || defined __DOXYGEN__
#define LWIP_ND6_NUM_ROUTERS            3
#endif
#if !defined LWIP_ND6_MAX_MULTICAST_SOLICIT || defined __DOXYGEN__
#define LWIP_ND6_MAX_MULTICAST_SOLICIT  3
#endif
#if !defined LWIP_ND6_MAX_UNICAST_SOLICIT || defined __DOXYGEN__
#define LWIP_ND6_MAX_UNICAST_SOLICIT    3
#endif
#if !defined LWIP_ND6_MAX_ANYCAST_DELAY_TIME || defined __DOXYGEN__
#define LWIP_ND6_MAX_ANYCAST_DELAY_TIME 1000
#endif
#if !defined LWIP_ND6_MAX_NEIGHBOR_ADVERTISEMENT || defined __DOXYGEN__
#define LWIP_ND6_MAX_NEIGHBOR_ADVERTISEMENT  3
#endif
#if !defined LWIP_ND6_REACHABLE_TIME || defined __DOXYGEN__
#define LWIP_ND6_REACHABLE_TIME         30000
#endif
#if !defined LWIP_ND6_RETRANS_TIMER || defined __DOXYGEN__
#define LWIP_ND6_RETRANS_TIMER          1000
#endif
#if !defined LWIP_ND6_DELAY_FIRST_PROBE_TIME || defined __DOXYGEN__
#define LWIP_ND6_DELAY_FIRST_PROBE_TIME 5000
#endif
#if !defined LWIP_ND6_ALLOW_RA_UPDATES || defined __DOXYGEN__
#define LWIP_ND6_ALLOW_RA_UPDATES       1
#endif
#if !defined LWIP_ND6_TCP_REACHABILITY_HINTS || defined __DOXYGEN__
#define LWIP_ND6_TCP_REACHABILITY_HINTS 1
#endif
#if !defined LWIP_ND6_RDNSS_MAX_DNS_SERVERS || defined __DOXYGEN__
#define LWIP_ND6_RDNSS_MAX_DNS_SERVERS  0
#endif
#if !defined LWIP_IPV6_DHCP6 || defined __DOXYGEN__
#define LWIP_IPV6_DHCP6                 0
#endif
#if !defined LWIP_IPV6_DHCP6_STATEFUL || defined __DOXYGEN__
#define LWIP_IPV6_DHCP6_STATEFUL        0
#endif
#if !defined LWIP_IPV6_DHCP6_STATELESS || defined __DOXYGEN__
#define LWIP_IPV6_DHCP6_STATELESS       LWIP_IPV6_DHCP6
#endif
#if !defined LWIP_DHCP6_GET_NTP_SRV || defined __DOXYGEN__
#define LWIP_DHCP6_GET_NTP_SRV          0
#endif
#if !defined LWIP_DHCP6_MAX_NTP_SERVERS || defined __DOXYGEN__
#define LWIP_DHCP6_MAX_NTP_SERVERS      1
#endif
#if !defined LWIP_DHCP6_MAX_DNS_SERVERS || defined __DOXYGEN__
#define LWIP_DHCP6_MAX_DNS_SERVERS      DNS_MAX_SERVERS
#endif
#ifdef __DOXYGEN__
#define LWIP_HOOK_FILENAME "path/to/my/lwip_hooks.h"
#endif
#ifdef __DOXYGEN__
#define LWIP_HOOK_TCP_ISN(local_ip, local_port, remote_ip, remote_port)
#endif
#ifdef __DOXYGEN__
#define LWIP_HOOK_TCP_INPACKET_PCB(pcb, hdr, optlen, opt1len, opt2, p)
#endif
#ifdef __DOXYGEN__
#define LWIP_HOOK_TCP_OUT_TCPOPT_LENGTH(pcb, internal_len)
#endif
#ifdef __DOXYGEN__
#define LWIP_HOOK_TCP_OUT_ADD_TCPOPTS(p, hdr, pcb, opts)
#endif
#ifdef __DOXYGEN__
#define LWIP_HOOK_IP4_INPUT(pbuf, input_netif)
#endif
#ifdef __DOXYGEN__
#define LWIP_HOOK_IP4_ROUTE()
#endif
#ifdef __DOXYGEN__
#define LWIP_HOOK_IP4_ROUTE_SRC(src, dest)
#endif
#ifdef __DOXYGEN__
#define LWIP_HOOK_IP4_CANFORWARD(src, dest)
#endif
#ifdef __DOXYGEN__
#define LWIP_HOOK_ETHARP_GET_GW(netif, dest)
#endif
#ifdef __DOXYGEN__
#define LWIP_HOOK_IP6_INPUT(pbuf, input_netif)
#endif
#ifdef __DOXYGEN__
#define LWIP_HOOK_IP6_ROUTE(src, dest)
#endif
#ifdef __DOXYGEN__
#define LWIP_HOOK_ND6_GET_GW(netif, dest)
#endif
#ifdef __DOXYGEN__
#define LWIP_HOOK_VLAN_CHECK(netif, eth_hdr, vlan_hdr)
#endif
#ifdef __DOXYGEN__
#define LWIP_HOOK_VLAN_SET(netif, p, src, dst, eth_type)
#endif
#ifdef __DOXYGEN__
#define LWIP_HOOK_MEMP_AVAILABLE(memp_t_type)
#endif
#ifdef __DOXYGEN__
#define LWIP_HOOK_UNKNOWN_ETH_PROTOCOL(pbuf, netif)
#endif
#ifdef __DOXYGEN__
#define LWIP_HOOK_DHCP_APPEND_OPTIONS(netif, dhcp, state, msg, msg_type, options_len_ptr)
#endif
#ifdef __DOXYGEN__
#define LWIP_HOOK_DHCP_PARSE_OPTION(netif, dhcp, state, msg, msg_type, option, len, pbuf, offset)
#endif
#ifdef __DOXYGEN__
#define LWIP_HOOK_DHCP6_APPEND_OPTIONS(netif, dhcp6, state, msg, msg_type, options_len_ptr, max_len)
#endif
#ifdef __DOXYGEN__
#define LWIP_HOOK_SOCKETS_SETSOCKOPT(s, sock, level, optname, optval, optlen, err)
#endif
#ifdef __DOXYGEN__
#define LWIP_HOOK_SOCKETS_GETSOCKOPT(s, sock, level, optname, optval, optlen, err)
#endif
#ifdef __DOXYGEN__
#define LWIP_HOOK_NETCONN_EXTERNAL_RESOLVE(name, addr, addrtype, err)
#endif
#if !defined LWIP_DBG_MIN_LEVEL || defined __DOXYGEN__
#define LWIP_DBG_MIN_LEVEL              LWIP_DBG_LEVEL_ALL
#endif
#if !defined LWIP_DBG_TYPES_ON || defined __DOXYGEN__
#define LWIP_DBG_TYPES_ON               LWIP_DBG_ON
#endif
#if !defined ETHARP_DEBUG || defined __DOXYGEN__
#define ETHARP_DEBUG                    LWIP_DBG_OFF
#endif
#if !defined NETIF_DEBUG || defined __DOXYGEN__
#define NETIF_DEBUG                     LWIP_DBG_OFF
#endif
#if !defined PBUF_DEBUG || defined __DOXYGEN__
#define PBUF_DEBUG                      LWIP_DBG_OFF
#endif
#if !defined API_LIB_DEBUG || defined __DOXYGEN__
#define API_LIB_DEBUG                   LWIP_DBG_OFF
#endif
#if !defined API_MSG_DEBUG || defined __DOXYGEN__
#define API_MSG_DEBUG                   LWIP_DBG_OFF
#endif
#if !defined SOCKETS_DEBUG || defined __DOXYGEN__
#define SOCKETS_DEBUG                   LWIP_DBG_OFF
#endif
#if !defined ICMP_DEBUG || defined __DOXYGEN__
#define ICMP_DEBUG                      LWIP_DBG_OFF
#endif
#if !defined IGMP_DEBUG || defined __DOXYGEN__
#define IGMP_DEBUG                      LWIP_DBG_OFF
#endif
#if !defined INET_DEBUG || defined __DOXYGEN__
#define INET_DEBUG                      LWIP_DBG_OFF
#endif
#if !defined IP_DEBUG || defined __DOXYGEN__
#define IP_DEBUG                        LWIP_DBG_OFF
#endif
#if !defined IP_REASS_DEBUG || defined __DOXYGEN__
#define IP_REASS_DEBUG                  LWIP_DBG_OFF
#endif
#if !defined RAW_DEBUG || defined __DOXYGEN__
#define RAW_DEBUG                       LWIP_DBG_OFF
#endif
#if !defined MEM_DEBUG || defined __DOXYGEN__
#define MEM_DEBUG                       LWIP_DBG_OFF
#endif
#if !defined MEMP_DEBUG || defined __DOXYGEN__
#define MEMP_DEBUG                      LWIP_DBG_OFF
#endif
#if !defined SYS_DEBUG || defined __DOXYGEN__
#define SYS_DEBUG                       LWIP_DBG_OFF
#endif
#if !defined TIMERS_DEBUG || defined __DOXYGEN__
#define TIMERS_DEBUG                    LWIP_DBG_OFF
#endif
#if !defined TCP_DEBUG || defined __DOXYGEN__
#define TCP_DEBUG                       LWIP_DBG_OFF
#endif
#if !defined TCP_INPUT_DEBUG || defined __DOXYGEN__
#define TCP_INPUT_DEBUG                 LWIP_DBG_OFF
#endif
#if !defined TCP_FR_DEBUG || defined __DOXYGEN__
#define TCP_FR_DEBUG                    LWIP_DBG_OFF
#endif
#if !defined TCP_RTO_DEBUG || defined __DOXYGEN__
#define TCP_RTO_DEBUG                   LWIP_DBG_OFF
#endif
#if !defined TCP_CWND_DEBUG || defined __DOXYGEN__
#define TCP_CWND_DEBUG                  LWIP_DBG_OFF
#endif
#if !defined TCP_WND_DEBUG || defined __DOXYGEN__
#define TCP_WND_DEBUG                   LWIP_DBG_OFF
#endif
#if !defined TCP_OUTPUT_DEBUG || defined __DOXYGEN__
#define TCP_OUTPUT_DEBUG                LWIP_DBG_OFF
#endif
#if !defined TCP_RST_DEBUG || defined __DOXYGEN__
#define TCP_RST_DEBUG                   LWIP_DBG_OFF
#endif
#if !defined TCP_QLEN_DEBUG || defined __DOXYGEN__
#define TCP_QLEN_DEBUG                  LWIP_DBG_OFF
#endif
#if !defined UDP_DEBUG || defined __DOXYGEN__
#define UDP_DEBUG                       LWIP_DBG_OFF
#endif
#if !defined TCPIP_DEBUG || defined __DOXYGEN__
#define TCPIP_DEBUG                     LWIP_DBG_OFF
#endif
#if !defined SLIP_DEBUG || defined __DOXYGEN__
#define SLIP_DEBUG                      LWIP_DBG_OFF
#endif
#if !defined DHCP_DEBUG || defined __DOXYGEN__
#define DHCP_DEBUG                      LWIP_DBG_OFF
#endif
#if !defined AUTOIP_DEBUG || defined __DOXYGEN__
#define AUTOIP_DEBUG                    LWIP_DBG_OFF
#endif
#if !defined DNS_DEBUG || defined __DOXYGEN__
#define DNS_DEBUG                       LWIP_DBG_OFF
#endif
#if !defined IP6_DEBUG || defined __DOXYGEN__
#define IP6_DEBUG                       LWIP_DBG_OFF
#endif
#if !defined DHCP6_DEBUG || defined __DOXYGEN__
#define DHCP6_DEBUG                     LWIP_DBG_OFF
#endif
#if !defined LWIP_TESTMODE
#define LWIP_TESTMODE                   0
#endif
#if !defined LWIP_PERF || defined __DOXYGEN__
#define LWIP_PERF                       0
#endif
#endif
