shanshe/Z3660/z3660-firmware/Z-TURN/vivado/z3660.gen/sources_1/bd/design_1/ip/design_1_processing_system7_0_0/design_1_processing_system7_0_0.xdc

############################################################################
##
##  Xilinx, Inc. 2006            www.xilinx.com
############################################################################
##  File name :       ps7_constraints.xdc
##
##  Details :     Constraints file
##                    FPGA family:       zynq
##                    FPGA:              xc7z020clg400-3
##                    Device Size:        xc7z020
##                    Package:            clg400
##                    Speedgrade:         -3
##
##
############################################################################
############################################################################
############################################################################
# Clock constraints                                                        #
############################################################################
create_clock -name clk_fpga_0 -period "5" [get_pins "PS7_i/FCLKCLK[0]"]
set_input_jitter clk_fpga_0 0.15
#The clocks are asynchronous, user should constrain them appropriately.#
create_clock -name clk_fpga_2 -period "10" [get_pins "PS7_i/FCLKCLK[2]"]
set_input_jitter clk_fpga_2 0.3
#The clocks are asynchronous, user should constrain them appropriately.#
create_clock -name clk_fpga_1 -period "10" [get_pins "PS7_i/FCLKCLK[1]"]
set_input_jitter clk_fpga_1 0.3
#The clocks are asynchronous, user should constrain them appropriately.#


############################################################################
# I/O STANDARDS and Location Constraints                                   #
############################################################################

#  Enet 0 / mdio / MIO[53]
set_property iostandard "LVCMOS18" [get_ports "MIO[53]"]
set_property PACKAGE_PIN "C11" [get_ports "MIO[53]"]
set_property slew "slow" [get_ports "MIO[53]"]
set_property drive "8" [get_ports "MIO[53]"]
set_property pullup "TRUE" [get_ports "MIO[53]"]
set_property PIO_DIRECTION "BIDIR" [get_ports "MIO[53]"]
#  Enet 0 / mdc / MIO[52]
set_property iostandard "LVCMOS18" [get_ports "MIO[52]"]
set_property PACKAGE_PIN "C10" [get_ports "MIO[52]"]
set_property slew "slow" [get_ports "MIO[52]"]
set_property drive "8" [get_ports "MIO[52]"]
set_property pullup "TRUE" [get_ports "MIO[52]"]
set_property PIO_DIRECTION "OUTPUT" [get_ports "MIO[52]"]
#  USB Reset / reset / MIO[51]
set_property iostandard "LVCMOS18" [get_ports "MIO[51]"]
set_property PACKAGE_PIN "B9" [get_ports "MIO[51]"]
set_property slew "slow" [get_ports "MIO[51]"]
set_property drive "8" [get_ports "MIO[51]"]
set_property PIO_DIRECTION "OUTPUT" [get_ports "MIO[51]"]
#  GPIO / gpio[50] / MIO[50]
set_property iostandard "LVCMOS18" [get_ports "MIO[50]"]
set_property PACKAGE_PIN "B13" [get_ports "MIO[50]"]
set_property slew "slow" [get_ports "MIO[50]"]
set_property drive "8" [get_ports "MIO[50]"]
set_property PIO_DIRECTION "BIDIR" [get_ports "MIO[50]"]
#  UART 1 / rx / MIO[49]
set_property iostandard "LVCMOS18" [get_ports "MIO[49]"]
set_property PACKAGE_PIN "C12" [get_ports "MIO[49]"]
set_property slew "slow" [get_ports "MIO[49]"]
set_property drive "8" [get_ports "MIO[49]"]
set_property pullup "TRUE" [get_ports "MIO[49]"]
set_property PIO_DIRECTION "INPUT" [get_ports "MIO[49]"]
#  UART 1 / tx / MIO[48]
set_property iostandard "LVCMOS18" [get_ports "MIO[48]"]
set_property PACKAGE_PIN "B12" [get_ports "MIO[48]"]
set_property slew "slow" [get_ports "MIO[48]"]
set_property drive "8" [get_ports "MIO[48]"]
set_property pullup "TRUE" [get_ports "MIO[48]"]
set_property PIO_DIRECTION "OUTPUT" [get_ports "MIO[48]"]
#  SD 0 / wp / MIO[47]
set_property iostandard "LVCMOS18" [get_ports "MIO[47]"]
set_property PACKAGE_PIN "B14" [get_ports "MIO[47]"]
set_property slew "slow" [get_ports "MIO[47]"]
set_property drive "8" [get_ports "MIO[47]"]
set_property PIO_DIRECTION "INPUT" [get_ports "MIO[47]"]
#  SD 0 / cd / MIO[46]
set_property iostandard "LVCMOS18" [get_ports "MIO[46]"]
set_property PACKAGE_PIN "D16" [get_ports "MIO[46]"]
set_property slew "slow" [get_ports "MIO[46]"]
set_property drive "8" [get_ports "MIO[46]"]
set_property PIO_DIRECTION "INPUT" [get_ports "MIO[46]"]
#  SD 0 / data[3] / MIO[45]
set_property iostandard "LVCMOS18" [get_ports "MIO[45]"]
set_property PACKAGE_PIN "B15" [get_ports "MIO[45]"]
set_property slew "slow" [get_ports "MIO[45]"]
set_property drive "8" [get_ports "MIO[45]"]
set_property pullup "TRUE" [get_ports "MIO[45]"]
set_property PIO_DIRECTION "BIDIR" [get_ports "MIO[45]"]
#  SD 0 / data[2] / MIO[44]
set_property iostandard "LVCMOS18" [get_ports "MIO[44]"]
set_property PACKAGE_PIN "F13" [get_ports "MIO[44]"]
set_property slew "slow" [get_ports "MIO[44]"]
set_property drive "8" [get_ports "MIO[44]"]
set_property pullup "TRUE" [get_ports "MIO[44]"]
set_property PIO_DIRECTION "BIDIR" [get_ports "MIO[44]"]
#  SD 0 / data[1] / MIO[43]
set_property iostandard "LVCMOS18" [get_ports "MIO[43]"]
set_property PACKAGE_PIN "A9" [get_ports "MIO[43]"]
set_property slew "slow" [get_ports "MIO[43]"]
set_property drive "8" [get_ports "MIO[43]"]
set_property pullup "TRUE" [get_ports "MIO[43]"]
set_property PIO_DIRECTION "BIDIR" [get_ports "MIO[43]"]
#  SD 0 / data[0] / MIO[42]
set_property iostandard "LVCMOS18" [get_ports "MIO[42]"]
set_property PACKAGE_PIN "E12" [get_ports "MIO[42]"]
set_property slew "slow" [get_ports "MIO[42]"]
set_property drive "8" [get_ports "MIO[42]"]
set_property pullup "TRUE" [get_ports "MIO[42]"]
set_property PIO_DIRECTION "BIDIR" [get_ports "MIO[42]"]
#  SD 0 / cmd / MIO[41]
set_property iostandard "LVCMOS18" [get_ports "MIO[41]"]
set_property PACKAGE_PIN "C17" [get_ports "MIO[41]"]
set_property slew "slow" [get_ports "MIO[41]"]
set_property drive "8" [get_ports "MIO[41]"]
set_property pullup "TRUE" [get_ports "MIO[41]"]
set_property PIO_DIRECTION "BIDIR" [get_ports "MIO[41]"]
#  SD 0 / clk / MIO[40]
set_property iostandard "LVCMOS18" [get_ports "MIO[40]"]
set_property PACKAGE_PIN "D14" [get_ports "MIO[40]"]
set_property slew "slow" [get_ports "MIO[40]"]
set_property drive "8" [get_ports "MIO[40]"]
set_property pullup "TRUE" [get_ports "MIO[40]"]
set_property PIO_DIRECTION "BIDIR" [get_ports "MIO[40]"]
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
set_property iostandard "LVCMOS33" [get_ports "MIO[9]"]
set_property PACKAGE_PIN "B5" [get_ports "MIO[9]"]
set_property slew "slow" [get_ports "MIO[9]"]
set_property drive "8" [get_ports "MIO[9]"]
set_property PIO_DIRECTION "BIDIR" [get_ports "MIO[9]"]
#  GPIO / gpio[8] / MIO[8]
set_property iostandard "LVCMOS33" [get_ports "MIO[8]"]
set_property PACKAGE_PIN "D5" [get_ports "MIO[8]"]
set_property slew "slow" [get_ports "MIO[8]"]
set_property drive "8" [get_ports "MIO[8]"]
set_property PIO_DIRECTION "OUTPUT" [get_ports "MIO[8]"]
#  GPIO / gpio[7] / MIO[7]
set_property iostandard "LVCMOS33" [get_ports "MIO[7]"]
set_property PACKAGE_PIN "D8" [get_ports "MIO[7]"]
set_property slew "slow" [get_ports "MIO[7]"]
set_property drive "8" [get_ports "MIO[7]"]
set_property PIO_DIRECTION "OUTPUT" [get_ports "MIO[7]"]
#  GPIO / gpio[6] / MIO[6]
set_property iostandard "LVCMOS33" [get_ports "MIO[6]"]
set_property PACKAGE_PIN "A5" [get_ports "MIO[6]"]
set_property slew "slow" [get_ports "MIO[6]"]
set_property drive "8" [get_ports "MIO[6]"]
set_property PIO_DIRECTION "BIDIR" [get_ports "MIO[6]"]
#  GPIO / gpio[5] / MIO[5]
set_property iostandard "LVCMOS33" [get_ports "MIO[5]"]
set_property PACKAGE_PIN "A6" [get_ports "MIO[5]"]
set_property slew "slow" [get_ports "MIO[5]"]
set_property drive "8" [get_ports "MIO[5]"]
set_property PIO_DIRECTION "BIDIR" [get_ports "MIO[5]"]
#  GPIO / gpio[4] / MIO[4]
set_property iostandard "LVCMOS33" [get_ports "MIO[4]"]
set_property PACKAGE_PIN "B7" [get_ports "MIO[4]"]
set_property slew "slow" [get_ports "MIO[4]"]
set_property drive "8" [get_ports "MIO[4]"]
set_property PIO_DIRECTION "BIDIR" [get_ports "MIO[4]"]
#  GPIO / gpio[3] / MIO[3]
set_property iostandard "LVCMOS33" [get_ports "MIO[3]"]
set_property PACKAGE_PIN "D6" [get_ports "MIO[3]"]
set_property slew "slow" [get_ports "MIO[3]"]
set_property drive "8" [get_ports "MIO[3]"]
set_property PIO_DIRECTION "BIDIR" [get_ports "MIO[3]"]
#  GPIO / gpio[2] / MIO[2]
set_property iostandard "LVCMOS33" [get_ports "MIO[2]"]
set_property PACKAGE_PIN "B8" [get_ports "MIO[2]"]
set_property slew "slow" [get_ports "MIO[2]"]
set_property drive "8" [get_ports "MIO[2]"]
set_property PIO_DIRECTION "BIDIR" [get_ports "MIO[2]"]
#  GPIO / gpio[1] / MIO[1]
set_property iostandard "LVCMOS33" [get_ports "MIO[1]"]
set_property PACKAGE_PIN "A7" [get_ports "MIO[1]"]
set_property slew "slow" [get_ports "MIO[1]"]
set_property drive "8" [get_ports "MIO[1]"]
set_property pullup "TRUE" [get_ports "MIO[1]"]
set_property PIO_DIRECTION "BIDIR" [get_ports "MIO[1]"]
#  GPIO / gpio[0] / MIO[0]
set_property iostandard "LVCMOS33" [get_ports "MIO[0]"]
set_property PACKAGE_PIN "E6" [get_ports "MIO[0]"]
set_property slew "slow" [get_ports "MIO[0]"]
set_property drive "8" [get_ports "MIO[0]"]
set_property PIO_DIRECTION "BIDIR" [get_ports "MIO[0]"]
set_property iostandard "SSTL15_T_DCI" [get_ports "DDR_VRP"]
set_property PACKAGE_PIN "H5" [get_ports "DDR_VRP"]
set_property slew "FAST" [get_ports "DDR_VRP"]
set_property PIO_DIRECTION "BIDIR" [get_ports "DDR_VRP"]
set_property iostandard "SSTL15_T_DCI" [get_ports "DDR_VRN"]
set_property PACKAGE_PIN "G5" [get_ports "DDR_VRN"]
set_property slew "FAST" [get_ports "DDR_VRN"]
set_property PIO_DIRECTION "BIDIR" [get_ports "DDR_VRN"]
set_property iostandard "SSTL15" [get_ports "DDR_WEB"]
set_property PACKAGE_PIN "M5" [get_ports "DDR_WEB"]
set_property slew "SLOW" [get_ports "DDR_WEB"]
set_property PIO_DIRECTION "OUTPUT" [get_ports "DDR_WEB"]
set_property iostandard "SSTL15" [get_ports "DDR_RAS_n"]
set_property PACKAGE_PIN "P4" [get_ports "DDR_RAS_n"]
set_property slew "SLOW" [get_ports "DDR_RAS_n"]
set_property PIO_DIRECTION "OUTPUT" [get_ports "DDR_RAS_n"]
set_property iostandard "SSTL15" [get_ports "DDR_ODT"]
set_property PACKAGE_PIN "N5" [get_ports "DDR_ODT"]
set_property slew "SLOW" [get_ports "DDR_ODT"]
set_property PIO_DIRECTION "OUTPUT" [get_ports "DDR_ODT"]
set_property iostandard "SSTL15" [get_ports "DDR_DRSTB"]
set_property PACKAGE_PIN "B4" [get_ports "DDR_DRSTB"]
set_property slew "FAST" [get_ports "DDR_DRSTB"]
set_property PIO_DIRECTION "BIDIR" [get_ports "DDR_DRSTB"]
set_property iostandard "DIFF_SSTL15_T_DCI" [get_ports "DDR_DQS[3]"]
set_property PACKAGE_PIN "W5" [get_ports "DDR_DQS[3]"]
set_property slew "FAST" [get_ports "DDR_DQS[3]"]
set_property PIO_DIRECTION "BIDIR" [get_ports "DDR_DQS[3]"]
set_property iostandard "DIFF_SSTL15_T_DCI" [get_ports "DDR_DQS[2]"]
set_property PACKAGE_PIN "R2" [get_ports "DDR_DQS[2]"]
set_property slew "FAST" [get_ports "DDR_DQS[2]"]
set_property PIO_DIRECTION "BIDIR" [get_ports "DDR_DQS[2]"]
set_property iostandard "DIFF_SSTL15_T_DCI" [get_ports "DDR_DQS[1]"]
set_property PACKAGE_PIN "G2" [get_ports "DDR_DQS[1]"]
set_property slew "FAST" [get_ports "DDR_DQS[1]"]
set_property PIO_DIRECTION "BIDIR" [get_ports "DDR_DQS[1]"]
set_property iostandard "DIFF_SSTL15_T_DCI" [get_ports "DDR_DQS[0]"]
set_property PACKAGE_PIN "C2" [get_ports "DDR_DQS[0]"]
set_property slew "FAST" [get_ports "DDR_DQS[0]"]
set_property PIO_DIRECTION "BIDIR" [get_ports "DDR_DQS[0]"]
set_property iostandard "DIFF_SSTL15_T_DCI" [get_ports "DDR_DQS_n[3]"]
set_property PACKAGE_PIN "W4" [get_ports "DDR_DQS_n[3]"]
set_property slew "FAST" [get_ports "DDR_DQS_n[3]"]
set_property PIO_DIRECTION "BIDIR" [get_ports "DDR_DQS_n[3]"]
set_property iostandard "DIFF_SSTL15_T_DCI" [get_ports "DDR_DQS_n[2]"]
set_property PACKAGE_PIN "T2" [get_ports "DDR_DQS_n[2]"]
set_property slew "FAST" [get_ports "DDR_DQS_n[2]"]
set_property PIO_DIRECTION "BIDIR" [get_ports "DDR_DQS_n[2]"]
set_property iostandard "DIFF_SSTL15_T_DCI" [get_ports "DDR_DQS_n[1]"]
set_property PACKAGE_PIN "F2" [get_ports "DDR_DQS_n[1]"]
set_property slew "FAST" [get_ports "DDR_DQS_n[1]"]
set_property PIO_DIRECTION "BIDIR" [get_ports "DDR_DQS_n[1]"]
set_property iostandard "DIFF_SSTL15_T_DCI" [get_ports "DDR_DQS_n[0]"]
set_property PACKAGE_PIN "B2" [get_ports "DDR_DQS_n[0]"]
set_property slew "FAST" [get_ports "DDR_DQS_n[0]"]
set_property PIO_DIRECTION "BIDIR" [get_ports "DDR_DQS_n[0]"]
set_property iostandard "SSTL15_T_DCI" [get_ports "DDR_DQ[9]"]
set_property PACKAGE_PIN "E3" [get_ports "DDR_DQ[9]"]
set_property slew "FAST" [get_ports "DDR_DQ[9]"]
set_property PIO_DIRECTION "BIDIR" [get_ports "DDR_DQ[9]"]
set_property iostandard "SSTL15_T_DCI" [get_ports "DDR_DQ[8]"]
set_property PACKAGE_PIN "E2" [get_ports "DDR_DQ[8]"]
set_property slew "FAST" [get_ports "DDR_DQ[8]"]
set_property PIO_DIRECTION "BIDIR" [get_ports "DDR_DQ[8]"]
set_property iostandard "SSTL15_T_DCI" [get_ports "DDR_DQ[7]"]
set_property PACKAGE_PIN "E1" [get_ports "DDR_DQ[7]"]
set_property slew "FAST" [get_ports "DDR_DQ[7]"]
set_property PIO_DIRECTION "BIDIR" [get_ports "DDR_DQ[7]"]
set_property iostandard "SSTL15_T_DCI" [get_ports "DDR_DQ[6]"]
set_property PACKAGE_PIN "C1" [get_ports "DDR_DQ[6]"]
set_property slew "FAST" [get_ports "DDR_DQ[6]"]
set_property PIO_DIRECTION "BIDIR" [get_ports "DDR_DQ[6]"]
set_property iostandard "SSTL15_T_DCI" [get_ports "DDR_DQ[5]"]
set_property PACKAGE_PIN "D1" [get_ports "DDR_DQ[5]"]
set_property slew "FAST" [get_ports "DDR_DQ[5]"]
set_property PIO_DIRECTION "BIDIR" [get_ports "DDR_DQ[5]"]
set_property iostandard "SSTL15_T_DCI" [get_ports "DDR_DQ[4]"]
set_property PACKAGE_PIN "D3" [get_ports "DDR_DQ[4]"]
set_property slew "FAST" [get_ports "DDR_DQ[4]"]
set_property PIO_DIRECTION "BIDIR" [get_ports "DDR_DQ[4]"]
set_property iostandard "SSTL15_T_DCI" [get_ports "DDR_DQ[3]"]
set_property PACKAGE_PIN "A4" [get_ports "DDR_DQ[3]"]
set_property slew "FAST" [get_ports "DDR_DQ[3]"]
set_property PIO_DIRECTION "BIDIR" [get_ports "DDR_DQ[3]"]
set_property iostandard "SSTL15_T_DCI" [get_ports "DDR_DQ[31]"]
set_property PACKAGE_PIN "V3" [get_ports "DDR_DQ[31]"]
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
set_property PIO_DIRECTION "BIDIR" [get_ports "DDR_DQ[15]"]
set_property iostandard "SSTL15_T_DCI" [get_ports "DDR_DQ[14]"]
set_property PACKAGE_PIN "H1" [get_ports "DDR_DQ[14]"]
set_property slew "FAST" [get_ports "DDR_DQ[14]"]
set_property PIO_DIRECTION "BIDIR" [get_ports "DDR_DQ[14]"]
set_property iostandard "SSTL15_T_DCI" [get_ports "DDR_DQ[13]"]
set_property PACKAGE_PIN "H2" [get_ports "DDR_DQ[13]"]
set_property slew "FAST" [get_ports "DDR_DQ[13]"]
set_property PIO_DIRECTION "BIDIR" [get_ports "DDR_DQ[13]"]
set_property iostandard "SSTL15_T_DCI" [get_ports "DDR_DQ[12]"]
set_property PACKAGE_PIN "J3" [get_ports "DDR_DQ[12]"]
set_property slew "FAST" [get_ports "DDR_DQ[12]"]
set_property PIO_DIRECTION "BIDIR" [get_ports "DDR_DQ[12]"]
set_property iostandard "SSTL15_T_DCI" [get_ports "DDR_DQ[11]"]
set_property PACKAGE_PIN "H3" [get_ports "DDR_DQ[11]"]
set_property slew "FAST" [get_ports "DDR_DQ[11]"]
set_property PIO_DIRECTION "BIDIR" [get_ports "DDR_DQ[11]"]
set_property iostandard "SSTL15_T_DCI" [get_ports "DDR_DQ[10]"]
set_property PACKAGE_PIN "G3" [get_ports "DDR_DQ[10]"]
set_property slew "FAST" [get_ports "DDR_DQ[10]"]
set_property PIO_DIRECTION "BIDIR" [get_ports "DDR_DQ[10]"]
set_property iostandard "SSTL15_T_DCI" [get_ports "DDR_DQ[0]"]
set_property PACKAGE_PIN "C3" [get_ports "DDR_DQ[0]"]
set_property slew "FAST" [get_ports "DDR_DQ[0]"]
set_property PIO_DIRECTION "BIDIR" [get_ports "DDR_DQ[0]"]
set_property iostandard "SSTL15_T_DCI" [get_ports "DDR_DM[3]"]
set_property PACKAGE_PIN "Y1" [get_ports "DDR_DM[3]"]
set_property slew "FAST" [get_ports "DDR_DM[3]"]
set_property PIO_DIRECTION "BIDIR" [get_ports "DDR_DM[3]"]
set_property iostandard "SSTL15_T_DCI" [get_ports "DDR_DM[2]"]
set_property PACKAGE_PIN "T1" [get_ports "DDR_DM[2]"]
set_property slew "FAST" [get_ports "DDR_DM[2]"]
set_property PIO_DIRECTION "BIDIR" [get_ports "DDR_DM[2]"]
set_property iostandard "SSTL15_T_DCI" [get_ports "DDR_DM[1]"]
set_property PACKAGE_PIN "F1" [get_ports "DDR_DM[1]"]
set_property slew "FAST" [get_ports "DDR_DM[1]"]
set_property PIO_DIRECTION "BIDIR" [get_ports "DDR_DM[1]"]
set_property iostandard "SSTL15_T_DCI" [get_ports "DDR_DM[0]"]
set_property PACKAGE_PIN "A1" [get_ports "DDR_DM[0]"]
set_property slew "FAST" [get_ports "DDR_DM[0]"]
set_property PIO_DIRECTION "BIDIR" [get_ports "DDR_DM[0]"]
set_property iostandard "SSTL15" [get_ports "DDR_CS_n"]
set_property PACKAGE_PIN "N1" [get_ports "DDR_CS_n"]
set_property slew "SLOW" [get_ports "DDR_CS_n"]
set_property PIO_DIRECTION "OUTPUT" [get_ports "DDR_CS_n"]
set_property iostandard "SSTL15" [get_ports "DDR_CKE"]
set_property PACKAGE_PIN "N3" [get_ports "DDR_CKE"]
set_property slew "SLOW" [get_ports "DDR_CKE"]
set_property PIO_DIRECTION "OUTPUT" [get_ports "DDR_CKE"]
set_property iostandard "DIFF_SSTL15" [get_ports "DDR_Clk"]
set_property PACKAGE_PIN "L2" [get_ports "DDR_Clk"]
set_property slew "FAST" [get_ports "DDR_Clk"]
set_property PIO_DIRECTION "INPUT" [get_ports "DDR_Clk"]
set_property iostandard "DIFF_SSTL15" [get_ports "DDR_Clk_n"]
set_property PACKAGE_PIN "M2" [get_ports "DDR_Clk_n"]
set_property slew "FAST" [get_ports "DDR_Clk_n"]
set_property PIO_DIRECTION "INPUT" [get_ports "DDR_Clk_n"]
set_property iostandard "SSTL15" [get_ports "DDR_CAS_n"]
set_property PACKAGE_PIN "P5" [get_ports "DDR_CAS_n"]
set_property slew "SLOW" [get_ports "DDR_CAS_n"]
set_property PIO_DIRECTION "OUTPUT" [get_ports "DDR_CAS_n"]
set_property iostandard "SSTL15" [get_ports "DDR_BankAddr[2]"]
set_property PACKAGE_PIN "J5" [get_ports "DDR_BankAddr[2]"]
set_property slew "SLOW" [get_ports "DDR_BankAddr[2]"]
set_property PIO_DIRECTION "OUTPUT" [get_ports "DDR_BankAddr[2]"]
set_property iostandard "SSTL15" [get_ports "DDR_BankAddr[1]"]
set_property PACKAGE_PIN "R4" [get_ports "DDR_BankAddr[1]"]
set_property slew "SLOW" [get_ports "DDR_BankAddr[1]"]
set_property PIO_DIRECTION "OUTPUT" [get_ports "DDR_BankAddr[1]"]
set_property iostandard "SSTL15" [get_ports "DDR_BankAddr[0]"]
set_property PACKAGE_PIN "L5" [get_ports "DDR_BankAddr[0]"]
set_property slew "SLOW" [get_ports "DDR_BankAddr[0]"]
set_property PIO_DIRECTION "OUTPUT" [get_ports "DDR_BankAddr[0]"]
set_property iostandard "SSTL15" [get_ports "DDR_Addr[9]"]
set_property PACKAGE_PIN "J4" [get_ports "DDR_Addr[9]"]
set_property slew "SLOW" [get_ports "DDR_Addr[9]"]
set_property PIO_DIRECTION "OUTPUT" [get_ports "DDR_Addr[9]"]
set_property iostandard "SSTL15" [get_ports "DDR_Addr[8]"]
set_property PACKAGE_PIN "K1" [get_ports "DDR_Addr[8]"]
set_property slew "SLOW" [get_ports "DDR_Addr[8]"]
set_property PIO_DIRECTION "OUTPUT" [get_ports "DDR_Addr[8]"]
set_property iostandard "SSTL15" [get_ports "DDR_Addr[7]"]
set_property PACKAGE_PIN "K4" [get_ports "DDR_Addr[7]"]
set_property slew "SLOW" [get_ports "DDR_Addr[7]"]
set_property PIO_DIRECTION "OUTPUT" [get_ports "DDR_Addr[7]"]
set_property iostandard "SSTL15" [get_ports "DDR_Addr[6]"]
set_property PACKAGE_PIN "L4" [get_ports "DDR_Addr[6]"]
set_property slew "SLOW" [get_ports "DDR_Addr[6]"]
set_property PIO_DIRECTION "OUTPUT" [get_ports "DDR_Addr[6]"]
set_property iostandard "SSTL15" [get_ports "DDR_Addr[5]"]
set_property PACKAGE_PIN "L1" [get_ports "DDR_Addr[5]"]
set_property slew "SLOW" [get_ports "DDR_Addr[5]"]
set_property PIO_DIRECTION "OUTPUT" [get_ports "DDR_Addr[5]"]
set_property iostandard "SSTL15" [get_ports "DDR_Addr[4]"]
set_property PACKAGE_PIN "M4" [get_ports "DDR_Addr[4]"]
set_property slew "SLOW" [get_ports "DDR_Addr[4]"]
set_property PIO_DIRECTION "OUTPUT" [get_ports "DDR_Addr[4]"]
set_property iostandard "SSTL15" [get_ports "DDR_Addr[3]"]
set_property PACKAGE_PIN "K3" [get_ports "DDR_Addr[3]"]
set_property slew "SLOW" [get_ports "DDR_Addr[3]"]
set_property PIO_DIRECTION "OUTPUT" [get_ports "DDR_Addr[3]"]
set_property iostandard "SSTL15" [get_ports "DDR_Addr[2]"]
set_property PACKAGE_PIN "M3" [get_ports "DDR_Addr[2]"]
set_property slew "SLOW" [get_ports "DDR_Addr[2]"]
set_property PIO_DIRECTION "OUTPUT" [get_ports "DDR_Addr[2]"]
set_property iostandard "SSTL15" [get_ports "DDR_Addr[1]"]
set_property PACKAGE_PIN "K2" [get_ports "DDR_Addr[1]"]
set_property slew "SLOW" [get_ports "DDR_Addr[1]"]
set_property PIO_DIRECTION "OUTPUT" [get_ports "DDR_Addr[1]"]
set_property iostandard "SSTL15" [get_ports "DDR_Addr[14]"]
set_property PACKAGE_PIN "F4" [get_ports "DDR_Addr[14]"]
set_property slew "SLOW" [get_ports "DDR_Addr[14]"]
set_property PIO_DIRECTION "OUTPUT" [get_ports "DDR_Addr[14]"]
set_property iostandard "SSTL15" [get_ports "DDR_Addr[13]"]
set_property PACKAGE_PIN "D4" [get_ports "DDR_Addr[13]"]
set_property slew "SLOW" [get_ports "DDR_Addr[13]"]
set_property PIO_DIRECTION "OUTPUT" [get_ports "DDR_Addr[13]"]
set_property iostandard "SSTL15" [get_ports "DDR_Addr[12]"]
set_property PACKAGE_PIN "E4" [get_ports "DDR_Addr[12]"]
set_property slew "SLOW" [get_ports "DDR_Addr[12]"]
set_property PIO_DIRECTION "OUTPUT" [get_ports "DDR_Addr[12]"]
set_property iostandard "SSTL15" [get_ports "DDR_Addr[11]"]
set_property PACKAGE_PIN "G4" [get_ports "DDR_Addr[11]"]
set_property slew "SLOW" [get_ports "DDR_Addr[11]"]
set_property PIO_DIRECTION "OUTPUT" [get_ports "DDR_Addr[11]"]
set_property iostandard "SSTL15" [get_ports "DDR_Addr[10]"]
set_property PACKAGE_PIN "F5" [get_ports "DDR_Addr[10]"]
set_property slew "SLOW" [get_ports "DDR_Addr[10]"]
set_property PIO_DIRECTION "OUTPUT" [get_ports "DDR_Addr[10]"]
set_property iostandard "SSTL15" [get_ports "DDR_Addr[0]"]
set_property PACKAGE_PIN "N2" [get_ports "DDR_Addr[0]"]
set_property slew "SLOW" [get_ports "DDR_Addr[0]"]
set_property PIO_DIRECTION "OUTPUT" [get_ports "DDR_Addr[0]"]
set_property iostandard "LVCMOS33" [get_ports "PS_PORB"]
set_property PACKAGE_PIN "C7" [get_ports "PS_PORB"]
set_property slew "fast" [get_ports "PS_PORB"]
set_property iostandard "LVCMOS18" [get_ports "PS_SRSTB"]
set_property PACKAGE_PIN "B10" [get_ports "PS_SRSTB"]
set_property slew "fast" [get_ports "PS_SRSTB"]
set_property iostandard "LVCMOS33" [get_ports "PS_CLK"]
set_property PACKAGE_PIN "E7" [get_ports "PS_CLK"]
set_property slew "fast" [get_ports "PS_CLK"]
