shanshe/Z3660/z3660-drivers/usb/z3660_usb_device.c

/*
 * SPDX-License-Identifier: GPL-3.0-or-later
 *
 * ZZ9000 Poseidon USB Hardware Driver (zzusbhw.device)
 *
 * Copyright (C) 2026 Dimitris Panokostas <midwan@gmail.com>
 *
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
 * Z3660 Poseidon USB Hardware Driver (z3660_usb.device) based on ZZ9000 work by MiDWaN
 * 
 */

#include <exec/resident.h>
#include <exec/errors.h>
#include <exec/memory.h>
#include <exec/lists.h>
#include <exec/tasks.h>
#include <exec/io.h>
#include <exec/execbase.h>

#include <libraries/expansion.h>

#include <devices/timer.h>
#include <devices/usbhardware.h>

#include <proto/exec.h>
#include <proto/expansion.h>

#include <stdint.h>
#include <string.h>
#include <stdio.h>
#include <stdarg.h>

#include "z3660_usb.h"
#include "z3660_usb_str.h"

struct ExecBase* SysBase;

#define STR(s) #s
#define XSTR(s) STR(s)

/*
 * lib_IdString format matches the canonical Amiga pattern
 *   "name version.revision (date) description"
 * so tools like `version` and Poseidon's internal identification
 * routines parse it consistently.
 */
#define DEVICE_ID_STRING DEVICE_NAME " " XSTR(DEVICE_VERSION) "." XSTR(DEVICE_REVISION) \
    " (17.05.2026) Poseidon USB driver for Z3660 " \
    "(C) Copyright 2026 Dimitris Panokostas"

#define USB_DATA_ADDRESS 0x07F00000

/* USB request constants (from usb.h) */
#define USR_GET_STATUS        0x00
#define USR_CLEAR_FEATURE     0x01
#define USR_SET_FEATURE       0x03
#define USR_GET_DESCRIPTOR    0x06
#define USR_SET_ADDRESS       0x05
#define USR_GET_CONFIGURATION 0x08
#define USR_SET_CONFIGURATION 0x09

#define URTF_IN               0x80
#define URTF_STANDARD         0x00
#define URTF_CLASS            0x20
#define URTF_DEVICE           0x00
#define URTF_OTHER            0x03

#define UDT_DEVICE            0x01
#define UDT_CONFIGURATION     0x02
#define UDT_STRING            0x03
#define UDT_HUB               0x29

#define UPSF_PORT_CONNECTION  0x0100
#define UPSF_PORT_ENABLE      0x0200
#define UPSF_PORT_SUSPEND     0x0400
#define UPSF_PORT_OVER_CURRENT 0x0800
#define UPSF_PORT_RESET       0x1000
#define UPSF_PORT_POWER       0x0001
#define UPSF_PORT_LOW_SPEED   0x0002
#define UPSF_PORT_HIGH_SPEED  0x0004

#define UFS_PORT_POWER        0x08
#define UFS_PORT_RESET        0x04
#define UFS_PORT_ENABLE       0x01
#define UFS_PORT_SUSPEND      0x02
#define UFS_C_PORT_CONNECTION 0x10
#define UFS_C_PORT_ENABLE     0x11
#define UFS_C_PORT_SUSPEND    0x12
#define UFS_C_PORT_OVER_CURRENT 0x13
#define UFS_C_PORT_RESET      0x14

/* wPortChange bits use same UPSF_ layout as wPortStatus (byte-swapped USB spec). */
#define UPSF_C_PORT_CONNECTION 0x0100
#define UPSF_C_PORT_ENABLE     0x0200
#define UPSF_C_PORT_SUSPEND    0x0400
#define UPSF_C_PORT_OVER_CURRENT 0x0800
#define UPSF_C_PORT_RESET      0x1000

#define SWAP16(x) ((uint16_t)((uint16_t)(x) << 8) | ((uint16_t)(x) >> 8))
#define ZZ_RH_POLL_DELAY_TICKS 10
#define ZZ_INT_IDLE_REPLY_POLLS 10
#define ZZ_INT_PENDING_SLOTS 32
#define ZZ_ABORTED_REPLY_SLOTS (ZZ_INT_PENDING_SLOTS + ZZ_NUM_PORTS + 16)
#ifndef UHCF_USB20
#define UHCF_USB20 (1UL << 0)
#endif
#ifndef UHA_Capabilities
#define UHA_Capabilities (UHA_Dummy + 0x21)
#endif
#ifndef UHA_RootHubAddr
#define UHA_RootHubAddr (UHA_Dummy + 0x22)
#endif

static struct ZZUSBBase *PollBase;

/*
 * Saved seglist for expunge. Stored as a static rather than a struct
 * member because struct ZZUSBBase has a frozen v2.0.0 layout — the
 * hand-written AddTask inline asm in begin_io and the firmware-side
 * tooling expect specific field offsets, and inserting a member
 * shifts everything after it. Single-instance driver, so a static
 * is functionally equivalent.
 */
static uint8_t *DeviceSegList;
static struct IOUsbHWReq *RootHubIntPending[ZZ_NUM_PORTS];
static uint8_t RootHubPollDelay[ZZ_NUM_PORTS];

struct ZZIntPendingSlot {
    struct ZZUSBUnit *unit;
    struct IOUsbHWReq *ior;
    uint8_t idle_polls;
};

static struct ZZIntPendingSlot IntPendingSlots[ZZ_INT_PENDING_SLOTS];

static uint16_t request_speed(struct ZZUSBUnit *unit, struct IOUsbHWReq *ior);
static int write_tag_ulong(struct TagItem *tag, ULONG value);
static int write_tag_str(struct TagItem *tag, const char *value);

static void hotplug_poll_task(void);

asm("romtag:                                \n"
    "       dc.w    "XSTR(RTC_MATCHWORD)"   \n"
    "       dc.l    romtag                  \n"
    "       dc.l    endcode                 \n"
    "       dc.b    "XSTR(RTF_AUTOINIT)"    \n"
    "       dc.b    "XSTR(DEVICE_VERSION)"  \n"
    "       dc.b    "XSTR(NT_DEVICE)"       \n"
    "       dc.b    0                       \n"
    "       dc.l    _device_name            \n"
    "       dc.l    _device_id_string       \n"
    "       dc.l    _auto_init_tables       \n"
    "endcode:                               \n");

int __attribute__((no_reorder)) _start()
{
    return -1;
}
void _exit (int32_t status)
{
    (void) status;
    while (1)
    {}
}
const char device_name[] = DEVICE_NAME;
const char device_id_string[] = DEVICE_ID_STRING;

/*
 * AmigaOS `version DEVS:USBHardware/z3660_usb.device FILE` scans the
 * binary for a `$VER:` tag and prints the version/revision that
 * follows. Without the tag, `version` falls back to a generic "v1.0"
 * which defeats
 * field verification of driver deployment. Include a (date) after
 * the version number per standard Amiga $VER convention — some
 * tools require it to parse the version correctly.
 */
static const char __attribute__((used)) version_tag[] =
    "$VER: " DEVICE_NAME " " XSTR(DEVICE_VERSION) "." XSTR(DEVICE_REVISION)
    " (17.05.2026) Poseidon USB driver for Z3660 "
    "(C) Copyright 2026 Dimitris Panokostas";

typedef char ZZUSBCommand_size_must_match_protocol[
    (sizeof(struct ZZUSBCommand) == ZZUSB_CMD_SIZE) ? 1 : -1];

static struct ExecBase *get_sysbase(void)
{
/*
    struct ExecBase *sysbase;
    __asm volatile ("move.l 4.w,%0" : "=r"(sysbase));
    return sysbase;
*/
// Es esto equivalente?? por qué usar ensamblador??
    return *(struct ExecBase **)4UL;
}

/* Push a NUL-terminated string to the Z3660 serial debug channel. */
static void dstr(void* regs, const char *fmt, ...)
{
    
    static char message_buffer[256];  /* Static to avoid stack issues during crashes */
    va_list args;

    va_start(args, fmt);
    vsprintf(message_buffer, fmt, args);
    va_end(args);
    static int initialized = 0;
    if(!initialized) {
        // Send an initial newline to flush the channel and make the output more readable
        *((volatile uint32_t*)((uint8_t*)regs + REG_ZZ_DEBUG)) = 0xDB600001;  /* Magic marker for ARM */
        initialized = 1;
    }
    static char arm_message[280];  /* Static to avoid stack issues */
    sprintf(arm_message, "[AMG] %s", message_buffer);

    /* CACHE COHERENCY: Ensure data is visible to ARM before sending pointer */
    /* This cleans the CPU cache line containing our message to main memory */
    /* so the ARM can read the correct data from its cache-coherent view */
    {
        ULONG msg_len = strlen(arm_message) + 1;
        CachePreDMA((APTR)arm_message, &msg_len, 0);
        *((volatile uint32_t*)((uint8_t*)regs + REG_ZZ_DEBUG)) = (ULONG)arm_message;
        CachePostDMA((APTR)arm_message, &msg_len, 0);
    }
}

static void trace_port_state(struct ZZUSBUnit *unit, char *tag)
{
    void *regs = unit->zz_Registers;

    dstr(regs, "[z3660_usb] %s ps=%04X ch=%04X sp=%02X pr=%d dead=%d\n",
                  tag, unit->zz_PortStatus, unit->zz_PortChange,
                  unit->zz_Speed, unit->zz_PortPresent ? 1 : 0,
                  unit->zz_PortDead ? 1 : 0);
}

static void trace_port_state_status(struct ZZUSBUnit *unit,
                                    char *tag,
                                    uint16_t status,
                                    uint16_t speed)
{
    void *regs = unit->zz_Registers;

    dstr(regs, "[z3660_usb] %s rc=%04X fwsp=%02X ps=%04X ch=%04X\n",
                  tag, status, speed, unit->zz_PortStatus, unit->zz_PortChange);
}

static void trace_control_status(struct ZZUSBUnit *unit,
                                 char *tag,
                                 struct IOUsbHWReq *ior,
                                 uint16_t status)
{
    void *regs = unit->zz_Registers;

    dstr(regs, "[z3660_usb] %s st=%04X dev=%02X req=%02X/%02X fl=%04X sp=%02X split=%02X hub=%02X port=%02X\n",
                  tag, status, ior->iouh_DevAddr, ior->iouh_SetupData.bmRequestType,
                  ior->iouh_SetupData.bRequest, ior->iouh_Flags, request_speed(unit, ior),
                  (ior->iouh_Flags & UHFF_SPLITTRANS) ? 1 : 0, ior->iouh_SplitHubAddr,
                  ior->iouh_SplitHubPort);
}

static void __attribute__((unused)) trace_int_status(struct ZZUSBUnit *unit,
                                                     char *tag,
                                                     struct IOUsbHWReq *ior)
{
    void *regs = unit->zz_Registers;

    dstr(regs, "[z3660_usb] %s dev=%02X ep=%02X len=%04X fl=%04X split=%02X\n",
                  tag, ior->iouh_DevAddr, ior->iouh_Endpoint, ior->iouh_Length,
                  ior->iouh_Flags, (ior->iouh_Flags & UHFF_SPLITTRANS) ? 1 : 0);
}

static void trace_hub_int_data(struct ZZUSBUnit *unit,
                               struct IOUsbHWReq *ior,
                               uint32_t actual,
                               volatile uint8_t *data)
{
    void *regs = unit->zz_Registers;

    if (ior->iouh_Dir != UHDIR_IN || ior->iouh_Length > 2 || actual == 0)
        return;
    for (uint32_t i = 0; i < actual && i < 2; i++) {
        if (data[i] != 0)
            goto nonzero;
    }
    return;

nonzero:
    dstr(regs, "[z3660_usb] INT_DATA dev=%02X ep=%02X act=%04X d=%02X%02X\n",
                 ior->iouh_DevAddr, ior->iouh_Endpoint, actual, data[0], actual>0?data[1]:0);
}

static int is_hid_set_idle(struct IOUsbHWReq *ior)
{
    return ior->iouh_SetupData.bmRequestType == 0x21 &&
           ior->iouh_SetupData.bRequest == 0x0a &&
           ior->iouh_Length == 0;
}

/*
 * Alignment-safe memcpy. Replaces AmigaOS CopyMem, which has been
 * observed to silently no-op on this toolchain with GCC 15.2 when
 * either src or dst is at an odd address — Poseidon's iouh_Data
 * can legitimately arrive at odd alignments.
 *
 * The byte-loop at the bottom is the safe universal path. When
 * src and dst share 4-byte or 2-byte alignment we upgrade to
 * MOVE.L / MOVE.W copies. The fast path was proven correct
 * during mass-storage bring-up: FAT32 reads work end-to-end with
 * the fast path active, and the byte-level data verification
 * showed identical contents across repeat reads.
 */
static void safe_copy(const void *src, void *dst, uint32_t n)
{
    const uint8_t *s = (const uint8_t *)src;
    uint8_t *d = (uint8_t *)dst;
//    ULONG len = n;
//    CachePreDMA((APTR)dst, &len, 0);

    /* Long-aligned fast path — both divisible by 4.
     * Use exec's CopyMemQuick (movem.l-based, ~10× faster than the C
     * long-per-move loop). Requires 4-byte-aligned src+dst and size
     * multiple of 4, which this branch already guarantees. */
    if (n >= 4 && ((((uintptr_t)s | (uintptr_t)d) & 3) == 0)) {
        uint32_t bulk = n & ~3U;
        CopyMemQuick((APTR)s, (APTR)d, bulk);
        s += bulk;
        d += bulk;
        n &= 3;
    }
    /* Word-aligned fast path — both divisible by 2. */
    else if (n >= 2 && ((((uintptr_t)s | (uintptr_t)d) & 1) == 0)) {
        const uint16_t *ws = (const uint16_t *)s;
        uint16_t *wd = (uint16_t *)d;
        uint32_t words = n >> 1;
        while (words--) *wd++ = *ws++;
        s = (const uint8_t *)ws;
        d = (uint8_t *)wd;
        n &= 1;
    }

    /* Byte tail, or unaligned-all-the-way. */
    while (n--) *d++ = *s++;

//    CachePostDMA((APTR)dst, &len, 0);

}

static void safe_zero(void *dst, uint32_t n)
{
    uint8_t *d = (uint8_t *)dst;
    while (n--) *d++ = 0;
}

static uint16_t int_endpoint_key(struct IOUsbHWReq *ior)
{
    return ior->iouh_Endpoint & 0x0f;
}

static int int_slot_matches(struct ZZIntPendingSlot *slot,
                            struct ZZUSBUnit *unit,
                            struct IOUsbHWReq *ior)
{
    struct IOUsbHWReq *pending = slot->ior;

    return pending &&
        slot->unit == unit &&
        pending->iouh_DevAddr == ior->iouh_DevAddr &&
        int_endpoint_key(pending) == int_endpoint_key(ior) &&
        pending->iouh_Dir == ior->iouh_Dir;
}

static void clear_int_slot(struct ZZIntPendingSlot *slot)
{
    slot->unit = NULL;
    slot->ior = NULL;
    slot->idle_polls = 0;
}

static void reset_int_slots(void)
{
    for (int i = 0; i < ZZ_INT_PENDING_SLOTS; i++)
        clear_int_slot(&IntPendingSlots[i]);
}

static struct ZZIntPendingSlot *find_int_slot_for_ior(struct IOUsbHWReq *ior)
{
    for (int i = 0; i < ZZ_INT_PENDING_SLOTS; i++) {
        if (IntPendingSlots[i].ior == ior)
            return &IntPendingSlots[i];
    }
    return NULL;
}

static int queue_int_ior(struct ZZUSBUnit *unit,
                         struct IOUsbHWReq *ior,
                         struct IOUsbHWReq **replaced)
{
    struct ZZIntPendingSlot *free_slot = NULL;

    if (replaced)
        *replaced = NULL;

    for (int i = 0; i < ZZ_INT_PENDING_SLOTS; i++) {
        struct ZZIntPendingSlot *slot = &IntPendingSlots[i];
        if (int_slot_matches(slot, unit, ior)) {
            if (slot->ior && slot->ior != ior) {
                if (replaced)
                    *replaced = slot->ior;
                slot->ior->iouh_Actual = 0;
                slot->ior->iouh_Req.io_Error = IOERR_ABORTED;
            }
            slot->unit = unit;
            slot->ior = ior;
            slot->idle_polls = 0;
            return 1;
        }
        if (!slot->ior && !free_slot)
            free_slot = slot;
    }

    if (!free_slot)
        return 0;

    free_slot->unit = unit;
    free_slot->ior = ior;
    free_slot->idle_polls = 0;
    return 1;
}

static int int_pending_for_unit(struct ZZUSBUnit *unit)
{
    for (int i = 0; i < ZZ_INT_PENDING_SLOTS; i++) {
        if (IntPendingSlots[i].ior && IntPendingSlots[i].unit == unit)
            return 1;
    }
    return 0;
}

static int is_addr0_ep0(struct IOUsbHWReq *ior)
{
    return ior->iouh_DevAddr == 0 && ior->iouh_Endpoint == 0;
}

static int is_direct_root_request(struct ZZUSBUnit *unit)
{
    /*
     * Address zero is also used while enumerating devices behind an
     * external high-speed hub. In that case Poseidon supplies valid split
     * information and the root port itself remains high-speed. Only force
     * root-port handling when the physical root port is already known to be
     * FS/LS; this applies to every endpoint, not just address-zero EP0.
     */
    return unit->zz_PortPresent &&
           unit->zz_Speed != ZZUSB_SPEED_HIGH;
}

static int is_direct_root_addr0(struct ZZUSBUnit *unit, struct IOUsbHWReq *ior)
{
    return is_addr0_ep0(ior) && is_direct_root_request(unit);
}

static int is_addr0_get_device_desc(struct IOUsbHWReq *ior)
{
    return is_addr0_ep0(ior) &&
           ior->iouh_SetupData.bmRequestType == 0x80 &&
           ior->iouh_SetupData.bRequest == 0x06 &&
           SWAP16(ior->iouh_SetupData.wValue) == 0x0100;
}

static uint16_t request_speed(struct ZZUSBUnit *unit, struct IOUsbHWReq *ior)
{
    if (is_direct_root_request(unit))
        return unit->zz_Speed;
    if (ior->iouh_Flags & UHFF_SPLITTRANS) {
        return (ior->iouh_Flags & UHFF_LOWSPEED)
               ? ZZUSB_SPEED_LOW : ZZUSB_SPEED_FULL;
    }
    if (ior->iouh_Flags & UHFF_LOWSPEED)
        return ZZUSB_SPEED_LOW;
    if (ior->iouh_Flags & UHFF_HIGHSPEED)
        return ZZUSB_SPEED_HIGH;
    return unit->zz_Speed;
}

static void fill_split_fields(struct ZZUSBCommand *cmd,
                              struct ZZUSBUnit *unit,
                              struct IOUsbHWReq *ior)
{
    if (is_direct_root_request(unit))
        return;

    if ((ior->iouh_Flags & UHFF_SPLITTRANS) &&
        ior->iouh_SplitHubAddr != 0 &&
        ior->iouh_SplitHubPort != 0) {
        cmd->split_hub_addr = ior->iouh_SplitHubAddr;
        cmd->split_hub_port = ior->iouh_SplitHubPort;
        cmd->flags |= ZZUSB_FLAG_SPLIT;
    }
}

static void fill_root_reset_hint(struct ZZUSBCommand *cmd,
                                 struct ZZUSBUnit *unit)
{
    cmd->speed = unit->zz_Speed;
    /*
     * Full-speed and high-speed devices both present J before reset. Forcing
     * PFSC on a full-speed pre-reset hint prevents high-speed chirp, so only
     * force the FS/LS reset path for a confirmed low-speed root attach.
     */
    if (unit->zz_PortPresent && unit->zz_Speed == ZZUSB_SPEED_LOW)
        cmd->flags |= ZZUSB_FLAG_RESET_FSLS;
}

static void mark_direct_low_speed_unsupported(struct ZZUSBUnit *unit,
                                              char *tag)
{
    unit->zz_PortDead = TRUE;
    unit->zz_PortPresent = FALSE;
    unit->zz_Speed = ZZUSB_SPEED_LOW;
    unit->zz_PortStatus = UPSF_PORT_POWER;
    unit->zz_PortChange = UPSF_C_PORT_CONNECTION;
    unit->zz_BulkErrCount = 0;
    trace_port_state(unit, tag);
}

static int is_zero_report(volatile uint8_t *buf, uint32_t len)
{
    while (len--) {
        if (*buf++ != 0)
            return 0;
    }
    return 1;
}

static int send_usb_cmd(volatile uint8_t *base, struct ZZUSBCommand *cmd,
                        void *data_out, uint32_t data_out_len)
{
    volatile struct ZZUSBCommand *result =
        (volatile struct ZZUSBCommand*)(base + USB_DATA_ADDRESS);
    volatile int delay;

    cmd->status = ZZUSB_STATUS_PENDING;
    /*
     * Use safe_copy for everything. AmigaOS CopyMem has been observed
     * to silently no-op on this toolchain when either src or dst is
     * at an odd address. Poseidon can hand us iouh_Data buffers at
     * arbitrary alignments, so play it safe across the board.
     */
    safe_copy(cmd, (void*)(base + USB_DATA_ADDRESS), ZZUSB_CMD_SIZE);

    if (data_out && data_out_len > 0 && data_out_len <= ZZUSB_MAX_XFER) {
        safe_copy(data_out, (void*)(base + USB_DATA_ADDRESS + ZZUSB_DATA_OFFSET), data_out_len);
    }

//    CacheClearU();

//    dstr(base,"Sending command %s\n",zz_usb_cmd_str[cmd->cmd]);
     *((volatile uint32_t*)(base + REG_ZZ_USB_PROXY_CMD)) = cmd->cmd;

    /*
     * Tight busy-wait poll for firmware response.
     *
     * Prior revisions used an inner delay loop of 1000 empty
     * iterations between status reads (~200us on 68020 per check).
     * For a typical 1-5ms bulk transfer that wastes dozens of
     * 200us windows, adding milliseconds of per-round-trip
     * overhead that compounds over every bulk chunk. Benchmark
     * showed this as the dominant throughput bottleneck vs the
     * Deneb reference.
     *
     * Replaced with a short inner delay (~10us) so the poll rate
     * matches the firmware response timing without hammering the
     * Zorro bus. Outer loop still bounded by cmd->timeout_ms so
     * a wedged firmware releases zz_Lock within the specified
     * deadline.
     *
     * Inner delay ~10us + status-read overhead ~5us = ~15us per
     * iteration. Outer count = timeout_ms * 66 gives us roughly
     * the right wall-clock bound. timeout_ms=0 falls back to
     * ~3 sec (200,000 iterations).
     */
    {
        uint32_t outer_limit = cmd->timeout_ms
                               ? (uint32_t)cmd->timeout_ms * 66
                               : 200000;
        uint32_t timeout = outer_limit;
        while (timeout-- > 0) {
            if (result->status != ZZUSB_STATUS_PENDING) break;
            delay = 50;        /* ~10us on 68020 */
            while (delay--);
        }
    }
//    dstr(base,"Received status %s\n",zz_usb_status_str[result->status]);
    
    CacheClearU();

    if (result->status == ZZUSB_STATUS_PENDING) {
        dstr((void*)base, "[z3660_usb] CMD_TIMEOUT cmd=%02X dev=%02X ep=%02X wait=%04X\n",
                             cmd->cmd, cmd->dev_addr, cmd->endpoint, cmd->timeout_ms);
    }

    return result->status;
}

static void ensure_poll_task(struct ZZUSBBase *ZZBase)
{
    if (ZZBase->zz_PollTask)
        return;

    Forbid();
    if (!ZZBase->zz_PollTask) {
        struct Task *poll = &ZZBase->zz_PollTaskStorage;

        uint8_t *tp = (uint8_t*)poll;
        for (unsigned i = 0; i < sizeof(struct Task); i++)
            tp[i] = 0;

        poll->tc_Node.ln_Type = NT_TASK;
        poll->tc_Node.ln_Pri  = -1;
        poll->tc_Node.ln_Name = (char *)"z3660_usb.poll";

        poll->tc_SPLower = (APTR)&ZZBase->zz_PollStack[0];
        poll->tc_SPUpper = (APTR)&ZZBase->zz_PollStack[1024];
        poll->tc_SPReg   = (APTR)&ZZBase->zz_PollStack[1024];

        poll->tc_MemEntry.lh_Head =
            (struct Node *)&poll->tc_MemEntry.lh_Tail;
        poll->tc_MemEntry.lh_Tail = NULL;
        poll->tc_MemEntry.lh_TailPred =
            (struct Node *)&poll->tc_MemEntry.lh_Head;
        poll->tc_MemEntry.lh_Type = NT_MEMORY;

        /*
         * Reserve system signals 0..15 so AllocSignal(-1) in the task
         * body returns a user bit (16..31), and initialize nest counts
         * to the normal task state for exec variants that do not fix
         * them up inside AddTask().
         */
        poll->tc_SigAlloc  = 0xFFFF;
        poll->tc_IDNestCnt = -1;
        poll->tc_TDNestCnt = -1;

        PollBase = ZZBase;
        ZZBase->zz_PollTask = poll;

        {
/*
            struct Task *const _t = poll;
            const APTR _ipc = (APTR)hotplug_poll_task;
            const APTR _fpc = NULL;
            register struct Task *_a1 __asm("a1") = _t;
            register APTR _a2 __asm("a2") = _ipc;
            register APTR _a3 __asm("a3") = _fpc;
            register void *_a6 __asm("a6") = SysBase;
            __asm volatile ("jsr a6@(-0x11a:W)"
                : "+r"(_a1), "+r"(_a2), "+r"(_a3)
                : "r"(_a6)
                : "d0","d1","a0","cc","memory");
*/
// Esto es sustituible por esto?
            struct Task *poll = &ZZBase->zz_PollTaskStorage;
            AddTask(poll, hotplug_poll_task, NULL);
        }
    }
    Permit();
}

static struct Library* __attribute__((used)) init_device(uint8_t *seg_list asm("a0"), struct Library *dev asm("d0"))
{
    struct Library* ExpansionBase;
    struct ConfigDev* cd = NULL;
    uint8_t* registers = NULL;

    SysBase = get_sysbase();

    if (!(ExpansionBase = (struct Library*)OpenLibrary((uint8_t*)"expansion.library", 0L))) {
        return 0;
    }

#define Z3660_VENDOR        0x144B
#define Z3660_PRODUCT       1

    /* Prefer Zorro III (product 0x4) when available — Z3 bus is ~2× the
     * bandwidth of Z2 and dominates bulk throughput, since the mailbox
     * read/write at base+USB_DATA_ADDRESS is bus-bound rather than CPU-bound.
     * Fall back to Z2 (product 0x3) for cards installed in Z2 slots. */
    if ((cd = (struct ConfigDev*)FindConfigDev(cd, Z3660_VENDOR, Z3660_PRODUCT))) {
        registers = ((uint8_t*)cd->cd_BoardAddr);
    } else {
        CloseLibrary(ExpansionBase);
        return 0;
    }

    struct ZZUSBBase* ZZBase = (struct ZZUSBBase*)dev;
    if (!ZZBase) {
        CloseLibrary(ExpansionBase);
        return 0;
    }

    /* Saved for expunge so the loader can release our segments. */
    DeviceSegList = seg_list;

    dev->lib_Node.ln_Type = NT_DEVICE;
    dev->lib_Node.ln_Name = (char *)device_name;
    dev->lib_Version = DEVICE_VERSION;
    dev->lib_Revision = DEVICE_REVISION;
    dev->lib_IdString = (char *)device_id_string;

    InitSemaphore(&ZZBase->zz_Lock);

    dstr(registers, "[z3660_usb] " XSTR(DEVICE_VERSION) "." XSTR(DEVICE_REVISION) "\r\n");

    struct ZZUSBUnit* unit = &ZZBase->zz_Units[0];
    unit->zz_Registers = registers;
    unit->zz_Enabled = TRUE;
    unit->zz_PortPresent = FALSE;
    unit->zz_PortDead = FALSE;
    unit->zz_RootHubAddr = 0;
    unit->zz_PortChange = 0;
    unit->zz_PortStatus = UPSF_PORT_POWER;
    unit->zz_Speed = 0;
    unit->zz_BulkErrCount = 0;
    for (int ep = 0; ep < 16; ep++)
        unit->zz_IntPending[ep] = NULL;
    RootHubIntPending[0] = NULL;
    RootHubPollDelay[0] = 0;
    reset_int_slots();

    PollBase = ZZBase;
    /*
     * The poll task is created lazily on the first begin_io call,
     * not here. init_device runs during library AutoInit, before
     * MakeLibrary has sealed lib_Sum via SumLibrary; calling AddTask
     * in that window corrupts exec state and gurus with 80000004
     * (library checksum failure). See the matching block in
     * begin_io for the deferred creation.
     */
    ZZBase->zz_PollTask = NULL;

    unit->zz_Unit.unit_MsgPort.mp_MsgList.lh_Head = (struct Node *)&unit->zz_Unit.unit_MsgPort.mp_MsgList.lh_Tail;
    unit->zz_Unit.unit_MsgPort.mp_MsgList.lh_Tail = NULL;
    unit->zz_Unit.unit_MsgPort.mp_MsgList.lh_TailPred = (struct Node *)&unit->zz_Unit.unit_MsgPort.mp_MsgList.lh_Head;
    unit->zz_Unit.unit_flags = 0;
    unit->zz_Unit.unit_OpenCnt = 0;

    CloseLibrary(ExpansionBase);
    return dev;
}

/*
 * Unload helper, callable from both expunge and close. Caller must
 * ensure lib_OpenCnt is zero before invoking. Returns 0 (and re-asserts
 * LIBF_DELEXP) if the poll task is still alive — its Task struct and
 * stack live inside ZZBase, so freeing the base out from under it
 * would crash on the next wake-up. The poll task is created lazily
 * on the first INT transfer and never torn down in current builds,
 * so once it exists the driver effectively becomes non-unloadable;
 * acceptable for a hardware driver normally only unloaded at reboot.
 */
static uint8_t *unload_device(struct Library *dev)
{
    struct ZZUSBBase *ZZBase = (struct ZZUSBBase *)dev;

    if (ZZBase->zz_PollTask) {
        dev->lib_Flags |= LIBF_DELEXP;
        return 0;
    }

    uint8_t *seg = DeviceSegList;

    /*
     * Forbid() prevents another task from FindDevice'ing us between
     * the Remove and FreeMem and dereferencing a half-freed base.
     */
    Forbid();
    Remove(&dev->lib_Node);
    FreeMem((char *)dev - dev->lib_NegSize,
            dev->lib_NegSize + dev->lib_PosSize);
    Permit();
    return seg;
}

static uint8_t* __attribute__((used)) expunge(struct Library *dev asm("a6"))
{
    /*
     * Defer the unload if any unit is still open. Without this guard
     * the caller would FreeMem our base while live IORequests still
     * point at it, crashing on the next BeginIO.
     */
    if (dev->lib_OpenCnt) {
        dev->lib_Flags |= LIBF_DELEXP;
        return 0;
}
    return unload_device(dev);
}

static void __attribute__((used)) open(struct Library *dev asm("a6"), struct IOUsbHWReq *ior asm("a1"),
                 uint32_t unitnum asm("d0"), uint32_t flags asm("d1"))
{
    struct ZZUSBBase* ZZBase = (struct ZZUSBBase*)dev;
    int io_err = IOERR_OPENFAIL;

    if (!ior) {
        return;
    }

    if (unitnum < ZZ_NUM_PORTS) {
        struct ZZUSBUnit* unit = &ZZBase->zz_Units[unitnum];
        if (unit->zz_Enabled) {
            io_err = 0;
            ior->iouh_Req.io_Unit = (struct Unit*)unit;
            ior->iouh_Req.io_Unit->unit_flags = UNITF_ACTIVE;
            ior->iouh_Req.io_Unit->unit_OpenCnt++;
            dev->lib_OpenCnt++;
            /*
             * A pending expunge is being cancelled by this open — clear
             * only on success, otherwise a failed open would silently
             * lose a previous deferred-expunge request.
             */
            dev->lib_Flags &= ~LIBF_DELEXP;
        }
    }

    ior->iouh_Req.io_Error = io_err;
}

static uint8_t* __attribute__((used)) close(struct Library *dev asm("a6"), struct IOUsbHWReq *ior asm("a1"))
{
    if (ior) {
        struct Unit *unit = ior->iouh_Req.io_Unit;
        if (unit && unit != (struct Unit *)-1 && unit->unit_OpenCnt) {
            unit->unit_OpenCnt--;
        }
        /* Sentinel values let exec catch use-after-close on this IOR. */
        ior->iouh_Req.io_Unit = (struct Unit *)-1;
        ior->iouh_Req.io_Device = (struct Device *)-1;
    }

    if (dev->lib_OpenCnt) {
        dev->lib_OpenCnt--;
    }

    if (dev->lib_OpenCnt == 0 && (dev->lib_Flags & LIBF_DELEXP)) {
        return unload_device(dev);
    }
    return 0;
}

/*
 * Abort every queued downstream interrupt IOR for this unit with
 * UHIOERR_USBOFFLINE. Used on hot-unplug from both the hub-INT
 * path and any other future context that detects device loss
 * before poll_int_pending's own offline-mapping sees it.
 *
 * The aborted IORs are appended to the caller's pending-reply
 * array; the actual ReplyMsg happens after zz_Lock is released.
 */
static void abort_int_iors_offline(struct ZZUSBUnit *unit,
                                    struct IOUsbHWReq **aborted,
                                    int *aborted_count,
                                    int aborted_max)
{
    for (int i = 0; i < ZZ_INT_PENDING_SLOTS; i++) {
        struct ZZIntPendingSlot *slot = &IntPendingSlots[i];
        struct IOUsbHWReq *p = slot->ior;
        if (!p || slot->unit != unit) continue;
        clear_int_slot(slot);
        p->iouh_Actual = 0;
        p->iouh_Req.io_Error = UHIOERR_USBOFFLINE;
        if (aborted && aborted_count && *aborted_count < aborted_max) {
            aborted[(*aborted_count)++] = p;
        }
    }

    for (int ep = 1; ep < 16; ep++) {
        struct IOUsbHWReq *p = unit->zz_IntPending[ep];
        if (!p) continue;
        unit->zz_IntPending[ep] = NULL;
        p->iouh_Actual = 0;
        p->iouh_Req.io_Error = UHIOERR_USBOFFLINE;
        if (aborted && aborted_count && *aborted_count < aborted_max) {
            aborted[(*aborted_count)++] = p;
        }
    }
}

static void update_port_state(struct ZZUSBUnit *unit,
                              volatile uint8_t *base,
                              struct IOUsbHWReq **aborted,
                              int *aborted_count,
                              int aborted_max)
{
    struct ZZUSBCommand chk;
    memset(&chk, 0, sizeof(chk));
    chk.cmd = ZZUSB_CMD_CHECK_PORT;

    if (send_usb_cmd(base, &chk, NULL, 0) == ZZUSB_STATUS_OK) {
        /*
         * Firmware says the port is still physically connected.
         * If we previously marked the device dead after an
         * unrecoverable error, refuse to re-enumerate: keep the
         * port reported as empty to Poseidon until the user
         * physically unplugs (which firmware detects as CCS=0
         * and takes the else-branch below). Without this sticky
         * state, a device that keeps babbling would trigger an
         * infinite disconnect/reconnect/babble loop.
         */
        if (unit->zz_PortDead) {
            /* Stay in the "not present" state. No state change. */
            return;
        }

        volatile struct ZZUSBCommand *r =
            (volatile struct ZZUSBCommand*)(base + USB_DATA_ADDRESS);
        if (r->speed == ZZUSB_SPEED_LOW) {
            /*
             * The Zynq/ChipIdea root port does not complete direct
             * low-speed EP0. Hide these devices from Poseidon before it
             * starts enumeration; low-speed devices behind a high-speed
             * hub are still handled through split transactions because
             * the root port speed remains HIGH in that topology.
             */
            if (!unit->zz_PortDead)
                mark_direct_low_speed_unsupported(unit, "LS_ROOT_IGNORE");
            return;
        }

        UWORD port_status = UPSF_PORT_POWER | UPSF_PORT_CONNECTION;
        if (unit->zz_PortPresent && unit->zz_Speed == r->speed) {
            port_status |= unit->zz_PortStatus &
                           (UPSF_PORT_ENABLE | UPSF_PORT_SUSPEND);
        }
        if (r->speed == ZZUSB_SPEED_HIGH) {
            port_status |= UPSF_PORT_HIGH_SPEED;
        } else if (r->speed == ZZUSB_SPEED_LOW) {
            port_status |= UPSF_PORT_LOW_SPEED;
        }
        if (!unit->zz_PortPresent || unit->zz_Speed != r->speed) {
            unit->zz_PortPresent = TRUE;
            unit->zz_Speed = r->speed;
            unit->zz_PortStatus = port_status;
            unit->zz_PortChange = UPSF_C_PORT_CONNECTION;
            trace_port_state(unit, "PORT_CONNECT");
        } else {
            unit->zz_PortStatus = port_status;
        }
    } else {
        /*
         * Firmware says no device on the port (PHYSICAL disconnect).
         * Clear the PortDead sticky state — if the user replugs, we
         * want to re-enumerate normally. Then finish the disconnect
         * bookkeeping if we thought the device was present.
         */
        unit->zz_PortDead = FALSE;
        if (unit->zz_PortPresent) {
            unit->zz_PortPresent = FALSE;
            unit->zz_Speed = 0;
            unit->zz_PortStatus = UPSF_PORT_POWER;
            unit->zz_PortChange = UPSF_C_PORT_CONNECTION;
            unit->zz_BulkErrCount = 0;
            abort_int_iors_offline(unit, aborted, aborted_count, aborted_max);
            trace_port_state(unit, "PORT_DISCONNECT");
        }
    }
}
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
