shanshe/Z3660/z3660-firmware/Z-TURN/vitis_ide/Z3660/src/ethernet.c

/*
 * ethernet.c
 *
 *  Created on: 23 sept. 2022
 *      Author: shanshe
 */

/*
 * MNT ZZ9000 Amiga Graphics and Coprocessor Card Operating System (ZZ9000OS)
 *
 * Copyright (C) 2019, Lukas F. Hartmann <lukas@mntre.com>
 *                     MNT Research GmbH, Berlin
 *                     https://mntre.com
 *
 * More Info: https://mntre.com/zz9000
 *
 * SPDX-License-Identifier: GPL-3.0-or-later
 * GNU General Public License v3.0 or later
 *
 * https://spdx.org/licenses/GPL-3.0-or-later.html
 *
 * Some portions (from EMACPS example code, weird custom license) Copyright (C) 2010 - 2015 Xilinx, Inc.
 *
 */

#include <stdio.h>
#include "platform.h"
#include <xil_cache.h>
#include <xil_mmu.h>
//#include "xparameters.h"
#include "xil_types.h"
#include <xemacps.h>
#include <xscugic.h>
#include "ethernet.h"
#include "interrupt.h"
#include "memorymap.h"
#include "main.h"
#include "debug_console.h"
extern DEBUG_CONSOLE debug_console;

void SetUpSLCRDivisors_z3660(UINTPTR mac_baseaddr, int32_t speed);

static XEmacPs EmacPsInstance;
volatile int semaphore=0;
void DEBUG_ETHERNET(const char *format, ...)
{
   if(debug_console.debug_ethernet==0)
      return;
   while(semaphore==1);
   semaphore=1;
   va_list args;
   va_start(args, format);
   vprintf(format,args);
   va_end(args);
   semaphore=0;
}

#define FRAME_MAX_BACKLOG 64

#define RXBD_CNT       1   /* Number of RxBDs to use */
#define TXBD_CNT       4   /* Number of TxBDs to use */

// could also be 55, 77 (eth1), see interrupts.pdf last page
// XPS_GEM0_INT_ID == 54
#define EMACPS_IRPT_INTR         XPS_GEM0_INT_ID

#define SLCR_LOCK_ADDR           (XPS_SYS_CTRL_BASEADDR + 0x4)
#define SLCR_UNLOCK_ADDR         (XPS_SYS_CTRL_BASEADDR + 0x8)
#define SLCR_GEM0_CLK_CTRL_ADDR  (XPS_SYS_CTRL_BASEADDR + 0x140)
#define SLCR_GEM1_CLK_CTRL_ADDR  (XPS_SYS_CTRL_BASEADDR + 0x144)

#define SLCR_LOCK_KEY_VALUE      0x767B
#define SLCR_UNLOCK_KEY_VALUE    0xDF0D
#define SLCR_ADDR_GEM_RST_CTRL   (XPS_SYS_CTRL_BASEADDR + 0x214)

#define EMACPS_PHY_DELAY_SEC     4 //Amount of time to delay waiting on PHY to reset
#define EMACPS_SLCR_DIV_MASK     0xFC0FC0FF

static int32_t GemVersion;
uint8_t EmacPsMAC[6] = {0x00,0x80,0x10,0x00,0x01,0x00};

static volatile int32_t DeviceErrors = 0;
static volatile uint32_t FramesTx = 0;
static volatile uint32_t FramesRx = 0;
static volatile uint16_t frame_serial = 0;
static volatile uint32_t frames_received = 0;
static volatile uint16_t frames_backlog = 0;
int frames_received_from_backlog = 0;

#define ETH_PHY_TYPE_MICREL    0
#define ETH_PHY_TYPE_MOTORCOMM 1
static int eth_phy_type_ = ETH_PHY_TYPE_MICREL;

uint32_t PhyAddr=0;

typedef char EthernetFrame[XEMACPS_MAX_VLAN_FRAME_SIZE_JUMBO] __attribute__ ((aligned(64)));

volatile char* TxFrame = (char*)(RTG_BASE+TX_FRAME_ADDRESS);      /* Transmit buffer */
volatile char* RxFrame = (char*)(RTG_BASE+RX_FRAME_ADDRESS);      /* Receive buffer */

/*
 * Buffer descriptors are allocated in uncached memory. The memory is made
 * uncached by setting the attributes appropriately in the MMU table.
 */
#define RXBD_SPACE_BYTES XEmacPs_BdRingMemCalc(XEMACPS_BD_ALIGNMENT, RXBD_CNT)
#define TXBD_SPACE_BYTES XEmacPs_BdRingMemCalc(XEMACPS_BD_ALIGNMENT, TXBD_CNT)

#define PHY_DETECT_REG1 2
#define PHY_DETECT_REG2 3
#define PHY_ID_MARVELL        0x141
#define PHY_ID_MICREL_KSZ9031 0x22

static void xEmacPsSendHandler(void *Callback);
static void xEmacPsRecvHandler(void *Callback);
static void xEmacPsErrorHandler(void *Callback, uint8_t direction, uint32_t word);
LONG setup_phy(XEmacPs * EmacPsInstancePtr);
static LONG emacPsSetupIntrSystem(XEmacPs *EmacPsInstancePtr, uint16_t EmacPsIntrId);

void micrel_auto_negotiate(XEmacPs *xemacpsp, uint32_t phy_addr, int eth_phy_type);
uint32_t micrel_auto_negotiate_step2(XEmacPs *xemacpsp, uint32_t phy_addr, int eth_phy_type);

enum {
   ETH_TASK_SETUP,
   ETH_TASK_NEGOTIATE,
   ETH_TASK_INIT,
   ETH_TASK_READY
};

int ethernet_task_state = ETH_TASK_SETUP;

void xEmacPsClkSetup(XEmacPs *EmacPsInstancePtr, uint16_t EmacPsIntrId, int link_speed)
{
   (void)EmacPsInstancePtr;
   uint32_t SlcrTxClkCntrl;
   //uint32_t CrlApbClkCntrl;

   // Check and correct divisors before configuring them
   FixEthernetPLLDivisors_z3660();

   if (GemVersion == 2)
   {
      // SLCR unlock
      *(volatile unsigned int *)(SLCR_UNLOCK_ADDR) = SLCR_UNLOCK_KEY_VALUE;
      if (EmacPsIntrId == XPS_GEM0_INT_ID) {
         // GEM0 clock configuration
         SlcrTxClkCntrl = *(volatile unsigned int *)(SLCR_GEM0_CLK_CTRL_ADDR);

         SlcrTxClkCntrl &= EMACPS_SLCR_DIV_MASK;
         if (link_speed == 100) {
//            SlcrTxClkCntrl |= (XPAR_PS7_ETHERNET_0_ENET_SLCR_100MBPS_DIV1 << 20);
//            SlcrTxClkCntrl |= (XPAR_PS7_ETHERNET_0_ENET_SLCR_100MBPS_DIV0 << 8);
            SetUpSLCRDivisors_z3660(EmacPsInstancePtr->Config.BaseAddress,100);
//            SlcrTxClkCntrl |= (10 << 20);
//            SlcrTxClkCntrl |= (10 << 8);
         } else if (link_speed == 1000) {
//            SlcrTxClkCntrl |= (XPAR_PS7_ETHERNET_0_ENET_SLCR_1000MBPS_DIV1 << 20);
//            SlcrTxClkCntrl |= (XPAR_PS7_ETHERNET_0_ENET_SLCR_1000MBPS_DIV0 << 8);
            SetUpSLCRDivisors_z3660(EmacPsInstancePtr->Config.BaseAddress,1000);
//            SlcrTxClkCntrl |= (1 << 20);
//            SlcrTxClkCntrl |= (10 << 8);
         } else if (link_speed == 10) {
//            SlcrTxClkCntrl |= (XPAR_PS7_ETHERNET_0_ENET_SLCR_10MBPS_DIV1 << 20);
//            SlcrTxClkCntrl |= (XPAR_PS7_ETHERNET_0_ENET_SLCR_10MBPS_DIV0 << 8);
            SetUpSLCRDivisors_z3660(EmacPsInstancePtr->Config.BaseAddress,100);
//            SlcrTxClkCntrl |= (50 << 20);
//            SlcrTxClkCntrl |= (20 << 8);
         } else {
            printf("XEmacPsClkSetup: invalid link speed %d\n", link_speed);
         }
         *(volatile unsigned int *)(SLCR_GEM0_CLK_CTRL_ADDR) = SlcrTxClkCntrl;
      } else if (EmacPsIntrId == XPS_GEM1_INT_ID) {
      }
      // SLCR lock
      *(unsigned int *)(SLCR_LOCK_ADDR) = SLCR_LOCK_KEY_VALUE;
   }
}

static XEmacPs_Bd *BdRxPtr;
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
